scottypres/Arduino-Paragliding-Varios/Sparkfun ESP32 WROOM Vario/KiCAD Files/Buzzer PCB V2/DXFs/Buzzer PCB-FSilkscreen_raster_600dpi_board_aligned.png

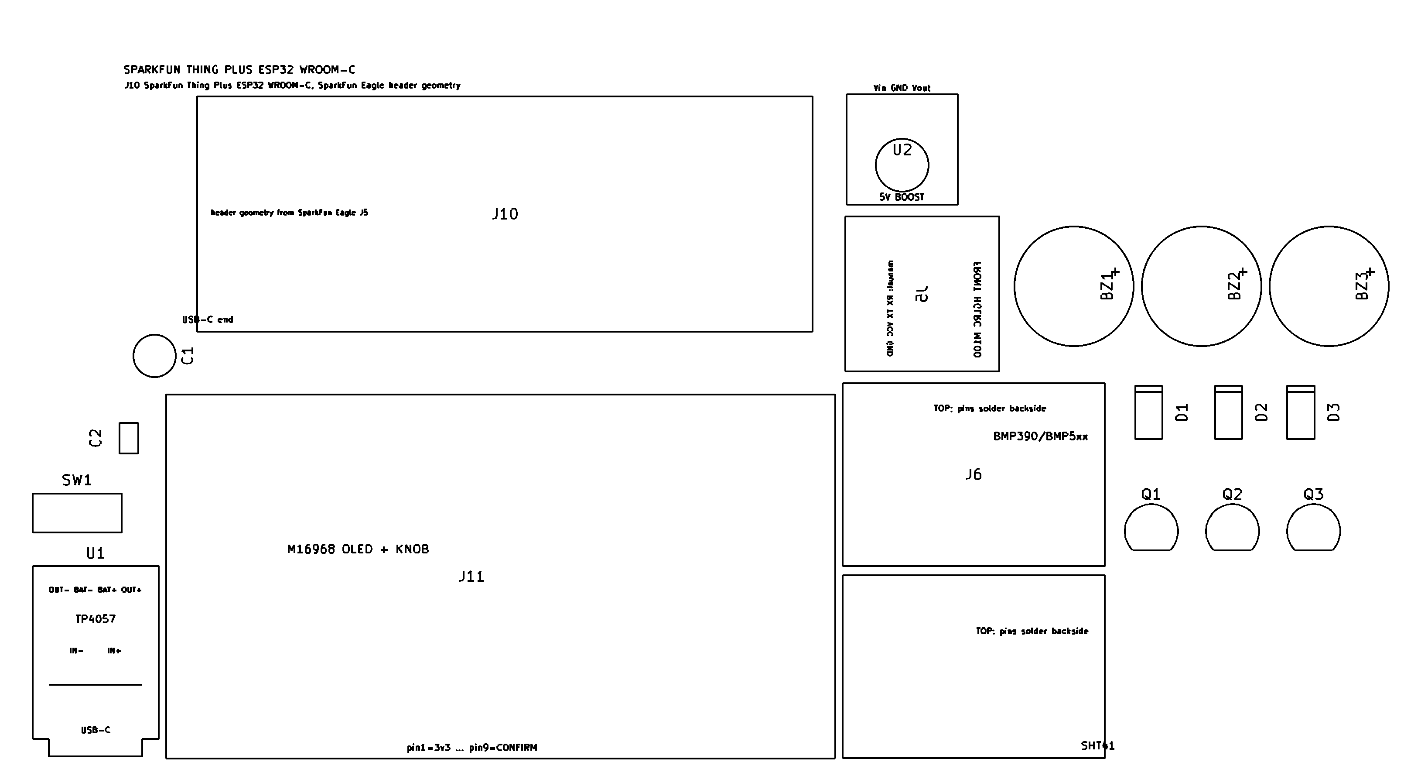
Sparkfun ESP32 WROOM Vario/KiCAD Files/Buzzer PCB V2/DXFs/Buzzer PCB-FSilkscreen_raster_600dpi_board_aligned.png
