scottypres/Arduino-Paragliding-Varios/Sparkfun ESP32 WROOM Vario/KiCAD Files/Buzzer PCB V2/outputs/render/buzzer_v2_top.png

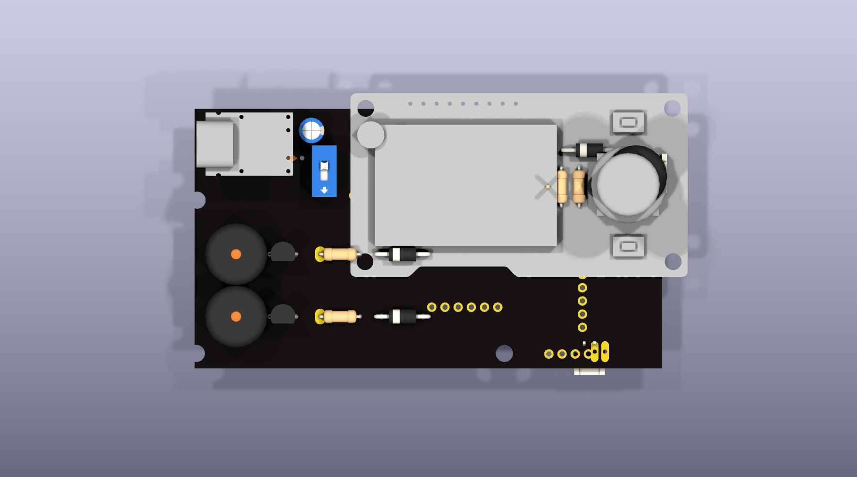
Sparkfun ESP32 WROOM Vario/KiCAD Files/Buzzer PCB V2/outputs/render/buzzer_v2_top.png
