scottypres/Arduino-Paragliding-Varios/Adafruit Feather Mini Vario/KiCAD Files/Component References/HiLetGo TP4057 LiPo_LiIon Charger Drawing HiLetGo TP4057 LiPo LiIon Charger.dxf

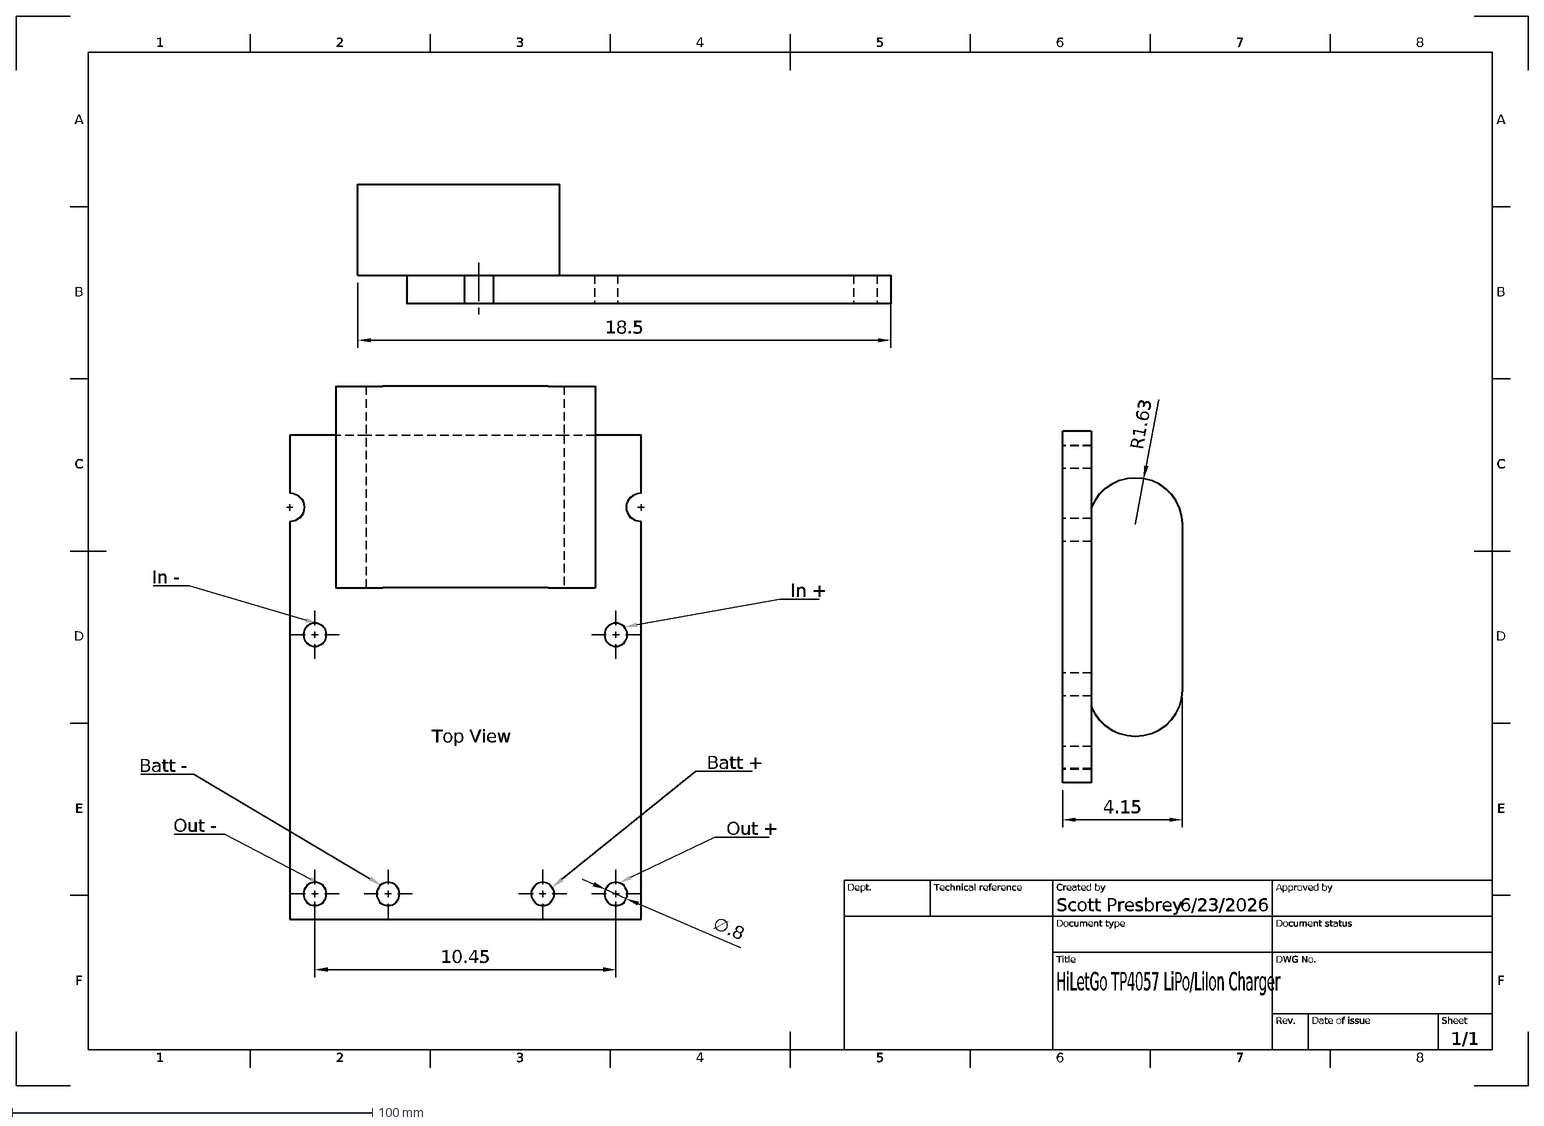
[picture p18: CAD file, 2026-06-23]
Adafruit Feather Mini Vario/KiCAD Files/Component References/HiLetGo TP4057 LiPo_LiIon Charger Drawing HiLetGo TP4057 LiPo LiIon Charger.dxf
1
A
2
3
4
5
6
7
8
B
C
D
E
F
6/23/2026
1/1
HiLetGo TP4057 LiPo/LiIon Charger
Scott Presbrey
Dept.
Technical reference
Created by
Approved by
Document type
Document status
Title
DWG No.
Rev.
Date of issue
Sheet
18.5
4.15
∅.8
R1.63
10.45
Top View
Out -
Batt -
Out +
Batt +
In +
In -
