scottypres/Arduino-Paragliding-Varios/Adafruit Feather Mini Vario/KiCAD Files/Component References/SparkFun 6DoF LSM6DSV16X Qwiic/SparkFun_6DoF_LSM6DSV16X_Qwiic_1x1in_board.step

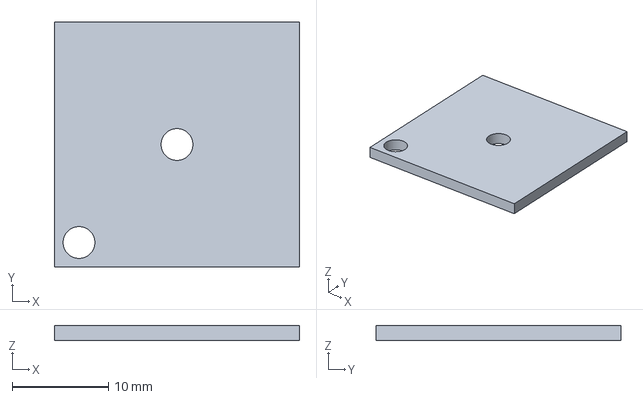
[picture p19: CAD file, 2026-06-27]
Adafruit Feather Mini Vario/KiCAD Files/Component References/SparkFun 6DoF LSM6DSV16X Qwiic/SparkFun_6DoF_LSM6DSV16X_Qwiic_1x1in_board.step
25.4 x 25.4 x 1.60 mm
