scottypres/Arduino-Paragliding-Varios/Sparkfun ESP32 WROOM Vario/3D Printed Case/Top (X2D).3mf

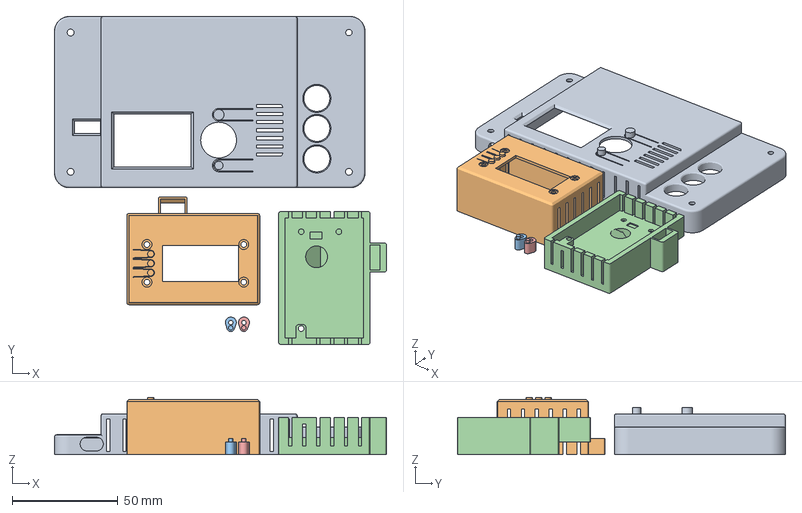
[picture p20: CAD file, 2026-07-03]
Sparkfun ESP32 WROOM Vario/3D Printed Case/Top (X2D).3mf
156.9 x 155.0 x 27.1 mm
3D Printed Case TOP.stl
Feather Case Top.stl
Feather Standoff.stl x 2
Feather Case Bottom.stl
