scottypres/Arduino-Paragliding-Varios/Sparkfun ESP32 WROOM Vario/KiCAD Files/Buzzer PCB V2/DXFs/Buzzer PCB-Edge_Cuts.dxf

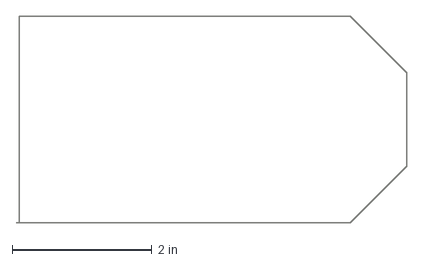
[picture p21: CAD file, 2026-06-26]
Sparkfun ESP32 WROOM Vario/KiCAD Files/Buzzer PCB V2/DXFs/Buzzer PCB-Edge_Cuts.dxf
5.58 x 2.95 in
