scottypres/Arduino-Paragliding-Varios/Sparkfun ESP32 WROOM Vario/KiCAD Files/Buzzer PCB V2/FlatCAM/DXF/Buzzer PCB-NPTH-drl_map.dxf

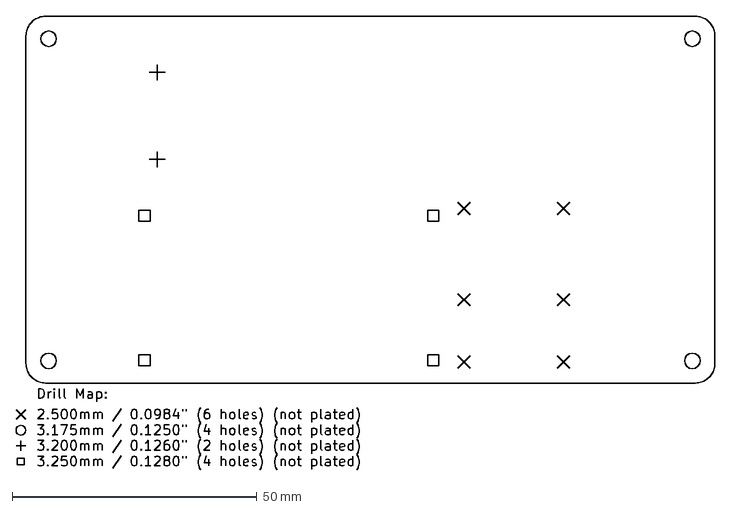
[picture p22: CAD file, 2026-06-26]
Sparkfun ESP32 WROOM Vario/KiCAD Files/Buzzer PCB V2/FlatCAM/DXF/Buzzer PCB-NPTH-drl_map.dxf
142.7 x 92.6 mm
