scottypres/Arduino-Paragliding-Varios/Sparkfun ESP32 WROOM Vario/KiCAD Files/Buzzer PCB V2/outputs/Buzzer_PCB_2p5mm_NPTH_vector_User4.dxf/Buzzer PCB-NPTH_2_5mm_Vector.dxf

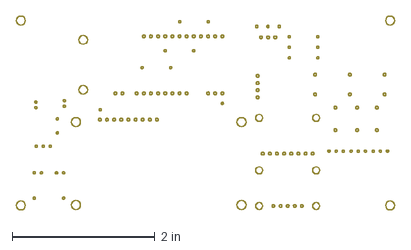
[picture p23: CAD file, 2026-06-26]
Sparkfun ESP32 WROOM Vario/KiCAD Files/Buzzer PCB V2/outputs/Buzzer_PCB_2p5mm_NPTH_vector_User4.dxf/Buzzer PCB-NPTH_2_5mm_Vector.dxf
5.30 x 2.72 in
