scottypres/Arduino-Paragliding-Varios/Sparkfun ESP32 WROOM Vario/KiCAD Files/Buzzer PCB V2/outputs/combined_dxf_parts/Buzzer PCB-Edge_Cuts.dxf

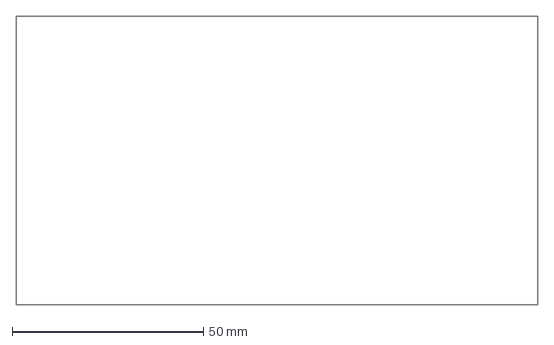
[picture p24: CAD file, 2026-06-25]
Sparkfun ESP32 WROOM Vario/KiCAD Files/Buzzer PCB V2/outputs/combined_dxf_parts/Buzzer PCB-Edge_Cuts.dxf
136.3 x 75.3 mm
