scottypres/Arduino-Paragliding-Varios/Sparkfun ESP32 WROOM Vario/KiCAD Files/Buzzer PCB V2/outputs/dxf_hole_test/Buzzer PCB-F_Cu.dxf

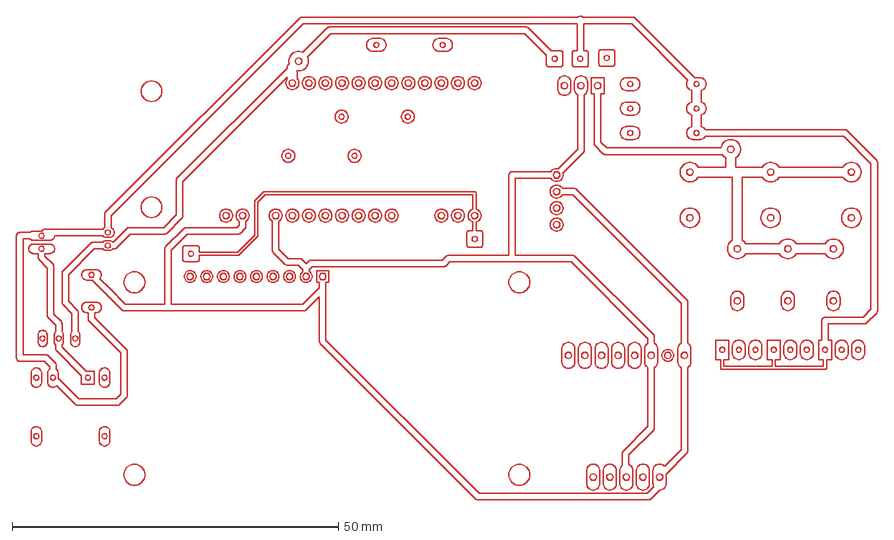
[picture p26: CAD file, 2026-06-25]
Sparkfun ESP32 WROOM Vario/KiCAD Files/Buzzer PCB V2/outputs/dxf_hole_test/Buzzer PCB-F_Cu.dxf
132.0 x 74.2 mm
