scottypres/Arduino-Paragliding-Varios/Sparkfun ESP32 WROOM Vario/KiCAD Files/Buzzer PCB V3 (rerouting traces)/DXFs/Sketch4.dxf

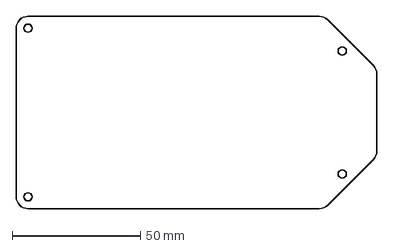
[picture p27: CAD file, 2026-06-26]
Sparkfun ESP32 WROOM Vario/KiCAD Files/Buzzer PCB V3 (rerouting traces)/DXFs/Sketch4.dxf
140.7 x 75.0 mm
