scottypres/Arduino-Paragliding-Varios/Sparkfun ESP32 WROOM Vario/KiCAD Files/Buzzer PCB V3 (rerouting traces)/FlatCAM/Buzzer PCB V3 (rerouted traces)-PTH-drl_map.dxf

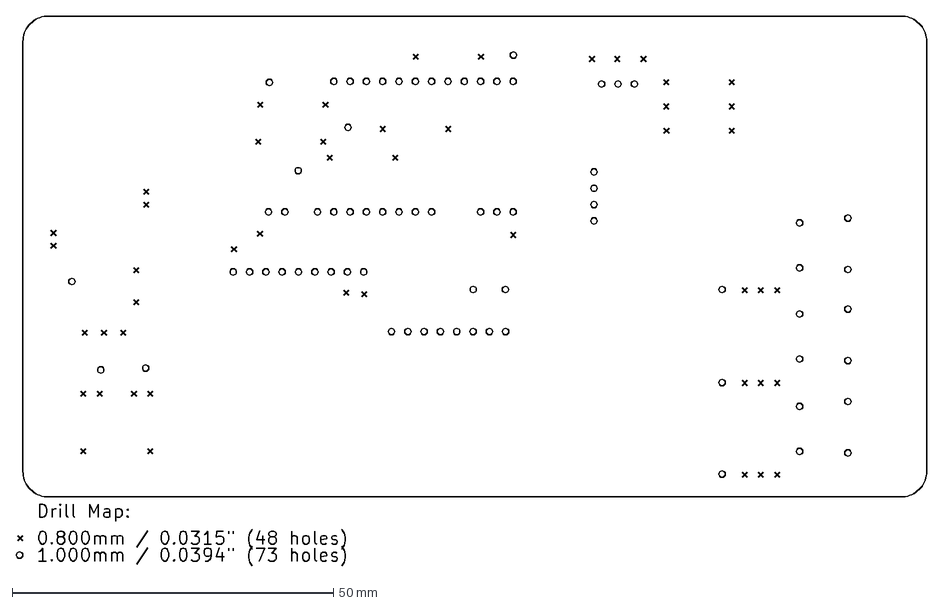
[picture p28: CAD file, 2026-06-28]
Sparkfun ESP32 WROOM Vario/KiCAD Files/Buzzer PCB V3 (rerouting traces)/FlatCAM/Buzzer PCB V3 (rerouted traces)-PTH-drl_map.dxf
141.7 x 85.6 mm
