scottypres/Arduino-Paragliding-Varios/Sparkfun ESP32 WROOM Vario/KiCAD Files/Buzzer PCB V3 (rerouting traces)/outputs/step_after_a1_battery_divider.step

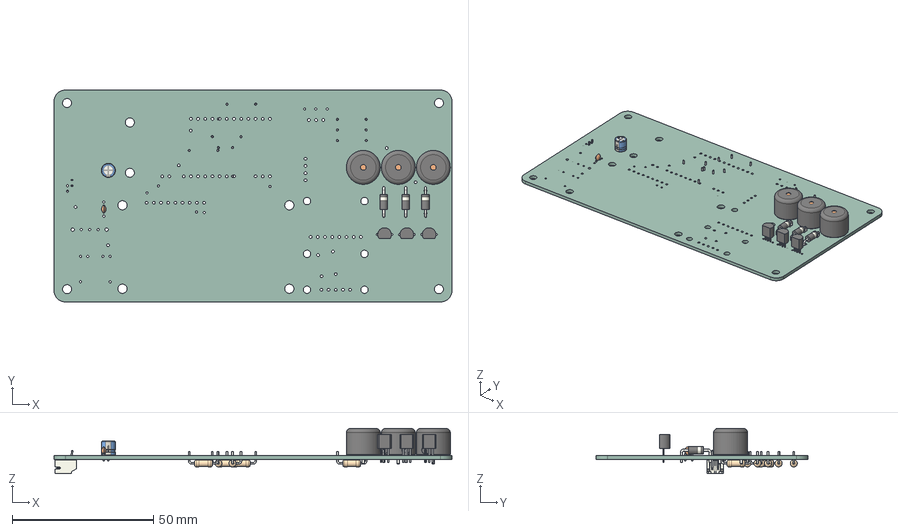
[picture p29: CAD file, 2026-06-27]
Sparkfun ESP32 WROOM Vario/KiCAD Files/Buzzer PCB V3 (rerouting traces)/outputs/step_after_a1_battery_divider.step
140.7 x 74.9 x 16.0 mm
TO-92_Inline_Narrow x 3
C_Disc_D30mm_W16mm_P250mm
D_DO-41_SOD81_P10.16mm_Horizontal x 3
Buzzer_12x95RM76 x 3
CP_Radial_D50mm_P200mm
R_Axial_DIN0207_L63mm_D25mm_P1016mm_Horizontal x 8
JST_S2B_PH_K
Buzzer PCB V3 (rerouted traces)_PCB
