scottypres/Arduino-Paragliding-Varios/Sparkfun ESP32 WROOM Vario/KiCAD Files/Component References/Comidox 5V Booster Board.step

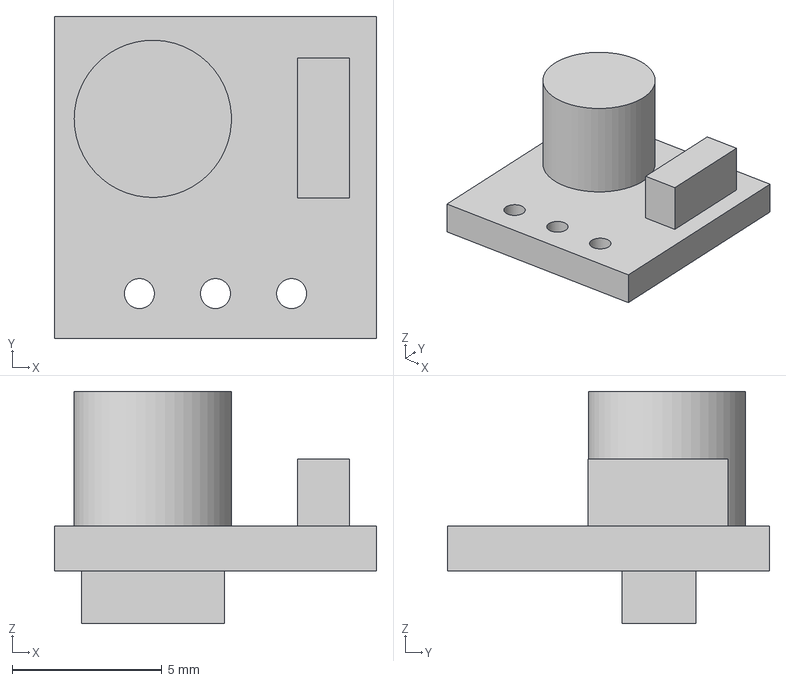
[picture p30: CAD file, 2026-06-23]
Sparkfun ESP32 WROOM Vario/KiCAD Files/Component References/Comidox 5V Booster Board.step
10.8 x 10.8 x 7.75 mm
