scottypres/Arduino-Paragliding-Varios/Adafruit Feather Mini Vario/CAD Files/261 JST PH 2-pin Connector Reference/JST_PH_B2B-PH-K_1x02_P2.00mm_Vertical.step

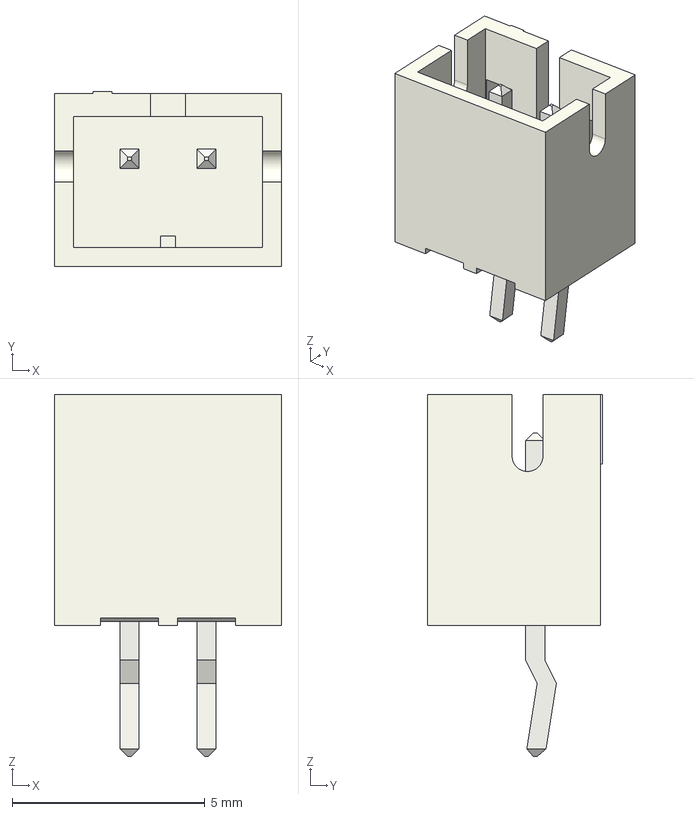
[picture p31: CAD file, 2026-06-20]
Adafruit Feather Mini Vario/CAD Files/261 JST PH 2-pin Connector Reference/JST_PH_B2B-PH-K_1x02_P2.00mm_Vertical.step
5.90 x 4.55 x 9.40 mm
