scottypres/Arduino-Paragliding-Varios/Adafruit Feather Mini Vario/CAD Files/2940 Short Feather Headers - Generic PinSocket Reference/PinSocket_1x12_P2.54mm_Vertical.step

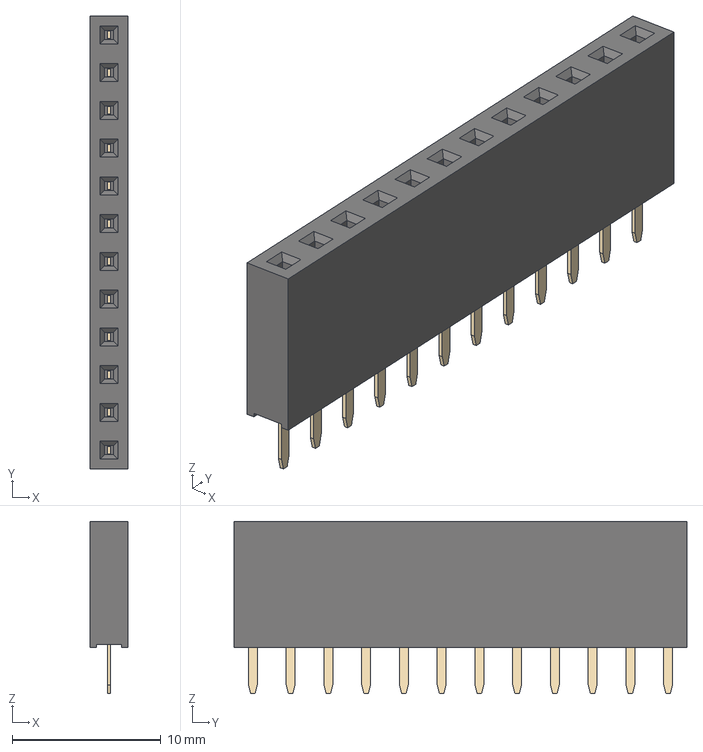
[picture p32: CAD file, 2026-06-20]
Adafruit Feather Mini Vario/CAD Files/2940 Short Feather Headers - Generic PinSocket Reference/PinSocket_1x12_P2.54mm_Vertical.step
2.54 x 30.5 x 11.6 mm
