scottypres/Arduino-Paragliding-Varios/Adafruit Feather Mini Vario/CAD Files/3299 M2.5 Standoff Reference/files/hex-standoff_head.stl

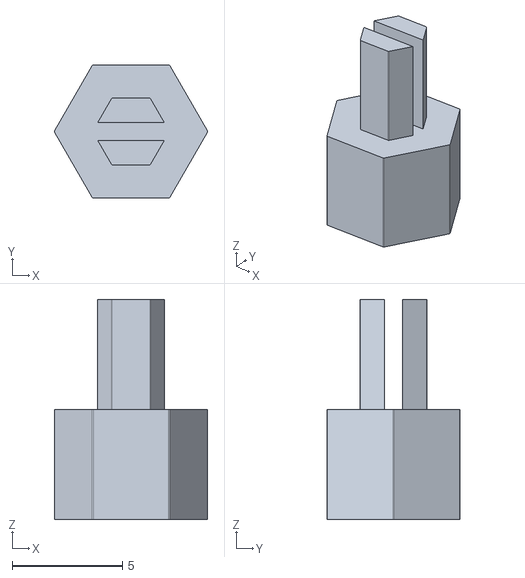
[picture p33: CAD file, 2026-06-20]
Adafruit Feather Mini Vario/CAD Files/3299 M2.5 Standoff Reference/files/hex-standoff_head.stl
6.96 x 6.06 x 10.0
