scottypres/Arduino-Paragliding-Varios/Adafruit Feather Mini Vario/CAD Files/4210_4399 STEMMA QT Cable Connector Reference/JST_SH_SM04B-SRSS-TB_1x04-1MP_P1.00mm_Horizontal.step

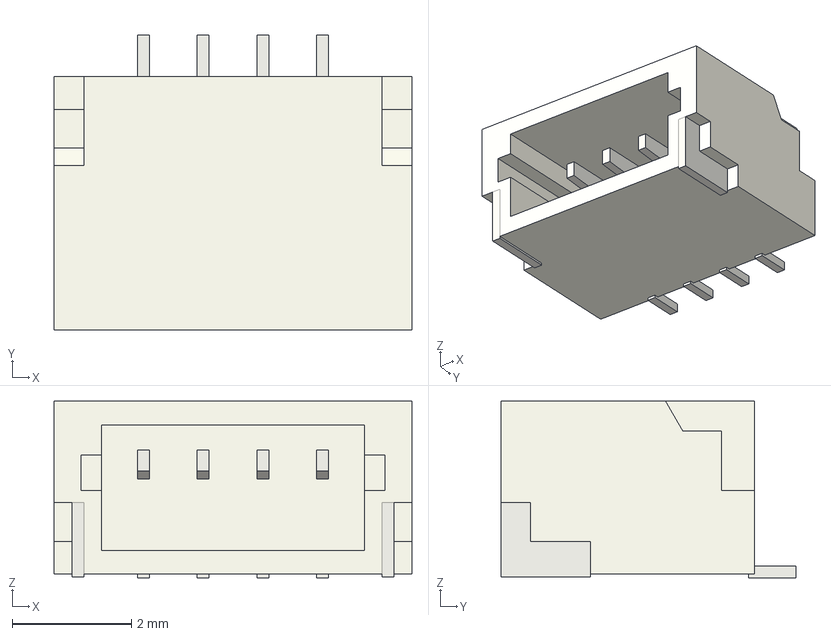
[picture p35: CAD file, 2026-06-20]
Adafruit Feather Mini Vario/CAD Files/4210_4399 STEMMA QT Cable Connector Reference/JST_SH_SM04B-SRSS-TB_1x04-1MP_P1.00mm_Horizontal.step
6.00 x 4.95 x 2.96 mm
