scottypres/Arduino-Paragliding-Varios/Adafruit Feather Mini Vario/CAD Files/4210_4399 STEMMA QT Qwiic JST SH Cables/4210 STEMMA QT Qwiic JST SH 4-pin cable 100mm simplified.step

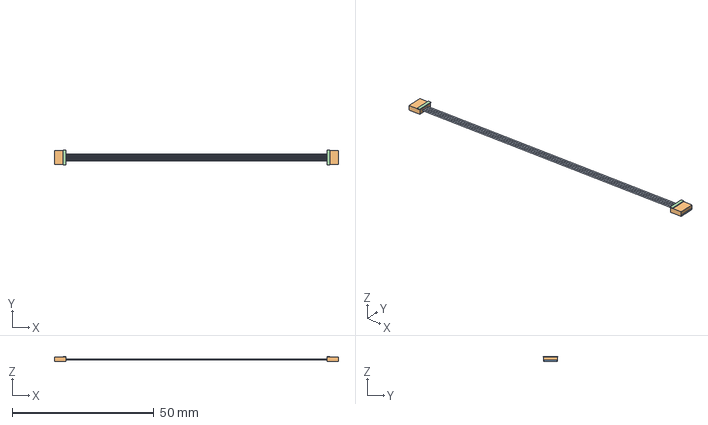
[picture p36: CAD file, 2026-06-20]
Adafruit Feather Mini Vario/CAD Files/4210_4399 STEMMA QT Qwiic JST SH Cables/4210 STEMMA QT Qwiic JST SH 4-pin cable 100mm simplified.step
100.0 x 5.30 x 1.77 mm
