scottypres/Arduino-Paragliding-Varios/Adafruit Feather Mini Vario/CAD Files/Standard 2.54mm Male Headers/PinHeader_1x12_P2.54mm_Vertical.step

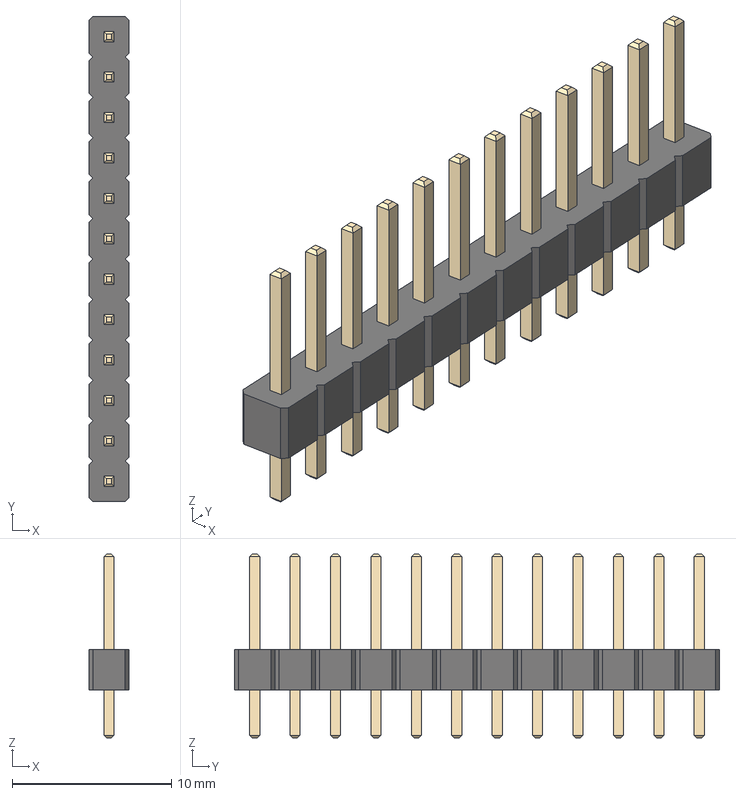
[picture p37: CAD file, 2026-06-20]
Adafruit Feather Mini Vario/CAD Files/Standard 2.54mm Male Headers/PinHeader_1x12_P2.54mm_Vertical.step
2.54 x 30.5 x 11.5 mm
