scottypres/Arduino-Paragliding-Varios/Adafruit Feather Mini Vario/KiCAD Files/Buzzer PCB/STEP/PCB_with_models.step

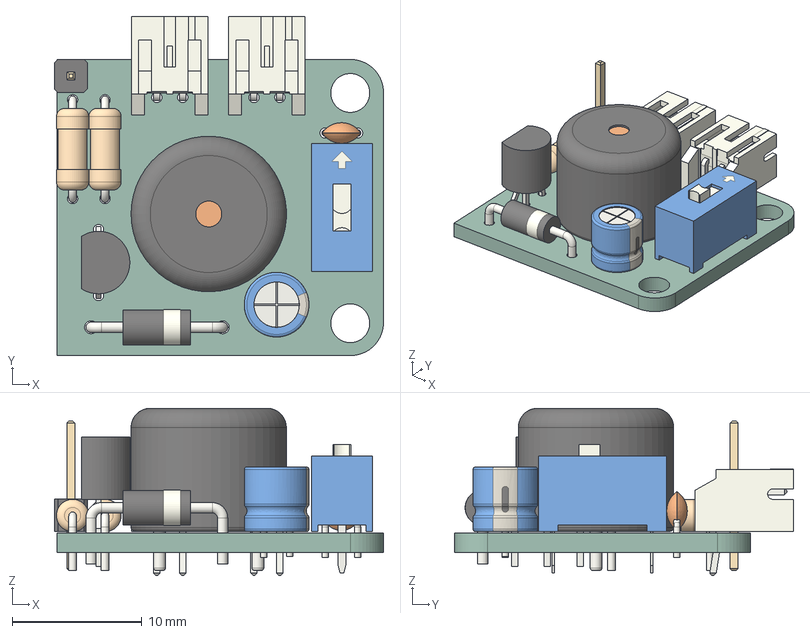
[picture p39: CAD file, 2026-06-21]
Adafruit Feather Mini Vario/KiCAD Files/Buzzer PCB/STEP/PCB_with_models.step
25.4 x 26.2 x 12.9 mm
PinHeader_1x01_P254mm_Vertical
CP_Radial_D50mm_P200mm
C_Disc_D30mm_W16mm_P250mm
R_Axial_DIN0207_L63mm_D25mm_P762mm_Horizontal x 2
SW_DIP_SPSTx01_Slide_978x472mm_W762mm_P254mm
JST_S2B_PH_K x 2
TO-92_Inline_Wide
D_DO-41_SOD81_P10.16mm_Horizontal
Buzzer_12x95RM76
Buzzer PCB_PCB
