scottypres/Arduino-Paragliding-Varios/Adafruit Feather Mini Vario/KiCAD Files/Component References/HiLetGo TP4057 LiPo_LiIon Charger.step

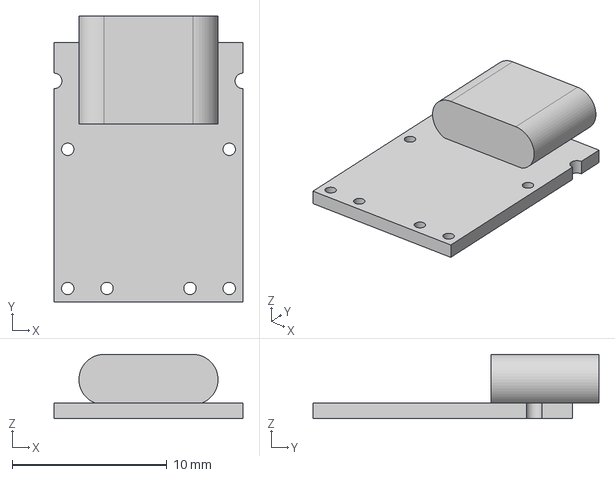
[picture p40: CAD file, 2026-06-23]
Adafruit Feather Mini Vario/KiCAD Files/Component References/HiLetGo TP4057 LiPo_LiIon Charger.step
12.2 x 18.5 x 4.15 mm
