scottypres/Arduino-Paragliding-Varios/Sparkfun ESP32 WROOM Vario/3D Printed Case/Bottom (P1P).3mf

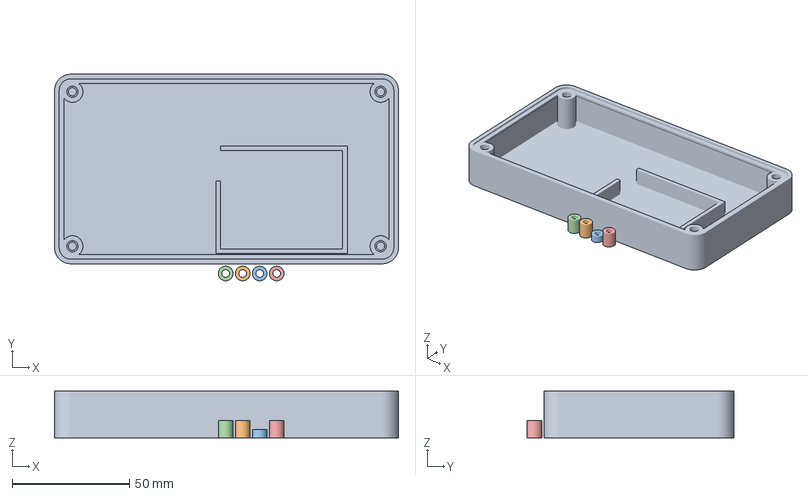
[picture p41: CAD file, 2026-06-28]
Sparkfun ESP32 WROOM Vario/3D Printed Case/Bottom (P1P).3mf
146.7 x 88.1 x 20.0 mm
3D Printed Case.stl_10
3D Printed Case.stl_14
3D Printed Case.stl_15
3D Printed Case.stl_12
3D Printed Case.stl_13
