scottypres/Arduino-Paragliding-Varios/Sparkfun ESP32 WROOM Vario/KiCAD Files/Buzzer PCB V2/FlatCAM/DXF/Buzzer PCB-PTH-drl_map.dxf

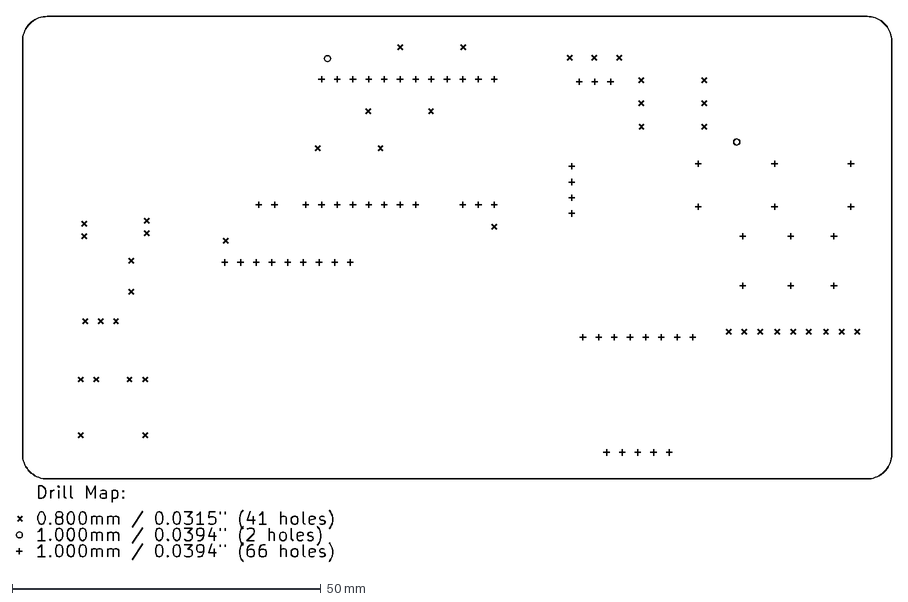
[picture p42: CAD file, 2026-06-26]
Sparkfun ESP32 WROOM Vario/KiCAD Files/Buzzer PCB V2/FlatCAM/DXF/Buzzer PCB-PTH-drl_map.dxf
141.7 x 88.3 mm
