scottypres/Arduino-Paragliding-Varios/Sparkfun ESP32 WROOM Vario/KiCAD Files/Buzzer PCB V3 (rerouting traces)/FlatCAM/Buzzer PCB V3 (rerouted traces)-NPTH-drl_map.dxf

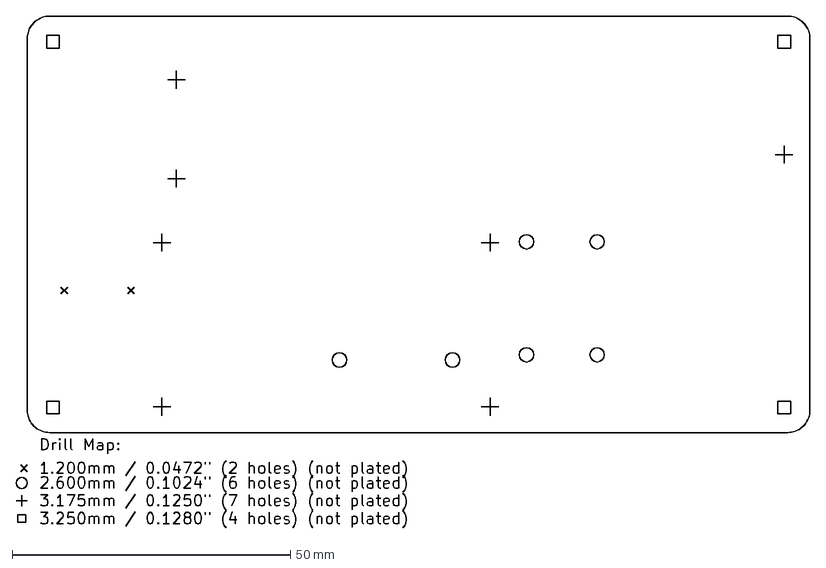
[picture p43: CAD file, 2026-06-28]
Sparkfun ESP32 WROOM Vario/KiCAD Files/Buzzer PCB V3 (rerouting traces)/FlatCAM/Buzzer PCB V3 (rerouted traces)-NPTH-drl_map.dxf
142.7 x 92.0 mm
