scottypres/Arduino-Paragliding-Varios/Adafruit Feather Mini Vario/CAD Files/3299 M2.5 Standoff Reference/files/hex-standoff_foot.stl

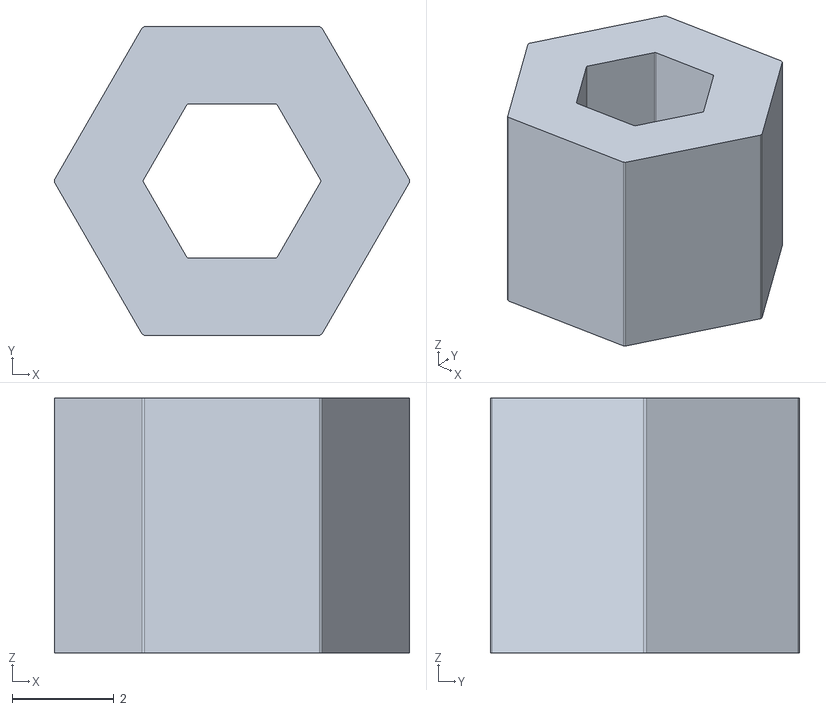
[picture p44: CAD file, 2026-06-20]
Adafruit Feather Mini Vario/CAD Files/3299 M2.5 Standoff Reference/files/hex-standoff_foot.stl
6.96 x 6.06 x 5.00
