scottypres/Arduino-Paragliding-Varios/Adafruit Feather Mini Vario/KiCAD Files/Component References/Comidox 5V Booster Board Drawing Sheet1.dxf

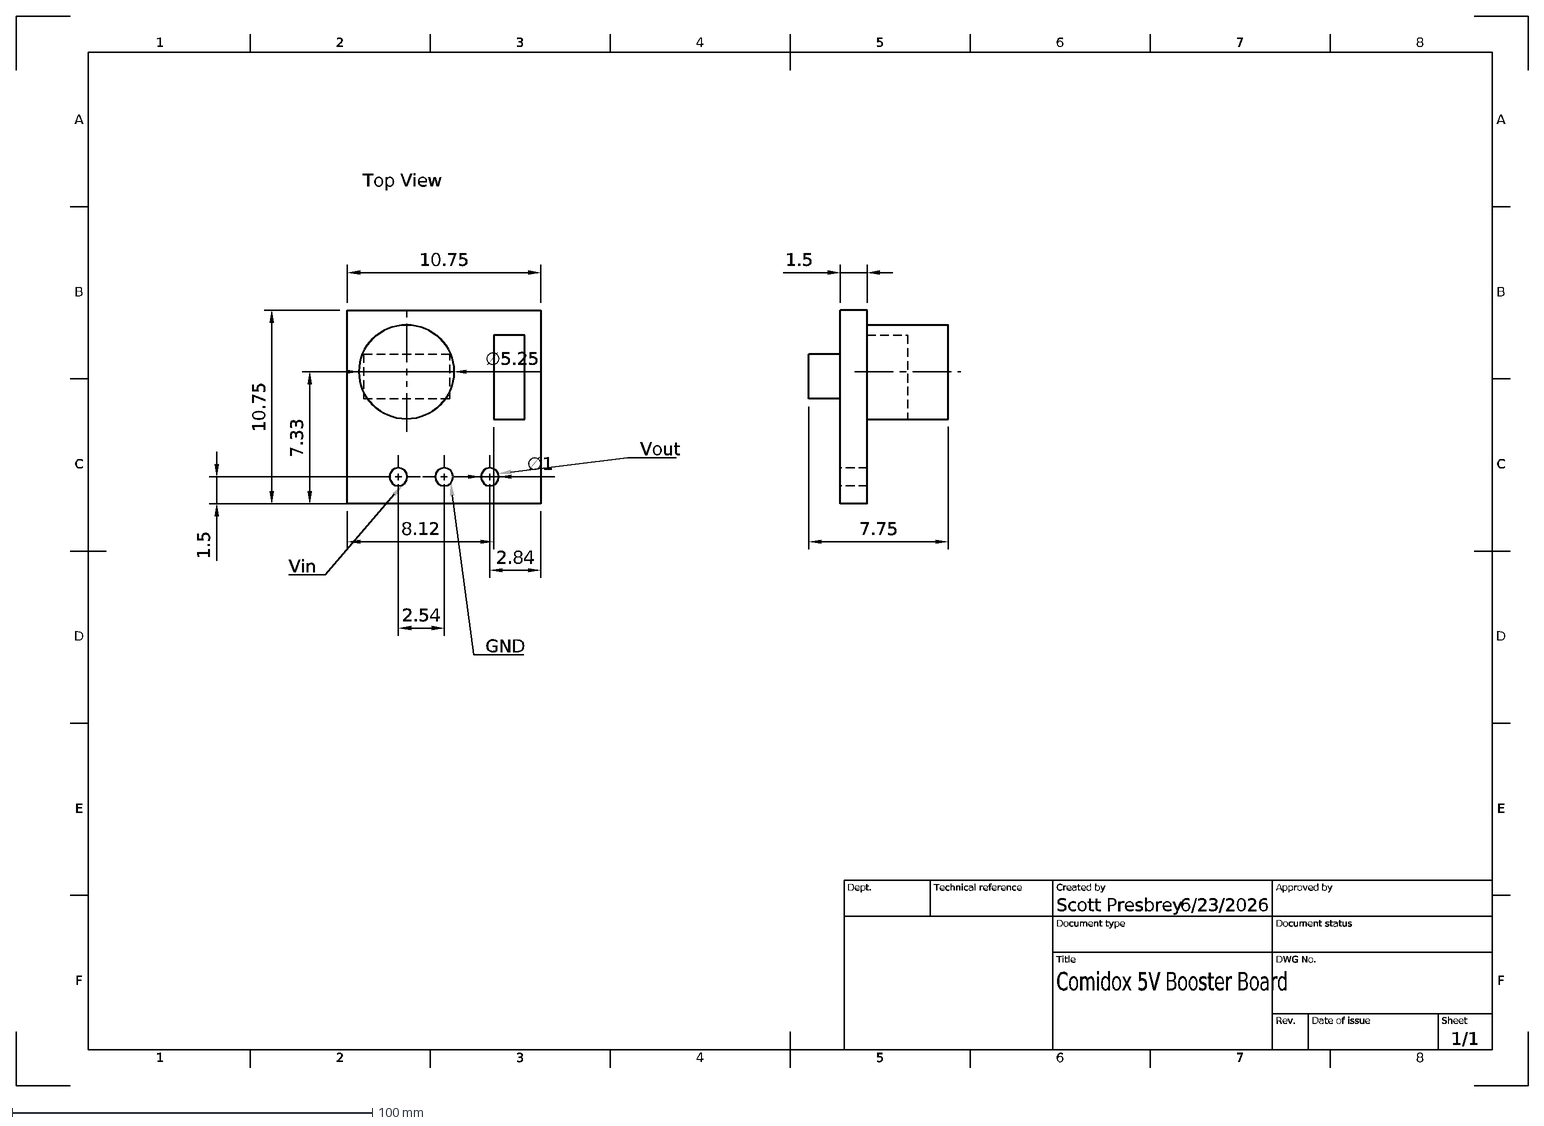
[picture p47: CAD file, 2026-06-23]
Adafruit Feather Mini Vario/KiCAD Files/Component References/Comidox 5V Booster Board Drawing Sheet1.dxf
1
A
2
3
4
5
6
7
8
B
C
D
E
F
6/23/2026
1/1
Comidox 5V Booster Board
Scott Presbrey
Dept.
Technical reference
Created by
Approved by
Document type
Document status
Title
DWG No.
Rev.
Date of issue
Sheet
Top View
10.75
2.54
1.5
2.84
Vin
GND
Vout
7.75
∅1
∅5.25
8.12
7.33
