scottypres/Arduino-Paragliding-Varios/Sparkfun ESP32 WROOM Vario/KiCAD Files/Buzzer PCB V2/DXFs/Buzzer PCB-NPTH-holes-only.dxf

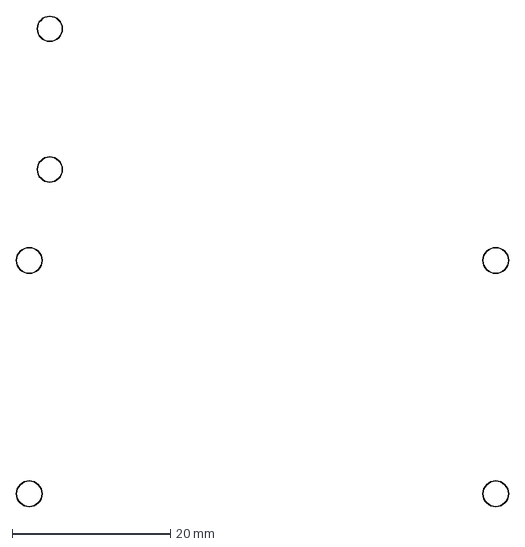
[picture p48: CAD file, 2026-06-25]
Sparkfun ESP32 WROOM Vario/KiCAD Files/Buzzer PCB V2/DXFs/Buzzer PCB-NPTH-holes-only.dxf
62.2 x 62.0 mm
