scottypres/Arduino-Paragliding-Varios/Sparkfun ESP32 WROOM Vario/KiCAD Files/Component References/WWZMDiB SD TF Card Adaptor - SPI - Arduino.step

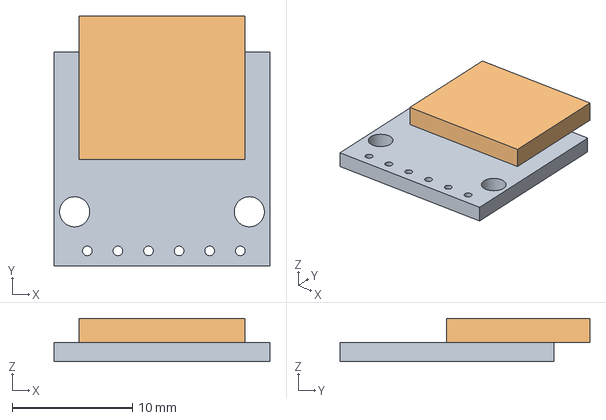
[picture p50: CAD file, 2026-06-23]
Sparkfun ESP32 WROOM Vario/KiCAD Files/Component References/WWZMDiB SD TF Card Adaptor - SPI - Arduino.step
17.9 x 20.8 x 3.60 mm
