scottypres/Arduino-Paragliding-Varios/Adafruit Feather Mini Vario/CAD Files/3299 M2.5 Standoff Reference/M2.5 female-female hex standoff 8mm.step

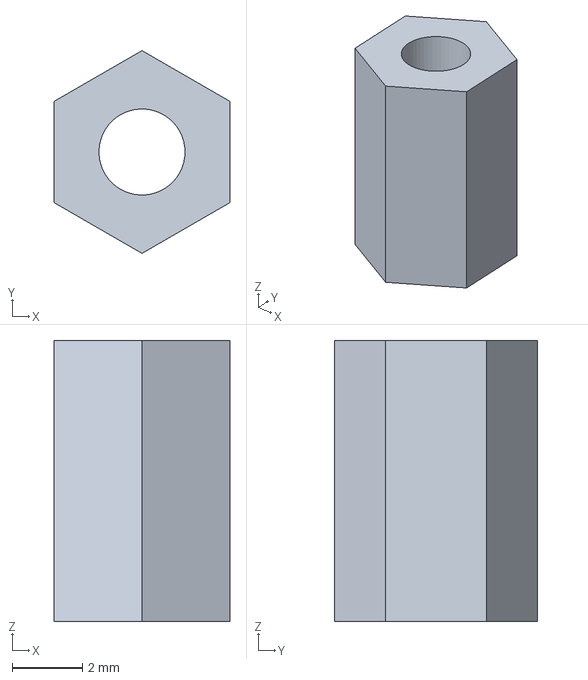
[picture p51: CAD file, 2026-06-20]
Adafruit Feather Mini Vario/CAD Files/3299 M2.5 Standoff Reference/M2.5 female-female hex standoff 8mm.step
5.00 x 5.77 x 8.00 mm
