scottypres/Arduino-Paragliding-Varios/Sparkfun ESP32 WROOM Vario/KiCAD Files/Buzzer PCB V3 (rerouting traces)/DXFs/Buzzer PCB-ALL-holes-only.dxf

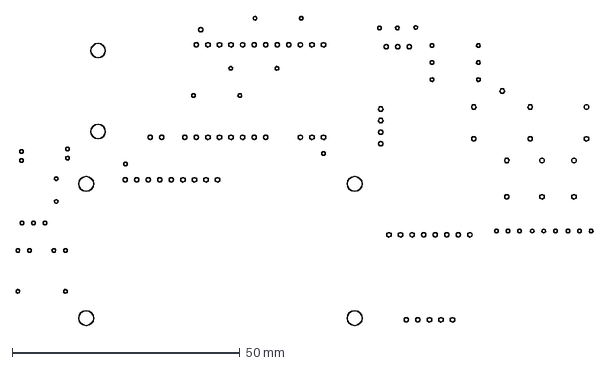
[picture p52: CAD file, 2026-06-25]
Sparkfun ESP32 WROOM Vario/KiCAD Files/Buzzer PCB V3 (rerouting traces)/DXFs/Buzzer PCB-ALL-holes-only.dxf
126.8 x 67.9 mm
