scottypres/Arduino-Paragliding-Varios/Sparkfun ESP32 WROOM Vario/KiCAD Files/Component References/WWZMDiB SD TF Card Adaptor - SPI - Arduino Drawing Sheet1.dxf

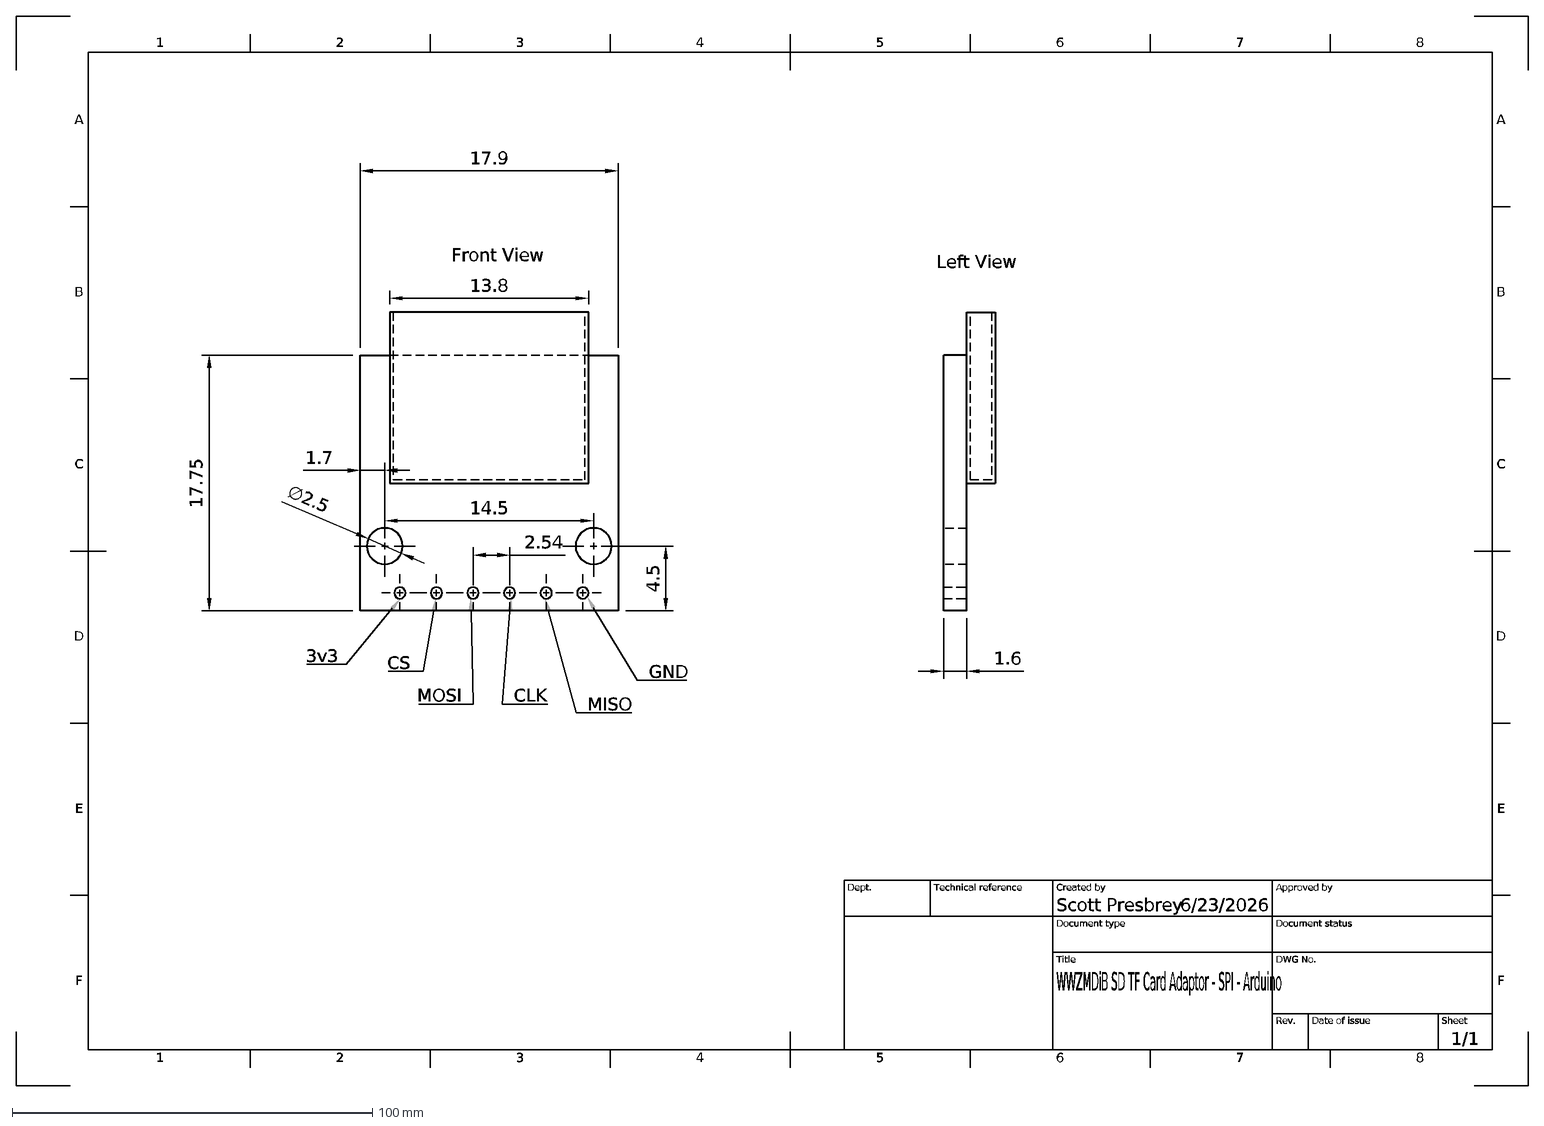
[picture p53: CAD file, 2026-06-23]
Sparkfun ESP32 WROOM Vario/KiCAD Files/Component References/WWZMDiB SD TF Card Adaptor - SPI - Arduino Drawing Sheet1.dxf
1
A
2
3
4
5
6
7
8
B
C
D
E
F
6/23/2026
1/1
WWZMDiB SD TF Card Adaptor - SPI - Arduino
Scott Presbrey
Dept.
Technical reference
Created by
Approved by
Document type
Document status
Title
DWG No.
Rev.
Date of issue
Sheet
3v3
CS
MOSI
CLK
MISO
GND
Front View
Left View
17.75
17.9
13.8
1.6
∅2.5
1.7
14.5
4.5
2.54
