scottypres/Arduino-Paragliding-Varios/Adafruit Feather Mini Vario/CAD Files/3299 M2.5 Standoff Reference/M2.5 male-female hex standoff 6mm body.step

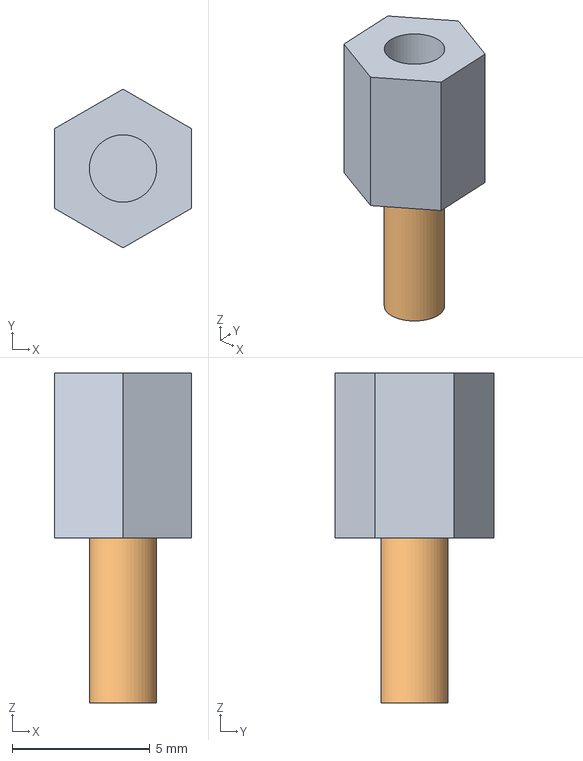
[picture p54: CAD file, 2026-06-20]
Adafruit Feather Mini Vario/CAD Files/3299 M2.5 Standoff Reference/M2.5 male-female hex standoff 6mm body.step
5.00 x 5.77 x 12.0 mm
