scottypres/Arduino-Paragliding-Varios/Sparkfun ESP32 WROOM Vario/KiCAD Files/Buzzer PCB V3 (rerouting traces)/DXFs/Buzzer PCB-NPTH-drl_map.dxf

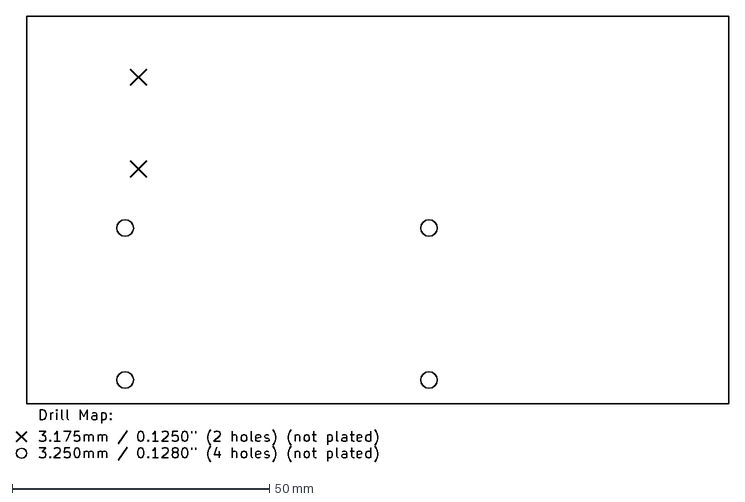
[picture p55: CAD file, 2026-06-25]
Sparkfun ESP32 WROOM Vario/KiCAD Files/Buzzer PCB V3 (rerouting traces)/DXFs/Buzzer PCB-NPTH-drl_map.dxf
138.3 x 86.6 mm
