scottypres/Arduino-Paragliding-Varios/Sparkfun ESP32 WROOM Vario/KiCAD Files/Buzzer PCB V2/DXFs/Buzzer PCB-PTH-drl_map.dxf

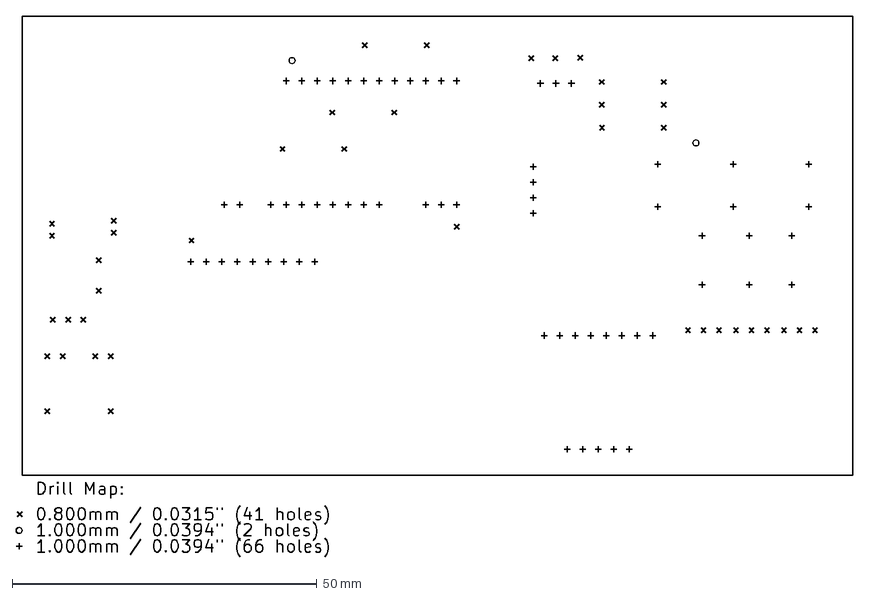
[picture p57: CAD file, 2026-06-25]
Sparkfun ESP32 WROOM Vario/KiCAD Files/Buzzer PCB V2/DXFs/Buzzer PCB-PTH-drl_map.dxf
137.3 x 88.7 mm
