scottypres/Arduino-Paragliding-Varios/Adafruit Feather Mini Vario/KiCAD Files/Component References/6313 OLED FeatherWing EagleCAD/Adafruit 128x64 OLED FeatherWing.brd

## EAGLE design Adafruit Feather Mini Vario/KiCAD Files/Component References/6313 OLED FeatherWing EagleCAD/Adafruit 128x64 OLED FeatherWing.brd (2026-06-20)

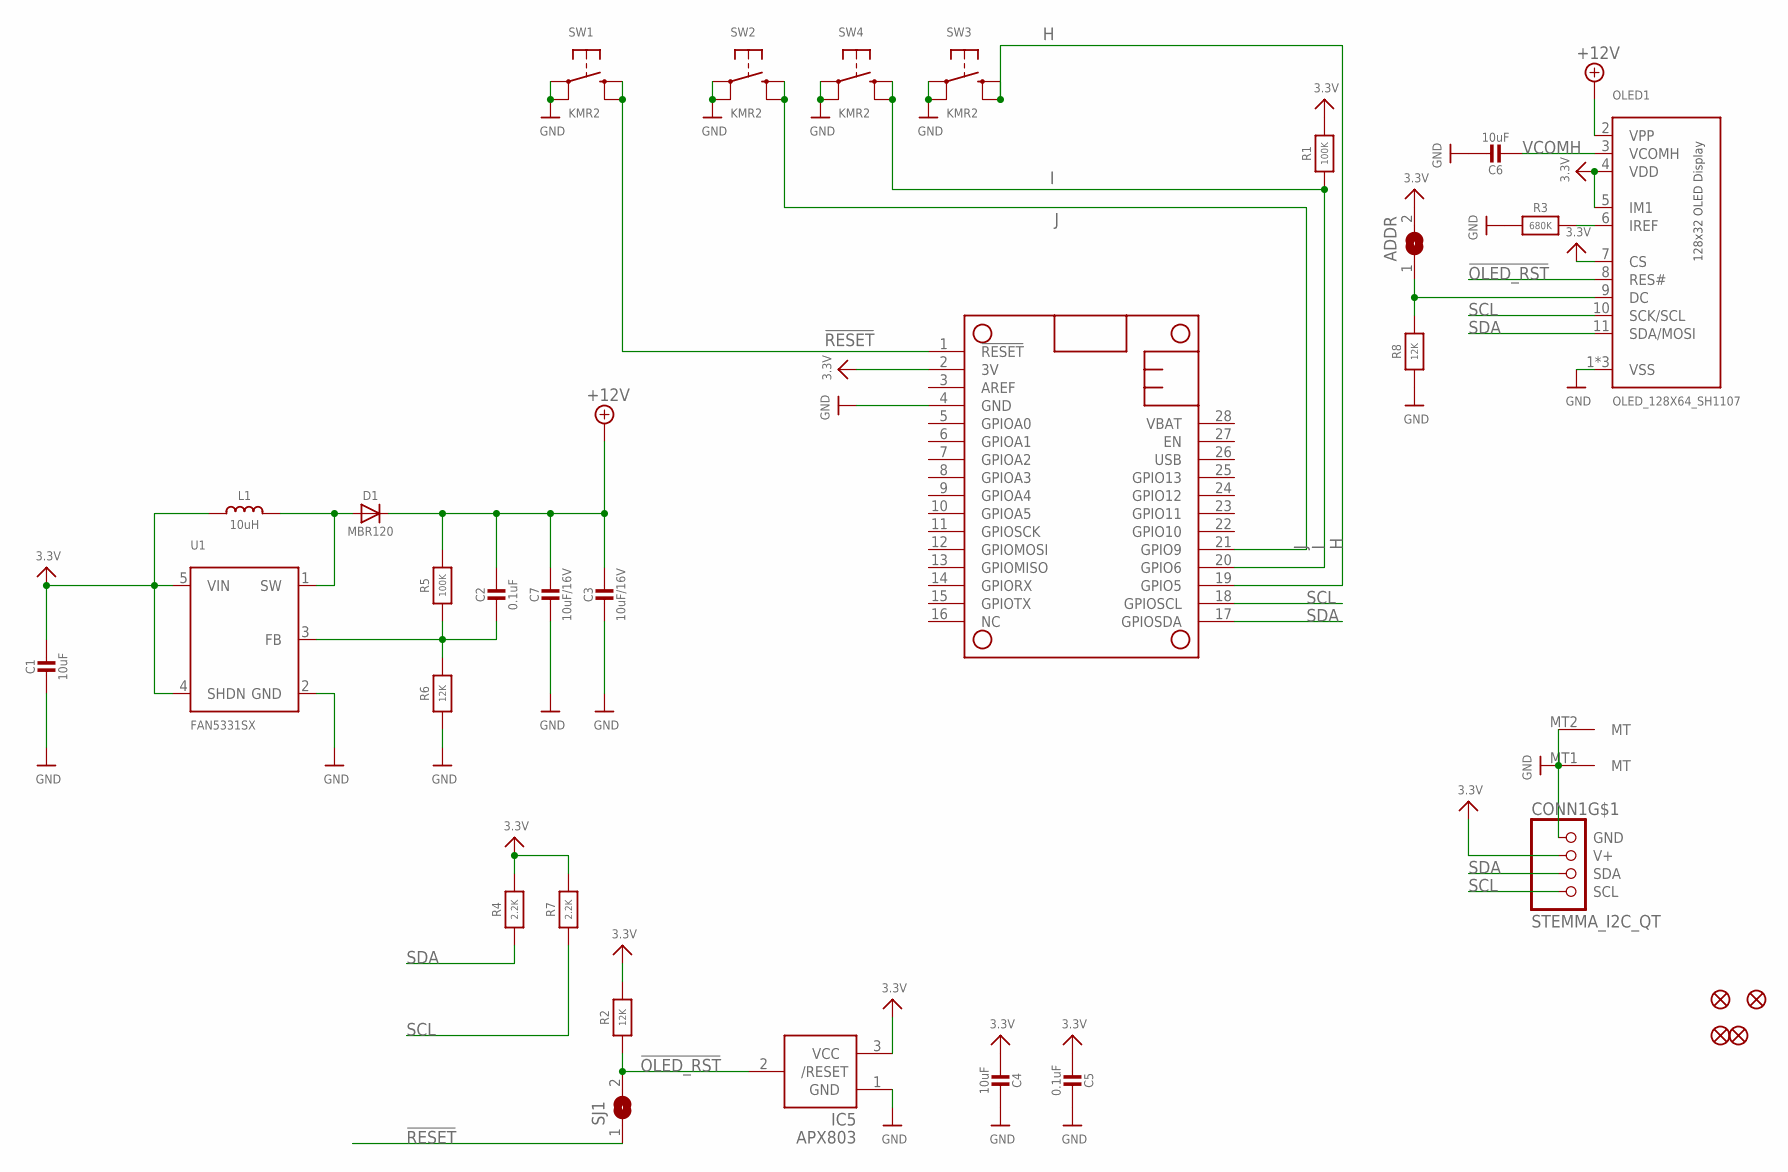
[picture p83: schematic Adafruit 128x64 OLED FeatherWing.sch]

Parts:
ADDR: SOLDERJUMPER; SOLDERJUMPER_ARROW_NOPASTE
C1, C4, C6: 10uF; 0805-NO
C2, C5: 0.1uF; 0603-NO
C3, C7: 10uF/16V; 0805-NO
CONN1: STEMMA_I2C_QT; JST_SH4
D1: MBR120; SOD-123
FID1, FID2, FID3, FID4: FIDUCIAL_1MM
IC5: APX803; SOT23
L1: 10uH; INDUCTOR_1007
MS1: FEATHERWING_NODIM
OLED1: OLED_128X64_SH1107; QT1107P11A
R1, R5: 100K; 0603-NO
R2, R6, R8: 12K; 0603-NO
R3: 680K; 0603-NO
R4, R7: 2.2K; 0603-NO
SJ1: SOLDERJUMPERCLOSED; SOLDERJUMPER_CLOSEDWIRE
SW1, SW2, SW3, SW4: KMR2; BTN_KMR2_4.6X2.8
U1: FAN5331SX; SOT23-5

Connections:
3.3V: ADDR.2, C1.1, C4.2, C5.2, CONN1.2 (V+), IC5.3 (VCC), L1.P$1 (1), MS1.2 (3V), OLED1.4 (VDD), OLED1.5 (IM1), OLED1.7 (CS), R1.2, R2.2, R4.2, R7.2, U1.4 (SHDN), U1.5 (VIN)
!OLED_RST: IC5.2 (/RESET), OLED1.8 (RES#), R2.1, SJ1.2
!RESET: MS1.1 (!RESET), SJ1.1, SW1.B (S), SW1.B' (S1)
+12V: C2.1, C3.1, C7.1, D1.C, OLED1.2 (VPP), R5.2
GND: C1.2, C3.2, C4.1, C5.1, C6.1, C7.2, CONN1.1 (GND), CONN1.MT1 (MT), CONN1.MT2 (MT), IC5.1 (GND), MS1.4 (GND), OLED1.1 (VSS), OLED1.12 (VSS), OLED1.13 (VSS), R3.1, R6.1, R8.1, SW1.A, SW1.A' (P1), SW2.A, SW2.A' (P1), SW3.A, SW3.A' (P1), SW4.A, SW4.A' (P1), U1.2 (GND)
H: MS1.19 (GPIO5), SW3.B (S), SW3.B' (S1)
I: MS1.20 (GPIO6), R1.1, SW4.B (S), SW4.B' (S1)
J: MS1.21 (GPIO9), SW2.B (S), SW2.B' (S1)
unnamed: D1.A, L1.P$2 (2), U1.1 (SW)
unnamed: ADDR.1, OLED1.9 (DC), R8.2
unnamed: C2.2, R5.1, R6.2, U1.3 (FB)
unnamed: OLED1.6 (IREF), R3.2
SCL: CONN1.4 (SCL), MS1.18 (GPIOSCL), OLED1.10 (SCK/SCL), R7.1
SDA: CONN1.3 (SDA), MS1.17 (GPIOSDA), OLED1.11 (SDA/MOSI), R4.1
VCOMH: C6.2, OLED1.3 (VCOMH)

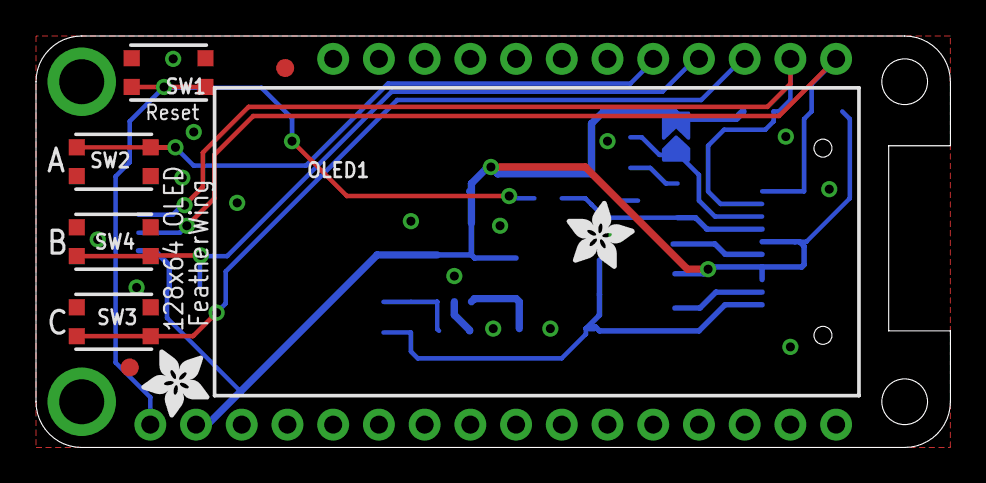
[picture p84: board Adafruit 128x64 OLED FeatherWing.brd from above]

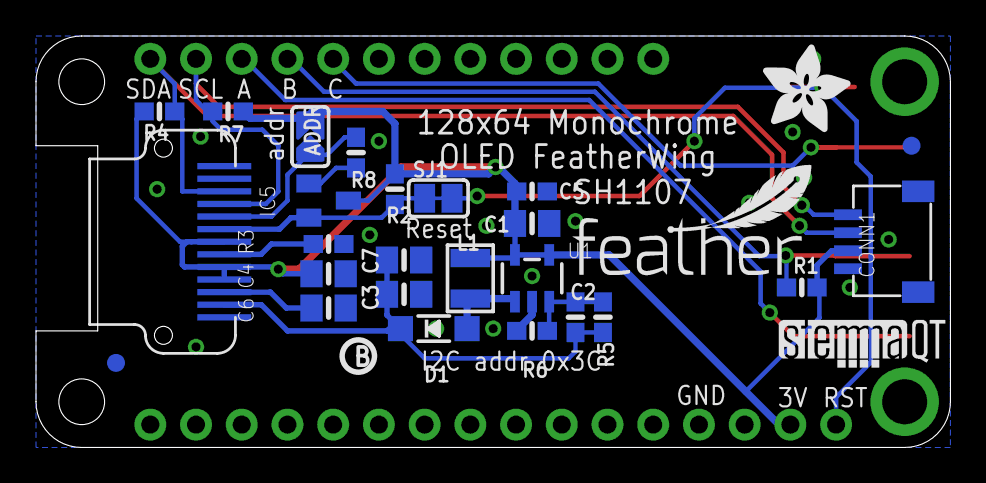
[picture p85: board Adafruit 128x64 OLED FeatherWing.brd from below]

Board: 2 copper layers, 50.8 x 22.9 mm, 38 parts (28 on the bottom side), 15 nets.

Other parts of the board:
U$8: ADAFRUIT_5MM
U$14: PCBFEAT-REV-040
U$16, U$37: ADAFRUIT_3.5MM
U$35: STEMMAQT
U$36: FEATHERLOGO_SMALL
