scottypres/Arduino-Paragliding-Varios/Adafruit Feather Mini Vario/KiCAD Files/Component References/SparkFun_Qwiic_OLED_1.3in/Hardware/Production/Qwiic_OLED_1.3in-Panel.brd

## EAGLE design Adafruit Feather Mini Vario/KiCAD Files/Component References/SparkFun_Qwiic_OLED_1.3in/Hardware/Production/Qwiic_OLED_1.3in-Panel.brd (2026-06-28)

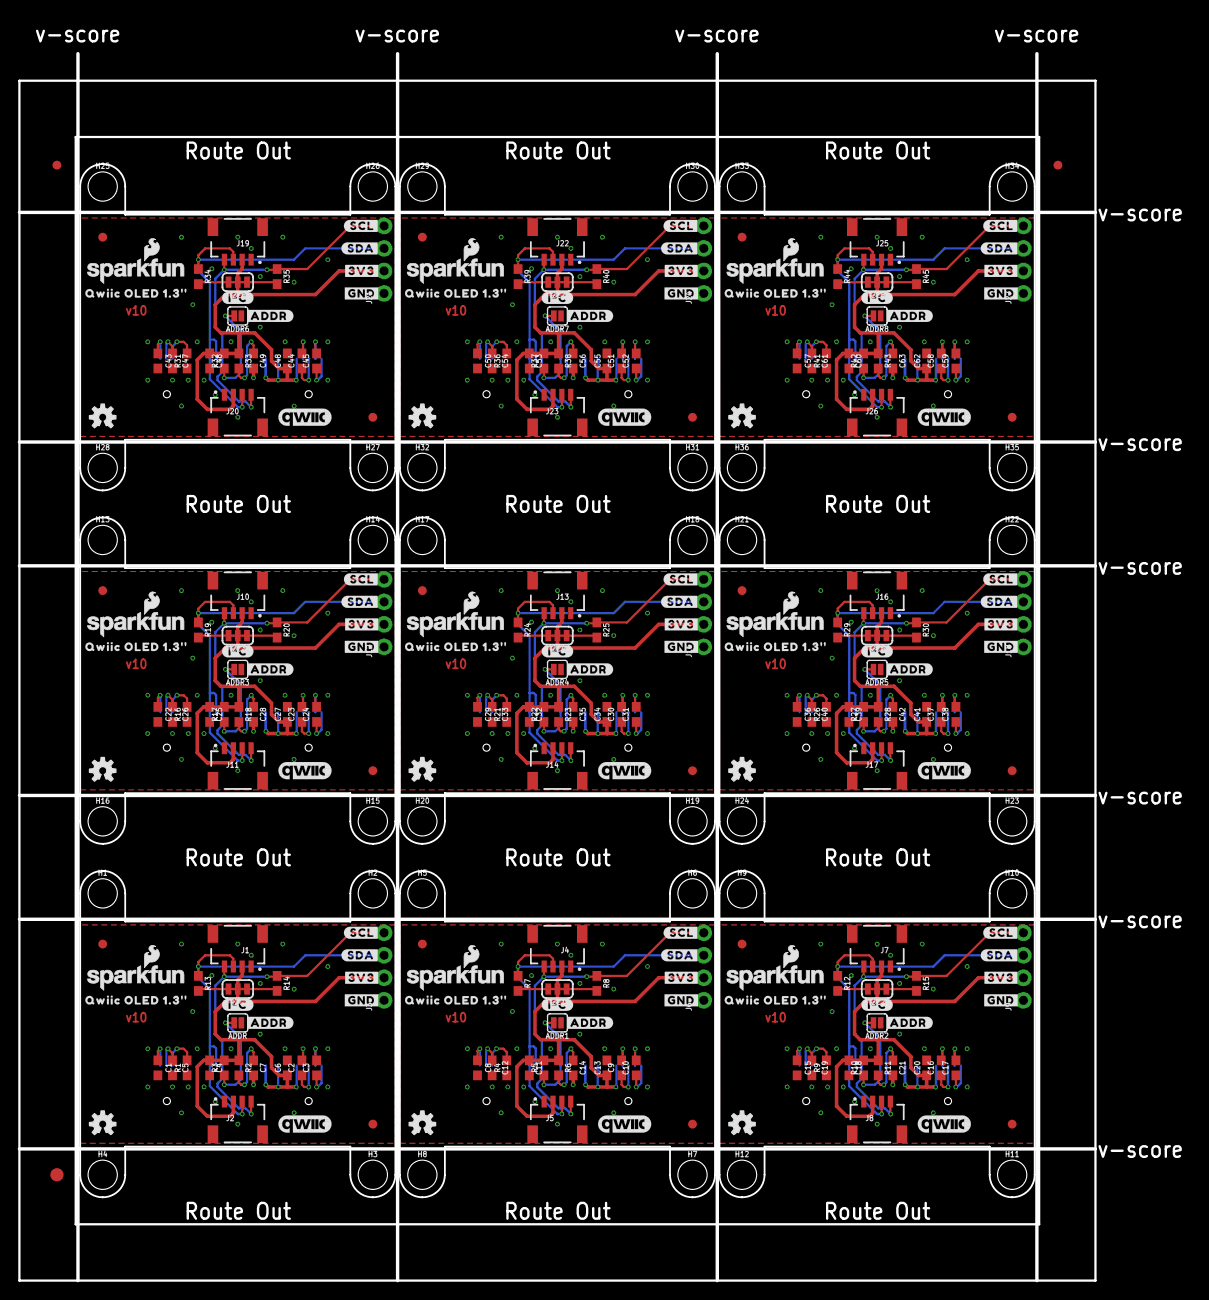
[picture p86: board Qwiic_OLED_1.3in-Panel.brd from above]

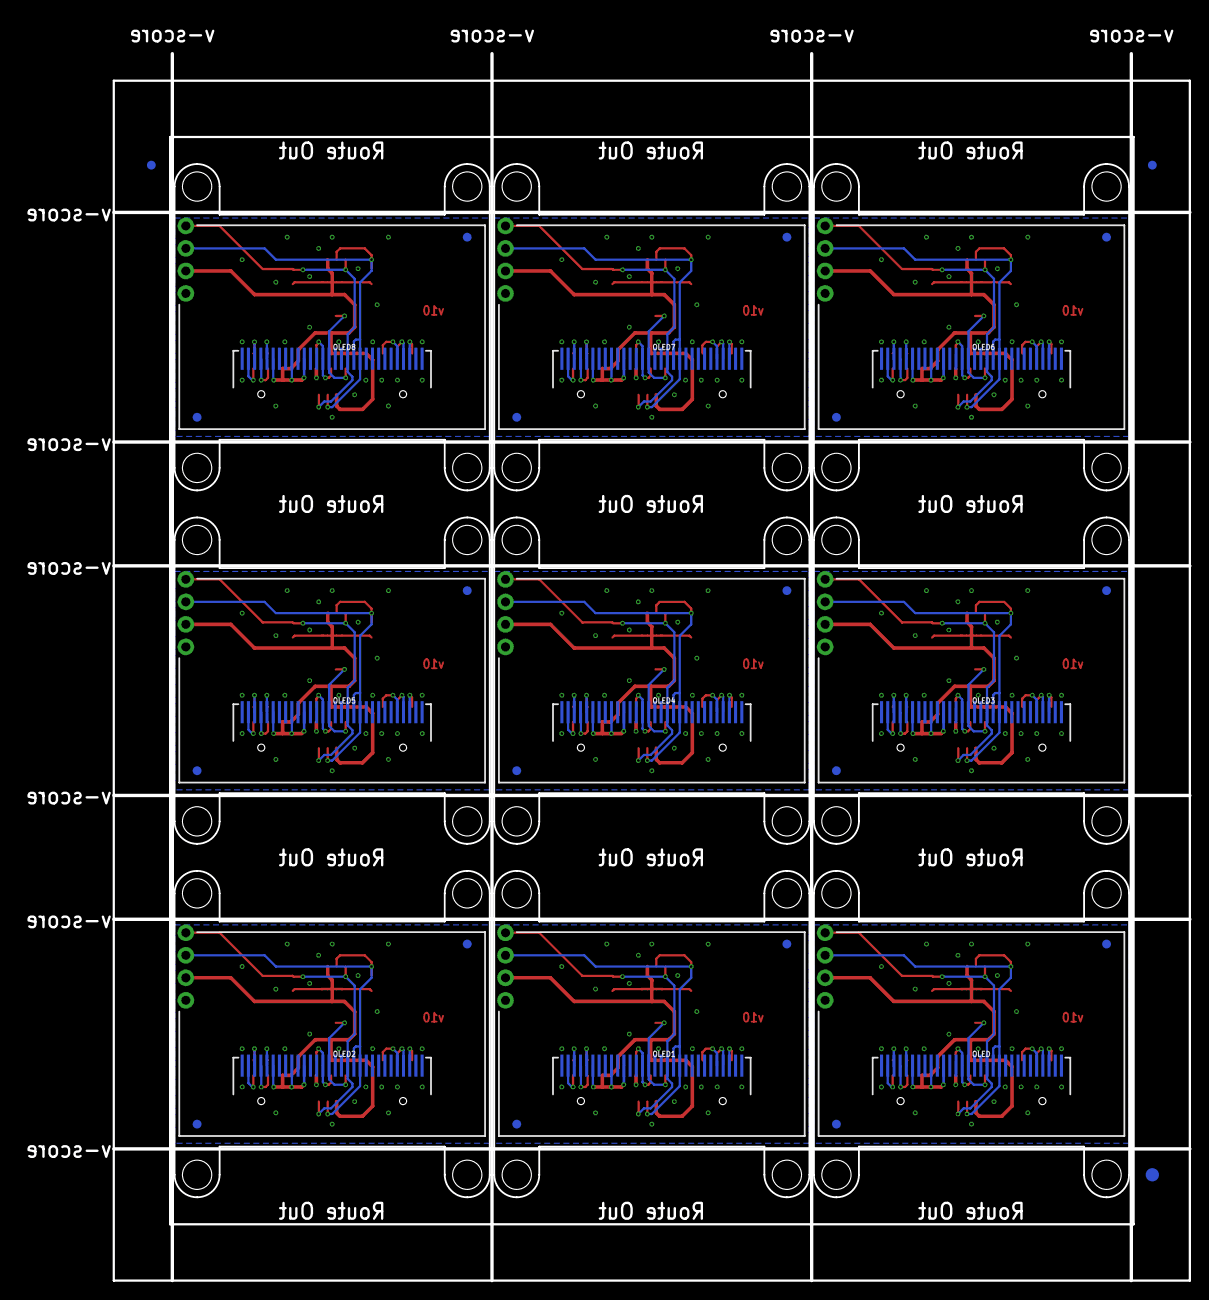
[picture p87: board Qwiic_OLED_1.3in-Panel.brd from below]

Board: 2 copper layers, 121.4 x 138.4 mm, 330 parts (30 on the bottom side), 135 nets.

Parts:
ADDR, ADDR1, ADDR2, ADDR3, ADDR4, ADDR5, ADDR6, ADDR7, ADDR8: JUMPER-SMT_2_NO_SILK; SMT-JUMPER_2_NO_SILK
C1, C8, C15, C22, C29, C36, C43, C50, C57: 2.2uF; 0603
C2, C3, C4, C6, C7, C9, C10, C11, C13, C14, C16, C17, C18, C20, C21, C23, C24, C25, C27, C28, C30, C31, C32, C34, C35, C37, C38, C39, C41, C42, C44, C45, C46, C48, C49, C51, C52, C53, C55, C56, C58, C59, C60, C62, C63: 1.0uF; 0603
C5, C12, C19, C26, C33, C40, C47, C54, C61: 4.7uF; 0603
E$1, E$2, E$3, E$4: FIDUCIAL-1X2
E$5, E$6: FIDUCIAL-1.5X3
FID1, FID2, FID3, FID4, FID5, FID6, FID7, FID8, FID9, FID10, FID11, FID12, FID13, FID14, FID15, FID16, FID17, FID18, FID19, FID20, FID21, FID22, FID23, FID24, FID25, FID26, FID27, FID28, FID29, FID30, FID31, FID32, FID33, FID34, FID35, FID36: FIDUCIAL1X2; FIDUCIAL-1X2
H1, H2, H3, H4, H5, H6, H7, H8, H9, H10, H11, H12, H13, H14, H15, H16, H17, H18, H19, H20, H21, H22, H23, H24, H25, H26, H27, H28, H29, H30, H31, H32, H33, H34, H35, H36: STAND-OFF
I2C, I2C1, I2C2, I2C3, I2C4, I2C5, I2C6, I2C7, I2C8: JUMPER-SMT_3_2-NC_TRACE_SILK; SMT-JUMPER_3_2-NC_TRACE_SILK
J1, J2, J4, J5, J7, J8, J10, J11, J13, J14, J16, J17, J19, J20, J22, J23, J25, J26: QWIIC_RIGHT_ANGLE; JST04_1MM_RA
J3, J6, J9, J12, J15, J18, J21, J24, J27: 1X04_NO_SILK
LOGO1, LOGO6, LOGO9, LOGO12, LOGO15, LOGO18, LOGO21, LOGO24, LOGO27: QWIIC_LOGO_6MM; QWIIC_6MM
LOGO2, LOGO3, LOGO7, LOGO10, LOGO13, LOGO16, LOGO19, LOGO22, LOGO25: OSHW-LOGOS; OSHW-LOGO-S
LOGO4, LOGO5, LOGO8, LOGO11, LOGO14, LOGO17, LOGO20, LOGO23, LOGO26: SFE_LOGO_NAME_FLAME.1_INCH; SFE_LOGO_NAME_FLAME_.1
OLED, OLED1, OLED2, OLED3, OLED4, OLED5, OLED6, OLED7, OLED8: OLED1.3; OLED-1.3-128X64
R1, R4, R9, R16, R21, R26, R31, R36, R41: 390k; 0603
R2, R3, R5, R6, R10, R11, R17, R18, R22, R23, R27, R28, R32, R33, R37, R38, R42, R43: 10k; 0603
R7, R8, R12, R13, R14, R15, R19, R20, R24, R25, R29, R30, R34, R35, R39, R40, R44, R45: 2.2k; 0603
U$1, U$8, U$15, U$22, U$29, U$36, U$43, U$50, U$57: QWIIC_OLED_1#3##0
U$2, U$9, U$16, U$23, U$30, U$37, U$44, U$51, U$58: #I�C#2
U$3, U$10, U$17, U$24, U$31, U$38, U$45, U$52, U$59: #3V3#2
U$4, U$11, U$18, U$25, U$32, U$39, U$46, U$53, U$60: #ADDR#5
U$5, U$12, U$19, U$26, U$33, U$40, U$47, U$54, U$61: #GND#4
U$6, U$13, U$20, U$27, U$34, U$41, U$48, U$55, U$62: #SCL#0
U$7, U$14, U$21, U$28, U$35, U$42, U$49, U$56, U$63: #SDA#1

Connections:
!RESET!: C7.1, OLED.14, R2.2
!RESET!1: C14.1, OLED1.14, R6.2
!RESET!2: C21.1, OLED2.14, R11.2
!RESET!3: C28.1, OLED3.14, R18.2
!RESET!4: C35.1, OLED4.14, R23.2
!RESET!5: C42.1, OLED5.14, R28.2
!RESET!6: C49.1, OLED6.14, R33.2
!RESET!7: C56.1, OLED7.14, R38.2
!RESET!8: C63.1, OLED8.14, R43.2
C1N: C2.2, OLED.5
C1N1: C9.2, OLED1.5
C1N2: C16.2, OLED2.5
C1N3: C23.2, OLED3.5
C1N4: C30.2, OLED4.5
C1N5: C37.2, OLED5.5
C1N6: C44.2, OLED6.5
C1N7: C51.2, OLED7.5
C1N8: C58.2, OLED8.5
C1P: C2.1, OLED.4
C1P1: C9.1, OLED1.4
C1P2: C16.1, OLED2.4
C1P3: C23.1, OLED3.4
C1P4: C30.1, OLED4.4
C1P5: C37.1, OLED5.4
C1P6: C44.1, OLED6.4
C1P7: C51.1, OLED7.4
C1P8: C58.1, OLED8.4
C2N: C3.2, OLED.3
C2N1: C10.2, OLED1.3
C2N2: C17.2, OLED2.3
C2N3: C24.2, OLED3.3
C2N4: C31.2, OLED4.3
C2N5: C38.2, OLED5.3
C2N6: C45.2, OLED6.3
C2N7: C52.2, OLED7.3
C2N8: C59.2, OLED8.3
C2P: C3.1, OLED.2
C2P1: C10.1, OLED1.2
C2P2: C17.1, OLED2.2
C2P3: C24.1, OLED3.2
C2P4: C31.1, OLED4.2
C2P5: C38.1, OLED5.2
C2P6: C45.1, OLED6.2
C2P7: C52.1, OLED7.2
C2P8: C59.1, OLED8.2
D/!C!: ADDR.2, OLED.15, R3.1
D/!C!1: ADDR1.2, OLED1.15, R5.1
D/!C!2: ADDR2.2, OLED2.15, R10.1
D/!C!3: ADDR3.2, OLED3.15, R17.1
D/!C!4: ADDR4.2, OLED4.15, R22.1
D/!C!5: ADDR5.2, OLED5.15, R27.1
D/!C!6: ADDR6.2, OLED6.15, R32.1
D/!C!7: ADDR7.2, OLED7.15, R37.1
D/!C!8: ADDR8.2, OLED8.15, R42.1
GND: ADDR.1, C1.2, C4.2, C5.2, C6.2, C7.2, J1.1, J2.1, J3.1, OLED.1, OLED.8, OLED.10, OLED.12, OLED.13, OLED.16, OLED.17, OLED.21, OLED.22, OLED.23, OLED.24, OLED.25, OLED.29, OLED.30, R1.1
GND1: ADDR1.1, C8.2, C11.2, C12.2, C13.2, C14.2, J4.1, J5.1, J6.1, OLED1.1, OLED1.8, OLED1.10, OLED1.12, OLED1.13, OLED1.16, OLED1.17, OLED1.21, OLED1.22, OLED1.23, OLED1.24, OLED1.25, OLED1.29, OLED1.30, R4.1
GND2: ADDR2.1, C15.2, C18.2, C19.2, C20.2, C21.2, J7.1, J8.1, J9.1, OLED2.1, OLED2.8, OLED2.10, OLED2.12, OLED2.13, OLED2.16, OLED2.17, OLED2.21, OLED2.22, OLED2.23, OLED2.24, OLED2.25, OLED2.29, OLED2.30, R9.1
GND3: ADDR3.1, C22.2, C25.2, C26.2, C27.2, C28.2, J10.1, J11.1, J12.1, OLED3.1, OLED3.8, OLED3.10, OLED3.12, OLED3.13, OLED3.16, OLED3.17, OLED3.21, OLED3.22, OLED3.23, OLED3.24, OLED3.25, OLED3.29, OLED3.30, R16.1
GND4: ADDR4.1, C29.2, C32.2, C33.2, C34.2, C35.2, J13.1, J14.1, J15.1, OLED4.1, OLED4.8, OLED4.10, OLED4.12, OLED4.13, OLED4.16, OLED4.17, OLED4.21, OLED4.22, OLED4.23, OLED4.24, OLED4.25, OLED4.29, OLED4.30, R21.1
GND5: ADDR5.1, C36.2, C39.2, C40.2, C41.2, C42.2, J16.1, J17.1, J18.1, OLED5.1, OLED5.8, OLED5.10, OLED5.12, OLED5.13, OLED5.16, OLED5.17, OLED5.21, OLED5.22, OLED5.23, OLED5.24, OLED5.25, OLED5.29, OLED5.30, R26.1
GND6: ADDR6.1, C43.2, C46.2, C47.2, C48.2, C49.2, J19.1, J20.1, J21.1, OLED6.1, OLED6.8, OLED6.10, OLED6.12, OLED6.13, OLED6.16, OLED6.17, OLED6.21, OLED6.22, OLED6.23, OLED6.24, OLED6.25, OLED6.29, OLED6.30, R31.1
GND7: ADDR7.1, C50.2, C53.2, C54.2, C55.2, C56.2, J22.1, J23.1, J24.1, OLED7.1, OLED7.8, OLED7.10, OLED7.12, OLED7.13, OLED7.16, OLED7.17, OLED7.21, OLED7.22, OLED7.23, OLED7.24, OLED7.25, OLED7.29, OLED7.30, R36.1
GND8: ADDR8.1, C57.2, C60.2, C61.2, C62.2, C63.2, J25.1, J26.1, J27.1, OLED8.1, OLED8.8, OLED8.10, OLED8.12, OLED8.13, OLED8.16, OLED8.17, OLED8.21, OLED8.22, OLED8.23, OLED8.24, OLED8.25, OLED8.29, OLED8.30, R41.1
IREF: OLED.26, R1.2
IREF1: OLED1.26, R4.2
IREF2: OLED2.26, R9.2
IREF3: OLED3.26, R16.2
IREF4: OLED4.26, R21.2
IREF5: OLED5.26, R26.2
IREF6: OLED6.26, R31.2
IREF7: OLED7.26, R36.2
IREF8: OLED8.26, R41.2
unnamed: I2C1.3, R7.2
unnamed: I2C1.1, R8.2
unnamed: I2C2.3, R12.2
unnamed: I2C.3, R13.2
unnamed: I2C.1, R14.2
unnamed: I2C2.1, R15.2
unnamed: I2C3.3, R19.2
unnamed: I2C3.1, R20.2
unnamed: I2C4.3, R24.2
unnamed: I2C4.1, R25.2
unnamed: I2C5.3, R29.2
unnamed: I2C5.1, R30.2
unnamed: I2C6.3, R34.2
unnamed: I2C6.1, R35.2
unnamed: I2C7.3, R39.2
unnamed: I2C7.1, R40.2
unnamed: I2C8.3, R44.2
unnamed: I2C8.1, R45.2
SCL: J1.4, J2.4, J3.4, OLED.18, R14.1
SCL1: J4.4, J5.4, J6.4, OLED1.18, R8.1
SCL2: J7.4, J8.4, J9.4, OLED2.18, R15.1
SCL3: J10.4, J11.4, J12.4, OLED3.18, R20.1
SCL4: J13.4, J14.4, J15.4, OLED4.18, R25.1
SCL5: J16.4, J17.4, J18.4, OLED5.18, R30.1
SCL6: J19.4, J20.4, J21.4, OLED6.18, R35.1
SCL7: J22.4, J23.4, J24.4, OLED7.18, R40.1
SCL8: J25.4, J26.4, J27.4, OLED8.18, R45.1
SDA: J1.3, J2.3, J3.3, OLED.19, OLED.20, R13.1
SDA1: J4.3, J5.3, J6.3, OLED1.19, OLED1.20, R7.1
SDA2: J7.3, J8.3, J9.3, OLED2.19, OLED2.20, R12.1
SDA3: J10.3, J11.3, J12.3, OLED3.19, OLED3.20, R19.1
SDA4: J13.3, J14.3, J15.3, OLED4.19, OLED4.20, R24.1
SDA5: J16.3, J17.3, J18.3, OLED5.19, OLED5.20, R29.1
SDA6: J19.3, J20.3, J21.3, OLED6.19, OLED6.20, R34.1
SDA7: J22.3, J23.3, J24.3, OLED7.19, OLED7.20, R39.1
SDA8: J25.3, J26.3, J27.3, OLED8.19, OLED8.20, R44.1
VCC: C1.1, OLED.28
VCC1: C8.1, OLED1.28
VCC2: C15.1, OLED2.28
VCC3: C22.1, OLED3.28
VCC4: C29.1, OLED4.28
VCC5: C36.1, OLED5.28
VCC6: C43.1, OLED6.28
VCC7: C50.1, OLED7.28
VCC8: C57.1, OLED8.28
VCOMH: C5.1, OLED.27
VCOMH1: C12.1, OLED1.27
VCOMH2: C19.1, OLED2.27
VCOMH3: C26.1, OLED3.27
VCOMH4: C33.1, OLED4.27
VCOMH5: C40.1, OLED5.27
VCOMH6: C47.1, OLED6.27
VCOMH7: C54.1, OLED7.27
VCOMH8: C61.1, OLED8.27
VDD: C4.1, C6.1, I2C.2, J1.2, J2.2, J3.2, OLED.6, OLED.9, OLED.11, R2.1, R3.2
VDD1: C11.1, C13.1, I2C1.2, J4.2, J5.2, J6.2, OLED1.6, OLED1.9, OLED1.11, R5.2, R6.1
VDD2: C18.1, C20.1, I2C2.2, J7.2, J8.2, J9.2, OLED2.6, OLED2.9, OLED2.11, R10.2, R11.1
VDD3: C25.1, C27.1, I2C3.2, J10.2, J11.2, J12.2, OLED3.6, OLED3.9, OLED3.11, R17.2, R18.1
VDD4: C32.1, C34.1, I2C4.2, J13.2, J14.2, J15.2, OLED4.6, OLED4.9, OLED4.11, R22.2, R23.1
VDD5: C39.1, C41.1, I2C5.2, J16.2, J17.2, J18.2, OLED5.6, OLED5.9, OLED5.11, R27.2, R28.1
VDD6: C46.1, C48.1, I2C6.2, J19.2, J20.2, J21.2, OLED6.6, OLED6.9, OLED6.11, R32.2, R33.1
VDD7: C53.1, C55.1, I2C7.2, J22.2, J23.2, J24.2, OLED7.6, OLED7.9, OLED7.11, R37.2, R38.1
VDD8: C60.1, C62.1, I2C8.2, J25.2, J26.2, J27.2, OLED8.6, OLED8.9, OLED8.11, R42.2, R43.1
