scottypres/Arduino-Paragliding-Varios/Adafruit Feather Mini Vario/KiCAD Files/Component References/SparkFun_Thing_Plus_ESP32_WROOM_C/Hardware/Production/SparkFun_Thing_Plus_ESP32_WROOM_C-Panel.brd

## EAGLE design Adafruit Feather Mini Vario/KiCAD Files/Component References/SparkFun_Thing_Plus_ESP32_WROOM_C/Hardware/Production/SparkFun_Thing_Plus_ESP32_WROOM_C-Panel.brd (2026-06-28)

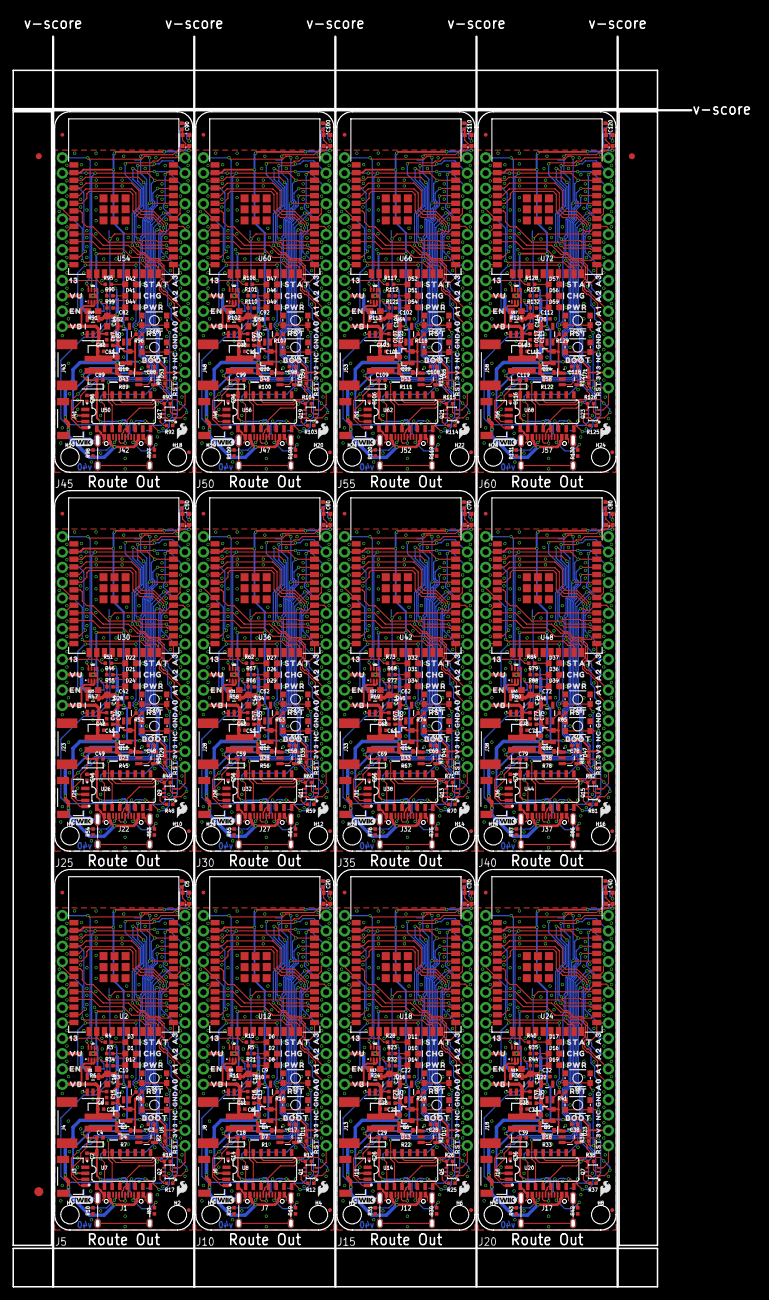
[picture p88: board SparkFun_Thing_Plus_ESP32_WROOM_C-Panel.brd from above]

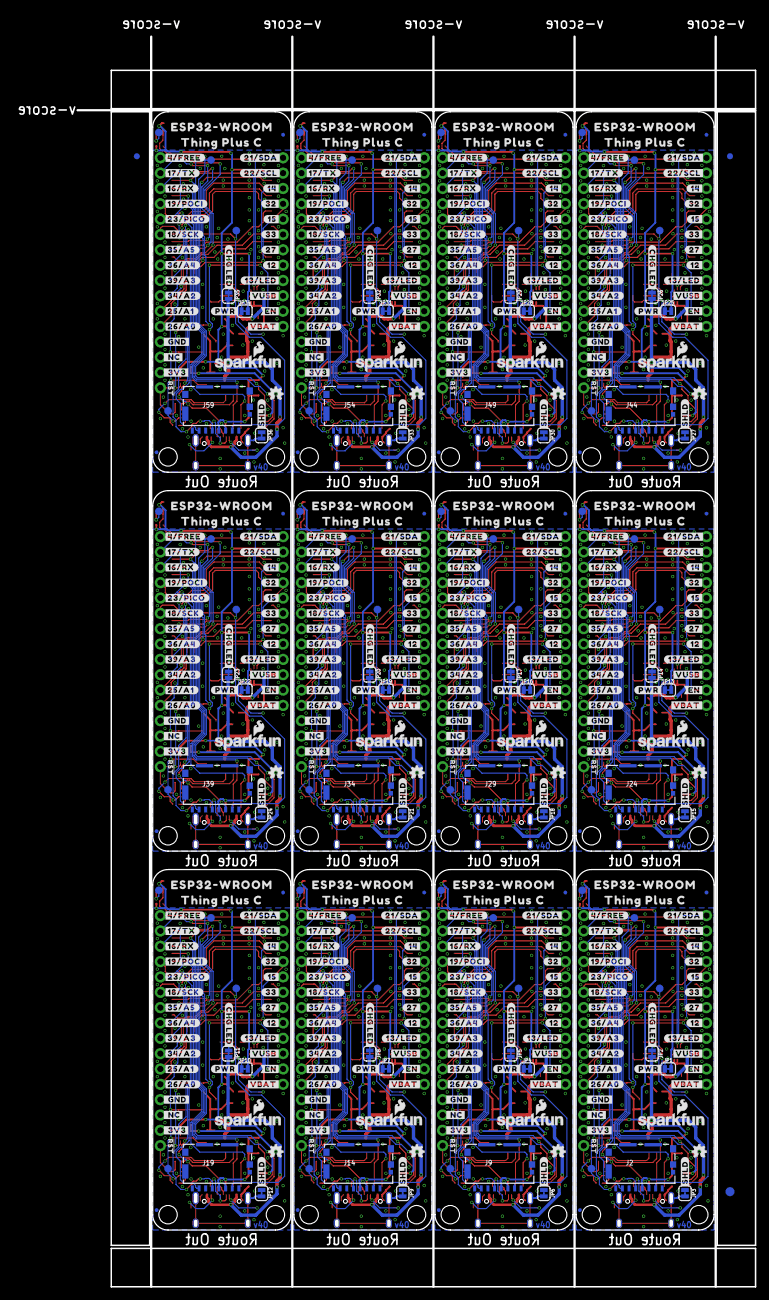
[picture p89: board SparkFun_Thing_Plus_ESP32_WROOM_C-Panel.brd from below]

Board: 2 copper layers, 112.3 x 207.0 mm, 1314 parts (555 on the bottom side), 612 nets.

Parts:
C1, C5, C13, C20, C25, C30, C35, C40, C45, C50, C55, C60, C65, C70, C75, C80, C85, C90, C95, C100, C105, C110, C115, C120: 10uF; 0402-TIGHT
C2, C4, C14, C15, C16, C18, C26, C27, C29, C36, C37, C39, C46, C47, C49, C56, C57, C59, C66, C67, C69, C76, C77, C79, C86, C87, C89, C96, C97, C99, C106, C107, C109, C116, C117, C119: 0.1uF; 0402-TIGHT
C3, C7, C8, C9, C10, C17, C21, C22, C28, C31, C32, C38, C41, C42, C48, C51, C52, C58, C61, C62, C68, C71, C72, C78, C81, C82, C88, C91, C92, C98, C101, C102, C108, C111, C112, C118: 1.0uF; 0402-TIGHT
C6, C11, C23, C33, C43, C53, C63, C73, C83, C93, C103, C113: 4.7uF; 0402-TIGHT
C12, C19, C24, C34, C44, C54, C64, C74, C84, C94, C104, C114: 4.7uF; 0603
D1, D2, D10, D16, D21, D26, D31, D36, D41, D46, D51, D56: Yellow; LED-0603
D3, D6, D11, D17, D22, D27, D32, D37, D42, D47, D52, D57: BLUE; LED-0603
D4, D7, D13, D18, D23, D28, D33, D38, D43, D48, D53, D58: 3A/10V/280mV; SOD-323
D5, D9, D15, D20, D25, D30, D35, D40, D45, D50, D55, D60: WS2812; WS2812-2020
D8, D12, D14, D19, D24, D29, D34, D39, D44, D49, D54, D59: RED; LED-0603
E$1, E$2, E$3, E$4: FIDUCIAL-1X2
E$5, E$6: FIDUCIAL-1.5X3
FD1, FD2, FD3, FD4, FD5, FD6, FD7, FD8, FD9, FD10, FD11, FD12, FD13, FD14, FD15, FD16, FD17, FD18, FD19, FD20, FD21, FD22, FD23, FD24, FD25, FD26, FD27, FD28, FD29, FD30, FD31, FD32, FD33, FD34, FD35, FD36, FD37, FD38, FD39, FD40, FD41, FD42, FD43, FD44, FD45, FD46, FD47, FD48: FIDUCIALUFIDUCIAL; FIDUCIAL-MICRO
H1, H2, H3, H4, H5, H6, H7, H8, H9, H10, H11, H12, H13, H14, H15, H16, H17, H18, H19, H20, H21, H22, H23, H24: STAND-OFFTIGHT; STAND-OFF-TIGHT
J1, J7, J12, J17, J22, J27, J32, J37, J42, J47, J52, J57: USB-C-16P-2LAYER-PADS
J2, J9, J14, J19, J24, J29, J34, J39, J44, J49, J54, J59: MICRO-SDFRICTION; MICROSD_TINY
J3, J6, J11, J16, J21, J26, J31, J36, J41, J46, J51, J56: QWIIC_RA; JST04_1MM_RA
J4, J8, J13, J18, J23, J28, J33, J38, J43, J48, J53, J58: JST-2-SMD
J5, J10, J15, J20, J25, J30, J35, J40, J45, J50, J55, J60: THING_PLUS_LOGICAL; THING_PLUS
JP1, JP2, JP3, JP4, JP5, JP6, JP7, JP8, JP9, JP10, JP11, JP12, JP13, JP14, JP15, JP16, JP17, JP18, JP19, JP20, JP21, JP22, JP23, JP24, JP25, JP26, JP27, JP28, JP29, JP30, JP31, JP32, JP33, JP34, JP35, JP36: JUMPER-SMT_2_NC_TRACE_SILK; SMT-JUMPER_2_NC_TRACE_SILK
LOGO1, LOGO6, LOGO9, LOGO12, LOGO15, LOGO18, LOGO21, LOGO24, LOGO27, LOGO30, LOGO33, LOGO36: SFE_LOGO_NAME_FLAME.1_INCH; SFE_LOGO_NAME_FLAME_.1
LOGO2, LOGO3, LOGO7, LOGO10, LOGO13, LOGO16, LOGO19, LOGO22, LOGO25, LOGO28, LOGO31, LOGO34: OSHW-LOGOMINI; OSHW-LOGO-MINI
LOGO4, LOGO5, LOGO8, LOGO11, LOGO14, LOGO17, LOGO20, LOGO23, LOGO26, LOGO29, LOGO32, LOGO35: QWIIC_LOGO_4MM; QWIIC_4MM
Q1, Q2, Q5, Q7, Q9, Q11, Q13, Q15, Q17, Q19, Q21, Q23: MBT3904DW1T1; SC70-6
Q3, Q4, Q6, Q8, Q10, Q12, Q14, Q16, Q18, Q20, Q22, Q24: 20V/4.2A/52mΩ/1.4W; SOT23-3
R1, R2, R7, R8, R12, R13, R14, R16, R17, R18, R22, R25, R26, R27, R29, R33, R37, R38, R39, R41, R45, R48, R49, R50, R52, R56, R59, R60, R61, R63, R67, R70, R71, R72, R74, R78, R81, R82, R83, R85, R89, R92, R93, R94, R96, R100, R103, R104, R105, R107, R111, R114, R115, R116, R118, R122, R125, R126, R127, R129: 10k; 0402-TIGHT
R3, R4, R5, R15, R21, R23, R28, R32, R34, R35, R40, R44, R46, R51, R55, R57, R62, R66, R68, R73, R77, R79, R84, R88, R90, R95, R99, R101, R106, R110, R112, R117, R121, R123, R128, R132: 1k; 0402-TIGHT
R6, R11, R24, R36, R47, R58, R69, R80, R91, R102, R113, R124: 2.0k; 0603
R9, R10, R19, R20, R30, R31, R42, R43, R53, R54, R64, R65, R75, R76, R86, R87, R97, R98, R108, R109, R119, R120, R130, R131: 5.1k; 0402-TIGHT
S1, S3, S5, S7, S9, S11, S13, S15, S17, S19, S21, S23: Boot; TACTILE_SWITCH_SMD_4.6X2.8MM
S2, S4, S6, S8, S10, S12, S14, S16, S18, S20, S22, S24: Reset; TACTILE_SWITCH_SMD_4.6X2.8MM
TP1, TP2, TP3, TP4, TP5, TP6, TP7, TP8, TP9, TP10, TP11, TP12, TP13, TP14, TP15, TP16, TP17, TP18, TP19, TP20, TP21, TP22, TP23, TP24, TP25, TP26, TP27, TP28, TP29, TP30, TP31, TP32, TP33, TP34, TP35, TP36, TP37, TP38, TP39, TP40, TP41, TP42, TP43, TP44, TP45, TP46, TP47, TP48: TEST-POINT3X5; PAD.03X.05
U1, U6, U13, U19, U25, U31, U37, U43, U49, U55, U61, U67: MCP73831; SOT23-5
U2, U12, U18, U24, U30, U36, U42, U48, U54, U60, U66, U72: ESP-WROOM-3232D-NARROW; ESP-WROOM-32D-NARROW
U3, U5, U10, U11, U16, U17, U22, U23, U28, U29, U34, U35, U40, U41, U46, U47, U52, U53, U58, U59, U64, U65, U70, U71: XC6222B331MR-G; SOT23-5
U4, U9, U15, U21, U27, U33, U39, U45, U51, U57, U63, U69: MAX17048; DFN-8
U7, U8, U14, U20, U26, U32, U38, U44, U50, U56, U62, U68: CH340C; SO016
U$1, U$57, U$145, U$197, U$249, U$301, U$353, U$405, U$457, U$509, U$561, U$613: SFE_LOGO_FLAME_STOP_.1
U$2, U$58, U$146, U$198, U$250, U$302, U$354, U$406, U$458, U$510, U$562, U$614: #23#PICO#0
U$3, U$59, U$147, U$199, U$251, U$303, U$355, U$407, U$459, U$511, U$563, U$615: #19#POCI#0
U$4, U$60, U$148, U$200, U$252, U$304, U$356, U$408, U$460, U$512, U$564, U$616: #4#FREE#0
U$5, U$61, U$149, U$201, U$253, U$305, U$357, U$409, U$461, U$513, U$565, U$617: #CHG_LED#0
U$6, U$62, U$150, U$202, U$254, U$306, U$358, U$410, U$462, U$514, U$566, U$618: ESP32#WROOM0
U$7, U$63, U$151, U$203, U$255, U$307, U$359, U$411, U$463, U$515, U$567, U$619: THING_PLUS_C0
U$8, U$82, U$156, U$208, U$260, U$312, U$364, U$416, U$468, U$520, U$572, U$624: #SHLD#0
U$9, U$64, U$152, U$204, U$256, U$308, U$360, U$412, U$464, U$516, U$568, U$620: #_GND#0
U$10, U$65, U$153, U$205, U$257, U$309, U$361, U$413, U$465, U$517, U$569, U$621: #_NC#0
U$11, U$66, U$154, U$206, U$258, U$310, U$362, U$414, U$466, U$518, U$570, U$622: #_3V3#0
U$12, U$67, U$155, U$207, U$259, U$311, U$363, U$415, U$467, U$519, U$571, U$623: SFE_LOGO_FLAME_.1
U$13, U$24, U$103, U$157, U$209, U$261, U$313, U$365, U$417, U$469, U$521, U$573: CHG1
U$14, U$25, U$104, U$158, U$210, U$262, U$314, U$366, U$418, U$470, U$522, U$574: PWR2
U$15, U$26, U$105, U$159, U$211, U$263, U$315, U$367, U$419, U$471, U$523, U$575: STAT0
U$16, U$68, U$106, U$160, U$212, U$264, U$316, U$368, U$420, U$472, U$524, U$576: A03
U$17, U$69, U$108, U$161, U$213, U$265, U$317, U$369, U$421, U$473, U$525, U$577: A12
U$18, U$70, U$110, U$162, U$214, U$266, U$318, U$370, U$422, U$474, U$526, U$578: A21
U$19, U$71, U$111, U$163, U$215, U$267, U$319, U$371, U$423, U$475, U$527, U$579: A30
U$20, U$74, U$112, U$164, U$216, U$268, U$320, U$372, U$424, U$476, U$528, U$580: EN3
U$21, U$77, U$113, U$165, U$217, U$269, U$321, U$373, U$425, U$477, U$529, U$581: 130
U$22, U$78, U$114, U$166, U$218, U$270, U$322, U$374, U$426, U$478, U$530, U$582: BOOT0
U$23, U$31, U$119, U$171, U$223, U$275, U$327, U$379, U$431, U$483, U$535, U$587: 3V30
U$27, U$54, U$79, U$109, U$115, U$142, U$167, U$194, U$219, U$246, U$271, U$298, U$323, U$350, U$375, U$402, U$427, U$454, U$479, U$506, U$531, U$558, U$583, U$610: #RST#0
U$28, U$80, U$116, U$168, U$220, U$272, U$324, U$376, U$428, U$480, U$532, U$584: RST0
U$29, U$73, U$117, U$169, U$221, U$273, U$325, U$377, U$429, U$481, U$533, U$585: VB1
U$30, U$76, U$118, U$170, U$222, U$274, U$326, U$378, U$430, U$482, U$534, U$586: VU0
U$32, U$72, U$120, U$172, U$224, U$276, U$328, U$380, U$432, U$484, U$536, U$588: #17#TX#0
U$33, U$81, U$121, U$173, U$225, U$277, U$329, U$381, U$433, U$485, U$537, U$589: #16#RX#0
U$34, U$83, U$122, U$174, U$226, U$278, U$330, U$382, U$434, U$486, U$538, U$590: #18#SCK#0
U$35, U$84, U$123, U$175, U$227, U$279, U$331, U$383, U$435, U$487, U$539, U$591: #35#A5#0
U$36, U$85, U$124, U$176, U$228, U$280, U$332, U$384, U$436, U$488, U$540, U$592: #36#A4#0
U$37, U$86, U$125, U$177, U$229, U$281, U$333, U$385, U$437, U$489, U$541, U$593: #25#A1#2
U$38, U$87, U$126, U$178, U$230, U$282, U$334, U$386, U$438, U$490, U$542, U$594: #26#A0#3
U$39, U$88, U$127, U$179, U$231, U$283, U$335, U$387, U$439, U$491, U$543, U$595: #34#A2#1
U$40, U$89, U$128, U$180, U$232, U$284, U$336, U$388, U$440, U$492, U$544, U$596: #39#A3#0
U$41, U$90, U$129, U$181, U$233, U$285, U$337, U$389, U$441, U$493, U$545, U$597: #12#4
U$42, U$91, U$130, U$182, U$234, U$286, U$338, U$390, U$442, U$494, U$546, U$598: #14#9
U$43, U$92, U$131, U$183, U$235, U$287, U$339, U$391, U$443, U$495, U$547, U$599: #15#7
U$44, U$93, U$132, U$184, U$236, U$288, U$340, U$392, U$444, U$496, U$548, U$600: #27#5
U$45, U$94, U$133, U$185, U$237, U$289, U$341, U$393, U$445, U$497, U$549, U$601: #32#8
U$46, U$95, U$134, U$186, U$238, U$290, U$342, U$394, U$446, U$498, U$550, U$602: #33#6
U$47, U$96, U$135, U$187, U$239, U$291, U$343, U$395, U$447, U$499, U$551, U$603: #EN#1
U$48, U$97, U$136, U$188, U$240, U$292, U$344, U$396, U$448, U$500, U$552, U$604: #VBAT#0
U$49, U$98, U$137, U$189, U$241, U$293, U$345, U$397, U$449, U$501, U$553, U$605: #VUSB#2
U$50, U$99, U$138, U$190, U$242, U$294, U$346, U$398, U$450, U$502, U$554, U$606: #13#LED#0
U$51, U$100, U$139, U$191, U$243, U$295, U$347, U$399, U$451, U$503, U$555, U$607: #21#SDA#1
U$52, U$101, U$140, U$192, U$244, U$296, U$348, U$400, U$452, U$504, U$556, U$608: #22#SCL#0
U$53, U$102, U$141, U$193, U$245, U$297, U$349, U$401, U$453, U$505, U$557, U$609: #PWR#0
U$55, U$75, U$143, U$195, U$247, U$299, U$351, U$403, U$455, U$507, U$559, U$611: GND1
U$56, U$107, U$144, U$196, U$248, U$300, U$352, U$404, U$456, U$508, U$560, U$612: NC0

Connections:
3.3V: C1.1, C2.1, C4.1, C5.1, C10.1, D5.VCC, J2.4, J5.27, JP1.2, R2.2, U2.2, U3.5, U7.4, U7.16
3.3V1: C9.1, C13.1, C14.1, C18.1, C20.1, D9.VCC, J9.4, J10.27, JP4.2, R14.2, U8.4, U8.16, U10.5, U12.2
3.3V2: C22.1, C25.1, C26.1, C29.1, C30.1, D15.VCC, J14.4, J15.27, JP7.2, R27.2, U14.4, U14.16, U16.5, U18.2
3.3V3: C32.1, C35.1, C36.1, C39.1, C40.1, D20.VCC, J19.4, J20.27, JP10.2, R39.2, U20.4, U20.16, U22.5, U24.2
3.3V4: C42.1, C45.1, C46.1, C49.1, C50.1, D25.VCC, J24.4, J25.27, JP13.2, R50.2, U26.4, U26.16, U28.5, U30.2
3.3V5: C52.1, C55.1, C56.1, C59.1, C60.1, D30.VCC, J29.4, J30.27, JP16.2, R61.2, U32.4, U32.16, U34.5, U36.2
3.3V6: C62.1, C65.1, C66.1, C69.1, C70.1, D35.VCC, J34.4, J35.27, JP19.2, R72.2, U38.4, U38.16, U40.5, U42.2
3.3V7: C72.1, C75.1, C76.1, C79.1, C80.1, D40.VCC, J39.4, J40.27, JP22.2, R83.2, U44.4, U44.16, U46.5, U48.2
3.3V8: C82.1, C85.1, C86.1, C89.1, C90.1, D45.VCC, J44.4, J45.27, JP25.2, R94.2, U50.4, U50.16, U52.5, U54.2
3.3V9: C92.1, C95.1, C96.1, C99.1, C100.1, D50.VCC, J49.4, J50.27, JP28.2, R105.2, U56.4, U56.16, U58.5, U60.2
3.3V10: C102.1, C105.1, C106.1, C109.1, C110.1, D55.VCC, J54.4, J55.27, JP31.2, R116.2, U62.4, U62.16, U64.5, U66.2
3.3V11: C112.1, C115.1, C116.1, C119.1, C120.1, D60.VCC, J59.4, J60.27, JP34.2, R127.2, U68.4, U68.16, U70.5, U72.2
!RESET!: J5.28, Q2.3, R2.1, S4.3, S4.4, U2.3
!RESET!1: J10.28, Q1.3, R14.1, S2.3, S2.4, U12.3
!RESET!2: J15.28, Q5.3, R27.1, S6.3, S6.4, U18.3
!RESET!3: J20.28, Q7.3, R39.1, S8.3, S8.4, U24.3
!RESET!4: J25.28, Q9.3, R50.1, S10.3, S10.4, U30.3
!RESET!5: J30.28, Q11.3, R61.1, S12.3, S12.4, U36.3
!RESET!6: J35.28, Q13.3, R72.1, S14.3, S14.4, U42.3
!RESET!7: J40.28, Q15.3, R83.1, S16.3, S16.4, U48.3
!RESET!8: J45.28, Q17.3, R94.1, S18.3, S18.4, U54.3
!RESET!9: J50.28, Q19.3, R105.1, S20.3, S20.4, U60.3
!RESET!10: J55.28, Q21.3, R116.1, S22.3, S22.4, U66.3
!RESET!11: J60.28, Q23.3, R127.1, S24.3, S24.4, U72.3
CH340-DTR: Q2.1, R17.1, U7.13
CH340-DTR1: Q1.1, R12.1, U8.13
CH340-DTR2: Q5.1, R25.1, U14.13
CH340-DTR3: Q7.1, R37.1, U20.13
CH340-DTR4: Q9.1, R48.1, U26.13
CH340-DTR5: Q11.1, R59.1, U32.13
CH340-DTR6: Q13.1, R70.1, U38.13
CH340-DTR7: Q15.1, R81.1, U44.13
CH340-DTR8: Q17.1, R92.1, U50.13
CH340-DTR9: Q19.1, R103.1, U56.13
CH340-DTR10: Q21.1, R114.1, U62.13
CH340-DTR11: Q23.1, R125.1, U68.13
CH340-RTS: Q2.4, R18.1, U7.14
CH340-RTS1: Q1.4, R13.1, U8.14
CH340-RTS2: Q5.4, R26.1, U14.14
CH340-RTS3: Q7.4, R38.1, U20.14
CH340-RTS4: Q9.4, R49.1, U26.14
CH340-RTS5: Q11.4, R60.1, U32.14
CH340-RTS6: Q13.4, R71.1, U38.14
CH340-RTS7: Q15.4, R82.1, U44.14
CH340-RTS8: Q17.4, R93.1, U50.14
CH340-RTS9: Q19.4, R104.1, U56.14
CH340-RTS10: Q21.4, R115.1, U62.14
CH340-RTS11: Q23.4, R126.1, U68.14
CH340-RX: U2.35, U7.3
CH340-RX1: U8.3, U12.35
CH340-RX2: U14.3, U18.35
CH340-RX3: U20.3, U24.35
CH340-RX4: U26.3, U30.35
CH340-RX5: U32.3, U36.35
CH340-RX6: U38.3, U42.35
CH340-RX7: U44.3, U48.35
CH340-RX8: U50.3, U54.35
CH340-RX9: U56.3, U60.35
CH340-RX10: U62.3, U66.35
CH340-RX11: U68.3, U72.35
CH340-TX: U2.34, U7.2
CH340-TX1: U8.2, U12.34
CH340-TX2: U14.2, U18.34
CH340-TX3: U20.2, U24.34
CH340-TX4: U26.2, U30.34
CH340-TX5: U32.2, U36.34
CH340-TX6: U38.2, U42.34
CH340-TX7: U44.2, U48.34
CH340-TX8: U50.2, U54.34
CH340-TX9: U56.2, U60.34
CH340-TX10: U62.2, U66.34
CH340-TX11: U68.2, U72.34
CHG_LED: D1.A, R3.2
CHG_LED1: D2.A, R5.2
CHG_LED2: D10.A, R23.2
CHG_LED3: D16.A, R35.2
CHG_LED4: D21.A, R46.2
CHG_LED5: D26.A, R57.2
CHG_LED6: D31.A, R68.2
CHG_LED7: D36.A, R79.2
CHG_LED8: D41.A, R90.2
CHG_LED9: D46.A, R101.2
CHG_LED10: D51.A, R112.2
CHG_LED11: D56.A, R123.2
D+: J1.A6, J1.B6, U7.5
D+1: J7.A6, J7.B6, U8.5
D+2: J12.A6, J12.B6, U14.5
D+3: J17.A6, J17.B6, U20.5
D+4: J22.A6, J22.B6, U26.5
D+5: J27.A6, J27.B6, U32.5
D+6: J32.A6, J32.B6, U38.5
D+7: J37.A6, J37.B6, U44.5
D+8: J42.A6, J42.B6, U50.5
D+9: J47.A6, J47.B6, U56.5
D+10: J52.A6, J52.B6, U62.5
D+11: J57.A6, J57.B6, U68.5
D-: J1.A7, J1.B7, U7.6
D-1: J7.A7, J7.B7, U8.6
D-2: J12.A7, J12.B7, U14.6
D-3: J17.A7, J17.B7, U20.6
D-4: J22.A7, J22.B7, U26.6
D-5: J27.A7, J27.B7, U32.6
D-6: J32.A7, J32.B7, U38.6
D-7: J37.A7, J37.B7, U44.6
D-8: J42.A7, J42.B7, U50.6
D-9: J47.A7, J47.B7, U56.6
D-10: J52.A7, J52.B7, U62.6
D-11: J57.A7, J57.B7, U68.6
DTR-10K: Q2.5, R17.2
DTR-10K1: Q1.5, R12.2
DTR-10K2: Q5.5, R25.2
DTR-10K3: Q7.5, R37.2
DTR-10K4: Q9.5, R48.2
DTR-10K5: Q11.5, R59.2
DTR-10K6: Q13.5, R70.2
DTR-10K7: Q15.5, R81.2
DTR-10K8: Q17.5, R92.2
DTR-10K9: Q19.5, R103.2
DTR-10K10: Q21.5, R114.2
DTR-10K11: Q23.5, R125.2
ESP_0/QPWR: Q2.6, S3.3, S3.4, TP1.1, U2.25, U5.3
ESP_0/QPWR1: Q1.6, S1.3, S1.4, TP5.1, U11.3, U12.25
ESP_0/QPWR2: Q5.6, S5.3, S5.4, TP9.1, U17.3, U18.25
ESP_0/QPWR3: Q7.6, S7.3, S7.4, TP13.1, U23.3, U24.25
ESP_0/QPWR4: Q9.6, S9.3, S9.4, TP17.1, U29.3, U30.25
ESP_0/QPWR5: Q11.6, S11.3, S11.4, TP21.1, U35.3, U36.25
ESP_0/QPWR6: Q13.6, S13.3, S13.4, TP25.1, U41.3, U42.25
ESP_0/QPWR7: Q15.6, S15.3, S15.4, TP29.1, U47.3, U48.25
ESP_0/QPWR8: Q17.6, S17.3, S17.4, TP33.1, U53.3, U54.25
ESP_0/QPWR9: Q19.6, S19.3, S19.4, TP37.1, U59.3, U60.25
ESP_0/QPWR10: Q21.6, S21.3, S21.4, TP41.1, U65.3, U66.25
ESP_0/QPWR11: Q23.6, S23.3, S23.4, TP45.1, U71.3, U72.25
ESP_2/RGB_DI: D5.DI, TP3.1, U2.24
ESP_2/RGB_DI1: D9.DI, TP7.1, U12.24
ESP_2/RGB_DI2: D15.DI, TP11.1, U18.24
ESP_2/RGB_DI3: D20.DI, TP15.1, U24.24
ESP_2/RGB_DI4: D25.DI, TP19.1, U30.24
ESP_2/RGB_DI5: D30.DI, TP23.1, U36.24
ESP_2/RGB_DI6: D35.DI, TP27.1, U42.24
ESP_2/RGB_DI7: D40.DI, TP31.1, U48.24
ESP_2/RGB_DI8: D45.DI, TP35.1, U54.24
ESP_2/RGB_DI9: D50.DI, TP39.1, U60.24
ESP_2/RGB_DI10: D55.DI, TP43.1, U66.24
ESP_2/RGB_DI11: D60.DI, TP47.1, U72.24
ESP_4/TP_FB: J5.13, U2.26
ESP_4/TP_FB1: J10.13, U12.26
ESP_4/TP_FB2: J15.13, U18.26
ESP_4/TP_FB3: J20.13, U24.26
ESP_4/TP_FB4: J25.13, U30.26
ESP_4/TP_FB5: J30.13, U36.26
ESP_4/TP_FB6: J35.13, U42.26
ESP_4/TP_FB7: J40.13, U48.26
ESP_4/TP_FB8: J45.13, U54.26
ESP_4/TP_FB9: J50.13, U60.26
ESP_4/TP_FB10: J55.13, U66.26
ESP_4/TP_FB11: J60.13, U72.26
ESP_5/SD_CS: J2.2, TP4.1, U2.29
ESP_5/SD_CS1: J9.2, TP8.1, U12.29
ESP_5/SD_CS2: J14.2, TP12.1, U18.29
ESP_5/SD_CS3: J19.2, TP16.1, U24.29
ESP_5/SD_CS4: J24.2, TP20.1, U30.29
ESP_5/SD_CS5: J29.2, TP24.1, U36.29
ESP_5/SD_CS6: J34.2, TP28.1, U42.29
ESP_5/SD_CS7: J39.2, TP32.1, U48.29
ESP_5/SD_CS8: J44.2, TP36.1, U54.29
ESP_5/SD_CS9: J49.2, TP40.1, U60.29
ESP_5/SD_CS10: J54.2, TP44.1, U66.29
ESP_5/SD_CS11: J59.2, TP48.1, U72.29
ESP_12/GPIO1: J5.8, U2.14
ESP_12/GPIO2: J10.8, U12.14
ESP_12/GPIO3: J15.8, U18.14
ESP_12/GPIO4: J20.8, U24.14
ESP_12/GPIO5: J25.8, U30.14
ESP_12/GPIO6: J30.8, U36.14
ESP_12/GPIO7: J35.8, U42.14
ESP_12/GPIO8: J40.8, U48.14
ESP_12/GPIO9: J45.8, U54.14
ESP_12/GPIO10: J50.8, U60.14
ESP_12/GPIO11: J55.8, U66.14
ESP_12/GPIO12: J60.8, U72.14
ESP_13/GPIO0/LED: J5.9, R4.1, U2.16
ESP_13/GPIO0/LED1: J10.9, R15.1, U12.16
ESP_13/GPIO0/LED2: J15.9, R28.1, U18.16
ESP_13/GPIO0/LED3: J20.9, R40.1, U24.16
ESP_13/GPIO0/LED4: J25.9, R51.1, U30.16
ESP_13/GPIO0/LED5: J30.9, R62.1, U36.16
ESP_13/GPIO0/LED6: J35.9, R73.1, U42.16
ESP_13/GPIO0/LED7: J40.9, R84.1, U48.16
ESP_13/GPIO0/LED8: J45.9, R95.1, U54.16
ESP_13/GPIO0/LED9: J50.9, R106.1, U60.16
ESP_13/GPIO0/LED10: J55.9, R117.1, U66.16
ESP_13/GPIO0/LED11: J60.9, R128.1, U72.16
ESP_14/GPIO1: J10.3, U12.13
ESP_14/GPIO2: J15.3, U18.13
ESP_14/GPIO3: J20.3, U24.13
ESP_14/GPIO4: J25.3, U30.13
ESP_14/GPIO5: J30.3, U36.13
ESP_14/GPIO6: J5.3, U2.13
ESP_14/GPIO7: J35.3, U42.13
ESP_14/GPIO8: J40.3, U48.13
ESP_14/GPIO9: J45.3, U54.13
ESP_14/GPIO10: J50.3, U60.13
ESP_14/GPIO11: J55.3, U66.13
ESP_14/GPIO12: J60.3, U72.13
ESP_15/GPIO1: J10.5, U12.23
ESP_15/GPIO2: J15.5, U18.23
ESP_15/GPIO3: J20.5, U24.23
ESP_15/GPIO4: J5.5, U2.23
ESP_15/GPIO5: J25.5, U30.23
ESP_15/GPIO6: J30.5, U36.23
ESP_15/GPIO7: J35.5, U42.23
ESP_15/GPIO8: J40.5, U48.23
ESP_15/GPIO9: J45.5, U54.23
ESP_15/GPIO10: J50.5, U60.23
ESP_15/GPIO11: J55.5, U66.23
ESP_15/GPIO12: J60.5, U72.23
ESP_16/TP_RX: J5.15, U2.27
ESP_16/TP_RX1: J10.15, U12.27
ESP_16/TP_RX2: J15.15, U18.27
ESP_16/TP_RX3: J20.15, U24.27
ESP_16/TP_RX4: J25.15, U30.27
ESP_16/TP_RX5: J30.15, U36.27
ESP_16/TP_RX6: J35.15, U42.27
ESP_16/TP_RX7: J40.15, U48.27
ESP_16/TP_RX8: J45.15, U54.27
ESP_16/TP_RX9: J50.15, U60.27
ESP_16/TP_RX10: J55.15, U66.27
ESP_16/TP_RX11: J60.15, U72.27
ESP_17/TP_TX: J5.14, U2.28
ESP_17/TP_TX1: J10.14, U12.28
ESP_17/TP_TX2: J15.14, U18.28
ESP_17/TP_TX3: J20.14, U24.28
ESP_17/TP_TX4: J25.14, U30.28
ESP_17/TP_TX5: J30.14, U36.28
ESP_17/TP_TX6: J35.14, U42.28
ESP_17/TP_TX7: J40.14, U48.28
ESP_17/TP_TX8: J45.14, U54.28
ESP_17/TP_TX9: J50.14, U60.28
ESP_17/TP_TX10: J55.14, U66.28
ESP_17/TP_TX11: J60.14, U72.28
ESP_18/TP_SCK: J2.5, J5.18, U2.30
ESP_18/TP_SCK1: J9.5, J10.18, U12.30
ESP_18/TP_SCK2: J14.5, J15.18, U18.30
ESP_18/TP_SCK3: J19.5, J20.18, U24.30
ESP_18/TP_SCK4: J24.5, J25.18, U30.30
ESP_18/TP_SCK5: J29.5, J30.18, U36.30
ESP_18/TP_SCK6: J34.5, J35.18, U42.30
ESP_18/TP_SCK7: J39.5, J40.18, U48.30
ESP_18/TP_SCK8: J44.5, J45.18, U54.30
ESP_18/TP_SCK9: J49.5, J50.18, U60.30
ESP_18/TP_SCK10: J54.5, J55.18, U66.30
ESP_18/TP_SCK11: J59.5, J60.18, U72.30
ESP_19/TP_POCI: J2.7, J5.16, U2.31
ESP_19/TP_POCI1: J9.7, J10.16, U12.31
ESP_19/TP_POCI2: J14.7, J15.16, U18.31
ESP_19/TP_POCI3: J19.7, J20.16, U24.31
ESP_19/TP_POCI4: J24.7, J25.16, U30.31
ESP_19/TP_POCI5: J29.7, J30.16, U36.31
ESP_19/TP_POCI6: J34.7, J35.16, U42.31
ESP_19/TP_POCI7: J39.7, J40.16, U48.31
ESP_19/TP_POCI8: J44.7, J45.16, U54.31
ESP_19/TP_POCI9: J49.7, J50.16, U60.31
ESP_19/TP_POCI10: J54.7, J55.16, U66.31
ESP_19/TP_POCI11: J59.7, J60.16, U72.31
ESP_21/TP_SDA: J3.3, J5.1, U2.33, U4.8
ESP_21/TP_SDA1: J6.3, J10.1, U9.8, U12.33
ESP_21/TP_SDA2: J11.3, J15.1, U15.8, U18.33
ESP_21/TP_SDA3: J16.3, J20.1, U21.8, U24.33
ESP_21/TP_SDA4: J21.3, J25.1, U27.8, U30.33
ESP_21/TP_SDA5: J26.3, J30.1, U33.8, U36.33
ESP_21/TP_SDA6: J31.3, J35.1, U39.8, U42.33
ESP_21/TP_SDA7: J36.3, J40.1, U45.8, U48.33
ESP_21/TP_SDA8: J41.3, J45.1, U51.8, U54.33
ESP_21/TP_SDA9: J46.3, J50.1, U57.8, U60.33
ESP_21/TP_SDA10: J51.3, J55.1, U63.8, U66.33
ESP_21/TP_SDA11: J56.3, J60.1, U69.8, U72.33
ESP_22/TP_SCL: J3.4, J5.2, U2.36, U4.7
ESP_22/TP_SCL1: J6.4, J10.2, U9.7, U12.36
ESP_22/TP_SCL2: J11.4, J15.2, U15.7, U18.36
ESP_22/TP_SCL3: J16.4, J20.2, U21.7, U24.36
ESP_22/TP_SCL4: J21.4, J25.2, U27.7, U30.36
ESP_22/TP_SCL5: J26.4, J30.2, U33.7, U36.36
ESP_22/TP_SCL6: J31.4, J35.2, U39.7, U42.36
ESP_22/TP_SCL7: J36.4, J40.2, U45.7, U48.36
ESP_22/TP_SCL8: J41.4, J45.2, U51.7, U54.36
ESP_22/TP_SCL9: J46.4, J50.2, U57.7, U60.36
ESP_22/TP_SCL10: J51.4, J55.2, U63.7, U66.36
ESP_22/TP_SCL11: J56.4, J60.2, U69.7, U72.36
ESP_23/TP_PICO: J2.3, J5.17, U2.37
ESP_23/TP_PICO1: J9.3, J10.17, U12.37
ESP_23/TP_PICO2: J14.3, J15.17, U18.37
ESP_23/TP_PICO3: J19.3, J20.17, U24.37
ESP_23/TP_PICO4: J24.3, J25.17, U30.37
ESP_23/TP_PICO5: J29.3, J30.17, U36.37
ESP_23/TP_PICO6: J34.3, J35.17, U42.37
ESP_23/TP_PICO7: J39.3, J40.17, U48.37
ESP_23/TP_PICO8: J44.3, J45.17, U54.37
ESP_23/TP_PICO9: J49.3, J50.17, U60.37
ESP_23/TP_PICO10: J54.3, J55.17, U66.37
ESP_23/TP_PICO11: J59.3, J60.17, U72.37
ESP_25/TP_A1: J5.23, U2.10
ESP_25/TP_A2: J10.23, U12.10
ESP_25/TP_A3: J15.23, U18.10
ESP_25/TP_A4: J20.23, U24.10
ESP_25/TP_A5: J25.23, U30.10
ESP_25/TP_A6: J30.23, U36.10
ESP_25/TP_A7: J35.23, U42.10
ESP_25/TP_A8: J40.23, U48.10
ESP_25/TP_A9: J45.23, U54.10
ESP_25/TP_A10: J50.23, U60.10
ESP_25/TP_A11: J55.23, U66.10
ESP_25/TP_A12: J60.23, U72.10
ESP_26/TP_A0: J5.24, U2.11
ESP_26/TP_A1: J10.24, U12.11
ESP_26/TP_A2: J15.24, U18.11
ESP_26/TP_A3: J20.24, U24.11
ESP_26/TP_A4: J25.24, U30.11
ESP_26/TP_A5: J30.24, U36.11
ESP_26/TP_A6: J35.24, U42.11
ESP_26/TP_A7: J40.24, U48.11
ESP_26/TP_A8: J45.24, U54.11
ESP_26/TP_A9: J50.24, U60.11
ESP_26/TP_A10: J55.24, U66.11
ESP_26/TP_A11: J60.24, U72.11
ESP_27/GPIO1: J10.7, U12.12
ESP_27/GPIO2: J5.7, U2.12
ESP_27/GPIO3: J15.7, U18.12
ESP_27/GPIO4: J20.7, U24.12
ESP_27/GPIO5: J25.7, U30.12
ESP_27/GPIO6: J30.7, U36.12
ESP_27/GPIO7: J35.7, U42.12
ESP_27/GPIO8: J40.7, U48.12
ESP_27/GPIO9: J45.7, U54.12
ESP_27/GPIO10: J50.7, U60.12
ESP_27/GPIO11: J55.7, U66.12
ESP_27/GPIO12: J60.7, U72.12
ESP_32/GPIO1: J10.4, U12.8
ESP_32/GPIO2: J15.4, U18.8
ESP_32/GPIO3: J20.4, U24.8
ESP_32/GPIO4: J25.4, U30.8
ESP_32/GPIO5: J5.4, U2.8
ESP_32/GPIO6: J30.4, U36.8
ESP_32/GPIO7: J35.4, U42.8
ESP_32/GPIO8: J40.4, U48.8
ESP_32/GPIO9: J45.4, U54.8
ESP_32/GPIO10: J50.4, U60.8
ESP_32/GPIO11: J55.4, U66.8
ESP_32/GPIO12: J60.4, U72.8
ESP_33/GPIO1: J10.6, U12.9
ESP_33/GPIO2: J15.6, U18.9
ESP_33/GPIO3: J5.6, U2.9
ESP_33/GPIO4: J20.6, U24.9
ESP_33/GPIO5: J25.6, U30.9
ESP_33/GPIO6: J30.6, U36.9
ESP_33/GPIO7: J35.6, U42.9
ESP_33/GPIO8: J40.6, U48.9
ESP_33/GPIO9: J45.6, U54.9
ESP_33/GPIO10: J50.6, U60.9
ESP_33/GPIO11: J55.6, U66.9
ESP_33/GPIO12: J60.6, U72.9
ESP_34/TP_A1: J10.22, U12.6
ESP_34/TP_A2: J5.22, U2.6
ESP_34/TP_A3: J15.22, U18.6
ESP_34/TP_A4: J20.22, U24.6
ESP_34/TP_A5: J25.22, U30.6
ESP_34/TP_A6: J30.22, U36.6
ESP_34/TP_A7: J35.22, U42.6
ESP_34/TP_A8: J40.22, U48.6
ESP_34/TP_A9: J45.22, U54.6
ESP_34/TP_A10: J50.22, U60.6
ESP_34/TP_A11: J55.22, U66.6
ESP_34/TP_A12: J60.22, U72.6
ESP_35/TP_A1: J10.19, U12.7
ESP_35/TP_A2: J15.19, U18.7
ESP_35/TP_A3: J20.19, U24.7
ESP_35/TP_A4: J25.19, U30.7
ESP_35/TP_A5: J5.19, U2.7
ESP_35/TP_A6: J30.19, U36.7
ESP_35/TP_A7: J35.19, U42.7
ESP_35/TP_A8: J40.19, U48.7
ESP_35/TP_A9: J45.19, U54.7
ESP_35/TP_A10: J50.19, U60.7
ESP_35/TP_A11: J55.19, U66.7
ESP_35/TP_A12: J60.19, U72.7
ESP_36/TP_A1: J10.20, U12.4
ESP_36/TP_A2: J15.20, U18.4
ESP_36/TP_A3: J20.20, U24.4
ESP_36/TP_A4: J5.20, U2.4
ESP_36/TP_A5: J25.20, U30.4
ESP_36/TP_A6: J30.20, U36.4
ESP_36/TP_A7: J35.20, U42.4
ESP_36/TP_A8: J40.20, U48.4
ESP_36/TP_A9: J45.20, U54.4
ESP_36/TP_A10: J50.20, U60.4
ESP_36/TP_A11: J55.20, U66.4
ESP_36/TP_A12: J60.20, U72.4
ESP_39/TP_A1: J10.21, U12.5
ESP_39/TP_A2: J15.21, U18.5
ESP_39/TP_A3: J5.21, U2.5
ESP_39/TP_A4: J20.21, U24.5
ESP_39/TP_A5: J25.21, U30.5
ESP_39/TP_A6: J30.21, U36.5
ESP_39/TP_A7: J35.21, U42.5
ESP_39/TP_A8: J40.21, U48.5
ESP_39/TP_A9: J45.21, U54.5
ESP_39/TP_A10: J50.21, U60.5
ESP_39/TP_A11: J55.21, U66.5
ESP_39/TP_A12: J60.21, U72.5
GND: C1.2, C2.2, C3.2, C4.2, C5.2, C6.2, C7.2, C10.2, C15.2, C19.2, D3.C, D5.GND, D12.C, J1.GND, J1.GND2, J2.6, J2.GND1, J2.GND2, J2.GND3, J2.GND4, J2.GND5, J2.GND6, J3.1, J4.1, J5.25, JP3.1, R6.1, R7.1, R9.1, R10.1, S3.1, S3.2, S4.1, S4.2, U1.2, U2.1, U2.15, U2.38, U2.GND1, U2.GNDT1, U2.GNDT2, U2.GNDT3, U2.GNDT4, U2.GNDT5, U2.GNDT6, U2.GNDT7, U2.GNDT8, U3.2, U4.1, U4.4, U4.6, U4.9, U5.2, U7.1
GND1: C8.2, C9.2, C11.2, C12.2, C13.2, C14.2, C16.2, C17.2, C18.2, C20.2, D6.C, D8.C, D9.GND, J6.1, J7.GND, J7.GND2, J8.1, J9.6, J9.GND1, J9.GND2, J9.GND3, J9.GND4, J9.GND5, J9.GND6, J10.25, JP6.1, R1.1, R11.1, R19.1, R20.1, S1.1, S1.2, S2.1, S2.2, U6.2, U8.1, U9.1, U9.4, U9.6, U9.9, U10.2, U11.2, U12.1, U12.15, U12.38, U12.GND1, U12.GNDT1, U12.GNDT2, U12.GNDT3, U12.GNDT4, U12.GNDT5, U12.GNDT6, U12.GNDT7, U12.GNDT8
GND2: C21.2, C22.2, C23.2, C24.2, C25.2, C26.2, C27.2, C28.2, C29.2, C30.2, D11.C, D14.C, D15.GND, J11.1, J12.GND, J12.GND2, J13.1, J14.6, J14.GND1, J14.GND2, J14.GND3, J14.GND4, J14.GND5, J14.GND6, J15.25, JP9.1, R22.1, R24.1, R30.1, R31.1, S5.1, S5.2, S6.1, S6.2, U13.2, U14.1, U15.1, U15.4, U15.6, U15.9, U16.2, U17.2, U18.1, U18.15, U18.38, U18.GND1, U18.GNDT1, U18.GNDT2, U18.GNDT3, U18.GNDT4, U18.GNDT5, U18.GNDT6, U18.GNDT7, U18.GNDT8
GND3: C31.2, C32.2, C33.2, C34.2, C35.2, C36.2, C37.2, C38.2, C39.2, C40.2, D17.C, D19.C, D20.GND, J16.1, J17.GND, J17.GND2, J18.1, J19.6, J19.GND1, J19.GND2, J19.GND3, J19.GND4, J19.GND5, J19.GND6, J20.25, JP12.1, R33.1, R36.1, R42.1, R43.1, S7.1, S7.2, S8.1, S8.2, U19.2, U20.1, U21.1, U21.4, U21.6, U21.9, U22.2, U23.2, U24.1, U24.15, U24.38, U24.GND1, U24.GNDT1, U24.GNDT2, U24.GNDT3, U24.GNDT4, U24.GNDT5, U24.GNDT6, U24.GNDT7, U24.GNDT8
GND4: C41.2, C42.2, C43.2, C44.2, C45.2, C46.2, C47.2, C48.2, C49.2, C50.2, D22.C, D24.C, D25.GND, J21.1, J22.GND, J22.GND2, J23.1, J24.6, J24.GND1, J24.GND2, J24.GND3, J24.GND4, J24.GND5, J24.GND6, J25.25, JP15.1, R45.1, R47.1, R53.1, R54.1, S9.1, S9.2, S10.1, S10.2, U25.2, U26.1, U27.1, U27.4, U27.6, U27.9, U28.2, U29.2, U30.1, U30.15, U30.38, U30.GND1, U30.GNDT1, U30.GNDT2, U30.GNDT3, U30.GNDT4, U30.GNDT5, U30.GNDT6, U30.GNDT7, U30.GNDT8
GND5: C51.2, C52.2, C53.2, C54.2, C55.2, C56.2, C57.2, C58.2, C59.2, C60.2, D27.C, D29.C, D30.GND, J26.1, J27.GND, J27.GND2, J28.1, J29.6, J29.GND1, J29.GND2, J29.GND3, J29.GND4, J29.GND5, J29.GND6, J30.25, JP18.1, R56.1, R58.1, R64.1, R65.1, S11.1, S11.2, S12.1, S12.2, U31.2, U32.1, U33.1, U33.4, U33.6, U33.9, U34.2, U35.2, U36.1, U36.15, U36.38, U36.GND1, U36.GNDT1, U36.GNDT2, U36.GNDT3, U36.GNDT4, U36.GNDT5, U36.GNDT6, U36.GNDT7, U36.GNDT8
GND6: C61.2, C62.2, C63.2, C64.2, C65.2, C66.2, C67.2, C68.2, C69.2, C70.2, D32.C, D34.C, D35.GND, J31.1, J32.GND, J32.GND2, J33.1, J34.6, J34.GND1, J34.GND2, J34.GND3, J34.GND4, J34.GND5, J34.GND6, J35.25, JP21.1, R67.1, R69.1, R75.1, R76.1, S13.1, S13.2, S14.1, S14.2, U37.2, U38.1, U39.1, U39.4, U39.6, U39.9, U40.2, U41.2, U42.1, U42.15, U42.38, U42.GND1, U42.GNDT1, U42.GNDT2, U42.GNDT3, U42.GNDT4, U42.GNDT5, U42.GNDT6, U42.GNDT7, U42.GNDT8
GND7: C71.2, C72.2, C73.2, C74.2, C75.2, C76.2, C77.2, C78.2, C79.2, C80.2, D37.C, D39.C, D40.GND, J36.1, J37.GND, J37.GND2, J38.1, J39.6, J39.GND1, J39.GND2, J39.GND3, J39.GND4, J39.GND5, J39.GND6, J40.25, JP24.1, R78.1, R80.1, R86.1, R87.1, S15.1, S15.2, S16.1, S16.2, U43.2, U44.1, U45.1, U45.4, U45.6, U45.9, U46.2, U47.2, U48.1, U48.15, U48.38, U48.GND1, U48.GNDT1, U48.GNDT2, U48.GNDT3, U48.GNDT4, U48.GNDT5, U48.GNDT6, U48.GNDT7, U48.GNDT8
GND8: C81.2, C82.2, C83.2, C84.2, C85.2, C86.2, C87.2, C88.2, C89.2, C90.2, D42.C, D44.C, D45.GND, J41.1, J42.GND, J42.GND2, J43.1, J44.6, J44.GND1, J44.GND2, J44.GND3, J44.GND4, J44.GND5, J44.GND6, J45.25, JP27.1, R89.1, R91.1, R97.1, R98.1, S17.1, S17.2, S18.1, S18.2, U49.2, U50.1, U51.1, U51.4, U51.6, U51.9, U52.2, U53.2, U54.1, U54.15, U54.38, U54.GND1, U54.GNDT1, U54.GNDT2, U54.GNDT3, U54.GNDT4, U54.GNDT5, U54.GNDT6, U54.GNDT7, U54.GNDT8
GND9: C91.2, C92.2, C93.2, C94.2, C95.2, C96.2, C97.2, C98.2, C99.2, C100.2, D47.C, D49.C, D50.GND, J46.1, J47.GND, J47.GND2, J48.1, J49.6, J49.GND1, J49.GND2, J49.GND3, J49.GND4, J49.GND5, J49.GND6, J50.25, JP30.1, R100.1, R102.1, R108.1, R109.1, S19.1, S19.2, S20.1, S20.2, U55.2, U56.1, U57.1, U57.4, U57.6, U57.9, U58.2, U59.2, U60.1, U60.15, U60.38, U60.GND1, U60.GNDT1, U60.GNDT2, U60.GNDT3, U60.GNDT4, U60.GNDT5, U60.GNDT6, U60.GNDT7, U60.GNDT8
GND10: C101.2, C102.2, C103.2, C104.2, C105.2, C106.2, C107.2, C108.2, C109.2, C110.2, D52.C, D54.C, D55.GND, J51.1, J52.GND, J52.GND2, J53.1, J54.6, J54.GND1, J54.GND2, J54.GND3, J54.GND4, J54.GND5, J54.GND6, J55.25, JP33.1, R111.1, R113.1, R119.1, R120.1, S21.1, S21.2, S22.1, S22.2, U61.2, U62.1, U63.1, U63.4, U63.6, U63.9, U64.2, U65.2, U66.1, U66.15, U66.38, U66.GND1, U66.GNDT1, U66.GNDT2, U66.GNDT3, U66.GNDT4, U66.GNDT5, U66.GNDT6, U66.GNDT7, U66.GNDT8
GND11: C111.2, C112.2, C113.2, C114.2, C115.2, C116.2, C117.2, C118.2, C119.2, C120.2, D57.C, D59.C, D60.GND, J56.1, J57.GND, J57.GND2, J58.1, J59.6, J59.GND1, J59.GND2, J59.GND3, J59.GND4, J59.GND5, J59.GND6, J60.25, JP36.1, R122.1, R124.1, R130.1, R131.1, S23.1, S23.2, S24.1, S24.2, U67.2, U68.1, U69.1, U69.4, U69.6, U69.9, U70.2, U71.2, U72.1, U72.15, U72.38, U72.GND1, U72.GNDT1, U72.GNDT2, U72.GNDT3, U72.GNDT4, U72.GNDT5, U72.GNDT6, U72.GNDT7, U72.GNDT8
unnamed: JP1.1, R34.1
unnamed: D3.A, R4.2
unnamed: D5.DO, TP2.1
unnamed: JP2.1, R3.1
unnamed: J1.B5, R9.2
unnamed: J1.A5, R10.2
unnamed: D1.C, U1.1
unnamed: J1.SHLD1, J1.SHLD2, J1.SHLD3, J1.SHLD4, JP3.2
unnamed: R11.2, U6.5
unnamed: D6.A, R15.2
unnamed: J7.B5, R19.2
unnamed: J7.A5, R20.2
unnamed: R6.2, U1.5
unnamed: D8.A, R21.2
unnamed: JP4.1, R21.1
unnamed: D9.DO, TP6.1
unnamed: JP5.1, R5.1
unnamed: D2.C, U6.1
unnamed: J7.SHLD1, J7.SHLD2, J7.SHLD3, J7.SHLD4, JP6.2
unnamed: R24.2, U13.5
unnamed: D11.A, R28.2
unnamed: J12.B5, R30.2
unnamed: J12.A5, R31.2
unnamed: D14.A, R32.2
unnamed: JP7.1, R32.1
unnamed: D15.DO, TP10.1
unnamed: D12.A, R34.2
unnamed: JP8.1, R23.1
unnamed: D10.C, U13.1
unnamed: J12.SHLD1, J12.SHLD2, J12.SHLD3, J12.SHLD4, JP9.2
unnamed: R36.2, U19.5
unnamed: D17.A, R40.2
unnamed: J17.B5, R42.2
unnamed: J17.A5, R43.2
unnamed: D19.A, R44.2
unnamed: JP10.1, R44.1
unnamed: D20.DO, TP14.1
unnamed: JP11.1, R35.1
unnamed: D16.C, U19.1
unnamed: J17.SHLD1, J17.SHLD2, J17.SHLD3, J17.SHLD4, JP12.2
unnamed: R47.2, U25.5
unnamed: D22.A, R51.2
unnamed: J22.B5, R53.2
unnamed: J22.A5, R54.2
unnamed: D24.A, R55.2
unnamed: JP13.1, R55.1
unnamed: D25.DO, TP18.1
unnamed: JP14.1, R46.1
unnamed: D21.C, U25.1
unnamed: J22.SHLD1, J22.SHLD2, J22.SHLD3, J22.SHLD4, JP15.2
unnamed: R58.2, U31.5
unnamed: D27.A, R62.2
unnamed: J27.B5, R64.2
unnamed: J27.A5, R65.2
unnamed: D29.A, R66.2
unnamed: JP16.1, R66.1
unnamed: D30.DO, TP22.1
unnamed: JP17.1, R57.1
unnamed: D26.C, U31.1
unnamed: J27.SHLD1, J27.SHLD2, J27.SHLD3, J27.SHLD4, JP18.2
unnamed: R69.2, U37.5
unnamed: D32.A, R73.2
unnamed: J32.B5, R75.2
unnamed: J32.A5, R76.2
unnamed: D34.A, R77.2
unnamed: JP19.1, R77.1
unnamed: D35.DO, TP26.1
unnamed: JP20.1, R68.1
unnamed: D31.C, U37.1
unnamed: J32.SHLD1, J32.SHLD2, J32.SHLD3, J32.SHLD4, JP21.2
unnamed: R80.2, U43.5
unnamed: D37.A, R84.2
unnamed: J37.B5, R86.2
unnamed: J37.A5, R87.2
unnamed: D39.A, R88.2
unnamed: JP22.1, R88.1
unnamed: D40.DO, TP30.1
unnamed: JP23.1, R79.1
unnamed: D36.C, U43.1
unnamed: J37.SHLD1, J37.SHLD2, J37.SHLD3, J37.SHLD4, JP24.2
unnamed: R91.2, U49.5
unnamed: D42.A, R95.2
unnamed: J42.B5, R97.2
unnamed: J42.A5, R98.2
unnamed: D44.A, R99.2
unnamed: JP25.1, R99.1
unnamed: D45.DO, TP34.1
unnamed: JP26.1, R90.1
unnamed: D41.C, U49.1
unnamed: J42.SHLD1, J42.SHLD2, J42.SHLD3, J42.SHLD4, JP27.2
unnamed: R102.2, U55.5
unnamed: D47.A, R106.2
unnamed: J47.B5, R108.2
unnamed: J47.A5, R109.2
unnamed: D49.A, R110.2
unnamed: JP28.1, R110.1
unnamed: D50.DO, TP38.1
unnamed: JP29.1, R101.1
unnamed: D46.C, U55.1
unnamed: J47.SHLD1, J47.SHLD2, J47.SHLD3, J47.SHLD4, JP30.2
unnamed: R113.2, U61.5
unnamed: D52.A, R117.2
unnamed: J52.B5, R119.2
unnamed: J52.A5, R120.2
unnamed: D54.A, R121.2
unnamed: JP31.1, R121.1
unnamed: D55.DO, TP42.1
unnamed: JP32.1, R112.1
unnamed: D51.C, U61.1
unnamed: J52.SHLD1, J52.SHLD2, J52.SHLD3, J52.SHLD4, JP33.2
unnamed: R124.2, U67.5
unnamed: D57.A, R128.2
unnamed: J57.B5, R130.2
unnamed: J57.A5, R131.2
unnamed: D59.A, R132.2
unnamed: JP34.1, R132.1
unnamed: D60.DO, TP46.1
unnamed: JP35.1, R123.1
unnamed: D56.C, U67.1
unnamed: J57.SHLD1, J57.SHLD2, J57.SHLD3, J57.SHLD4, JP36.2
QWIIC_PWR: C3.1, J3.2, U5.5
QWIIC_PWR1: C17.1, J6.2, U11.5
QWIIC_PWR2: C28.1, J11.2, U17.5
QWIIC_PWR3: C38.1, J16.2, U23.5
QWIIC_PWR4: C48.1, J21.2, U29.5
QWIIC_PWR5: C58.1, J26.2, U35.5
QWIIC_PWR6: C68.1, J31.2, U41.5
QWIIC_PWR7: C78.1, J36.2, U47.5
QWIIC_PWR8: C88.1, J41.2, U53.5
QWIIC_PWR9: C98.1, J46.2, U59.5
QWIIC_PWR10: C108.1, J51.2, U65.5
QWIIC_PWR11: C118.1, J56.2, U71.5
RTS-10K: Q2.2, R18.2
RTS-10K1: Q1.2, R13.2
RTS-10K2: Q5.2, R26.2
RTS-10K3: Q7.2, R38.2
RTS-10K4: Q9.2, R49.2
RTS-10K5: Q11.2, R60.2
RTS-10K6: Q13.2, R71.2
RTS-10K7: Q15.2, R82.2
RTS-10K8: Q17.2, R93.2
RTS-10K9: Q19.2, R104.2
RTS-10K10: Q21.2, R115.2
RTS-10K11: Q23.2, R126.2
TP_EN: J5.11, R8.2, U3.3
TP_EN1: J10.11, R16.2, U10.3
TP_EN2: J15.11, R29.2, U16.3
TP_EN3: J20.11, R41.2, U22.3
TP_EN4: J25.11, R52.2, U28.3
TP_EN5: J30.11, R63.2, U34.3
TP_EN6: J35.11, R74.2, U40.3
TP_EN7: J40.11, R85.2, U46.3
TP_EN8: J45.11, R96.2, U52.3
TP_EN9: J50.11, R107.2, U58.3
TP_EN10: J55.11, R118.2, U64.3
TP_EN11: J60.11, R129.2, U70.3
VIN: C7.1, D4.C, Q3.2, R8.1, U3.1, U5.1
VIN1: C8.1, D7.C, Q4.2, R16.1, U10.1, U11.1
VIN2: C21.1, D13.C, Q6.2, R29.1, U16.1, U17.1
VIN3: C31.1, D18.C, Q8.2, R41.1, U22.1, U23.1
VIN4: C41.1, D23.C, Q10.2, R52.1, U28.1, U29.1
VIN5: C51.1, D28.C, Q12.2, R63.1, U34.1, U35.1
VIN6: C61.1, D33.C, Q14.2, R74.1, U40.1, U41.1
VIN7: C71.1, D38.C, Q16.2, R85.1, U46.1, U47.1
VIN8: C81.1, D43.C, Q18.2, R96.1, U52.1, U53.1
VIN9: C91.1, D48.C, Q20.2, R107.1, U58.1, U59.1
VIN10: C101.1, D53.C, Q22.2, R118.1, U64.1, U65.1
VIN11: C111.1, D58.C, Q24.2, R129.1, U70.1, U71.1
V_BATT: C6.1, C15.1, J4.2, J5.12, Q3.3, U1.3, U4.2, U4.3
V_BATT1: C11.1, C16.1, J8.2, J10.12, Q4.3, U6.3, U9.2, U9.3
V_BATT2: C23.1, C27.1, J13.2, J15.12, Q6.3, U13.3, U15.2, U15.3
V_BATT3: C33.1, C37.1, J18.2, J20.12, Q8.3, U19.3, U21.2, U21.3
V_BATT4: C43.1, C47.1, J23.2, J25.12, Q10.3, U25.3, U27.2, U27.3
V_BATT5: C53.1, C57.1, J28.2, J30.12, Q12.3, U31.3, U33.2, U33.3
V_BATT6: C63.1, C67.1, J33.2, J35.12, Q14.3, U37.3, U39.2, U39.3
V_BATT7: C73.1, C77.1, J38.2, J40.12, Q16.3, U43.3, U45.2, U45.3
V_BATT8: C83.1, C87.1, J43.2, J45.12, Q18.3, U49.3, U51.2, U51.3
V_BATT9: C93.1, C97.1, J48.2, J50.12, Q20.3, U55.3, U57.2, U57.3
V_BATT10: C103.1, C107.1, J53.2, J55.12, Q22.3, U61.3, U63.2, U63.3
V_BATT11: C113.1, C117.1, J58.2, J60.12, Q24.3, U67.3, U69.2, U69.3
V_USB: C19.1, D4.A, J1.VBUS1, J1.VBUS2, J5.10, JP2.2, Q3.1, R7.2, U1.4
V_USB1: C12.1, D7.A, J7.VBUS1, J7.VBUS2, J10.10, JP5.2, Q4.1, R1.2, U6.4
V_USB2: C24.1, D13.A, J12.VBUS1, J12.VBUS2, J15.10, JP8.2, Q6.1, R22.2, U13.4
V_USB3: C34.1, D18.A, J17.VBUS1, J17.VBUS2, J20.10, JP11.2, Q8.1, R33.2, U19.4
V_USB4: C44.1, D23.A, J22.VBUS1, J22.VBUS2, J25.10, JP14.2, Q10.1, R45.2, U25.4
V_USB5: C54.1, D28.A, J27.VBUS1, J27.VBUS2, J30.10, JP17.2, Q12.1, R56.2, U31.4
V_USB6: C64.1, D33.A, J32.VBUS1, J32.VBUS2, J35.10, JP20.2, Q14.1, R67.2, U37.4
V_USB7: C74.1, D38.A, J37.VBUS1, J37.VBUS2, J40.10, JP23.2, Q16.1, R78.2, U43.4
V_USB8: C84.1, D43.A, J42.VBUS1, J42.VBUS2, J45.10, JP26.2, Q18.1, R89.2, U49.4
V_USB9: C94.1, D48.A, J47.VBUS1, J47.VBUS2, J50.10, JP29.2, Q20.1, R100.2, U55.4
V_USB10: C104.1, D53.A, J52.VBUS1, J52.VBUS2, J55.10, JP32.2, Q22.1, R111.2, U61.4
V_USB11: C114.1, D58.A, J57.VBUS1, J57.VBUS2, J60.10, JP35.2, Q24.1, R122.2, U67.4
