scottypres/Arduino-Paragliding-Varios/Sparkfun ESP32 WROOM Vario/Arduino Scripts/experiments/wifi_manager_ota/wifi_manager_ota.ino

#include <Arduino.h>
#include <WiFi.h>
#include <ESPmDNS.h>
#include <NetworkUdp.h>
#include <ArduinoOTA.h>
#include <WiFiManager.h>

namespace {
const char *const kWifiSsid = "Warehouse_2G";
const char *const kWifiPassword = "Scottypres";
const char *const kOtaHostname = "vario-feather-v2";
const char *const kConfigPortalSsid = "VarioFeatherSetup";
const char *const kConfigPortalPassword = "configureme";

constexpr uint8_t kBuzzerPin = 13;
constexpr uint8_t kDifferentialBuzzerPinA = A6;
constexpr uint8_t kDifferentialBuzzerPinB = A7;
constexpr bool kD13BuzzerEnabled = false;
constexpr uint8_t kBuzzerChannel = 0;
constexpr uint32_t kBuzzerToneHz = 4000;
constexpr uint32_t kBuzzerPeriodMs = 5000;
constexpr uint32_t kBuzzerOnMs = 500;
constexpr uint8_t kBuzzerResolutionBits = 8;
constexpr uint32_t kDifferentialHalfPeriodUs = 125;

uint32_t lastOtaProgressMs = 0;
uint32_t buzzerCycleStartMs = 0;
bool buzzerOn = false;

void silenceDifferentialBuzzer() {
  digitalWrite(kDifferentialBuzzerPinA, LOW);
  digitalWrite(kDifferentialBuzzerPinB, LOW);
}

void playDifferentialBuzzer(uint32_t durationMs) {
  const uint32_t startMs = millis();
  while (millis() - startMs < durationMs) {
    digitalWrite(kDifferentialBuzzerPinA, HIGH);
    digitalWrite(kDifferentialBuzzerPinB, LOW);
    delayMicroseconds(kDifferentialHalfPeriodUs);

    digitalWrite(kDifferentialBuzzerPinA, LOW);
    digitalWrite(kDifferentialBuzzerPinB, HIGH);
    delayMicroseconds(kDifferentialHalfPeriodUs);
  }
  silenceDifferentialBuzzer();
}

void setBuzzer(bool enabled) {
  if (enabled == buzzerOn) {
    return;
  }

  if (enabled) {
    if (kD13BuzzerEnabled) {
      ledcWriteTone(kBuzzerPin, kBuzzerToneHz);
    }
    playDifferentialBuzzer(kBuzzerOnMs);
    if (kD13BuzzerEnabled) {
      ledcWriteTone(kBuzzerPin, 0);
    }
    digitalWrite(kBuzzerPin, LOW);
  } else {
    if (kD13BuzzerEnabled) {
      ledcWriteTone(kBuzzerPin, 0);
    }
    digitalWrite(kBuzzerPin, LOW);
    silenceDifferentialBuzzer();
  }

  buzzerOn = enabled;
}

void startBuzzer() {
  pinMode(kBuzzerPin, OUTPUT);
  pinMode(kDifferentialBuzzerPinA, OUTPUT);
  pinMode(kDifferentialBuzzerPinB, OUTPUT);
  digitalWrite(kBuzzerPin, LOW);
  digitalWrite(kDifferentialBuzzerPinA, LOW);
  digitalWrite(kDifferentialBuzzerPinB, LOW);
  if (kD13BuzzerEnabled && !ledcAttachChannel(kBuzzerPin, kBuzzerToneHz, kBuzzerResolutionBits, kBuzzerChannel)) {
    Serial.println("D13 buzzer PWM setup failed");
  }
  buzzerCycleStartMs = millis();
}

void serviceBuzzer() {
  const uint32_t now = millis();
  while (now - buzzerCycleStartMs >= kBuzzerPeriodMs) {
    buzzerCycleStartMs += kBuzzerPeriodMs;
  }

  setBuzzer(now - buzzerCycleStartMs < kBuzzerOnMs);
}

void onConfigPortal(WiFiManager *manager) {
  Serial.println("WiFiManager configuration portal started");
  Serial.print("Portal SSID: ");
  Serial.println(manager->getConfigPortalSSID());
  Serial.print("Portal IP: ");
  Serial.println(WiFi.softAPIP());
}

bool connectRequestedWifi() {
  WiFi.mode(WIFI_STA);
  WiFi.setHostname(kOtaHostname);
  WiFi.begin(kWifiSsid, kWifiPassword);

  Serial.printf("Connecting to WiFi SSID: %s\n", kWifiSsid);
  const uint32_t startMs = millis();
  while (WiFi.status() != WL_CONNECTED && millis() - startMs < 30000) {
    serviceBuzzer();
    delay(100);
  }

  if (WiFi.status() != WL_CONNECTED) {
    Serial.println("Requested WiFi connection failed; starting setup portal");
    WiFi.disconnect(false);
    return false;
  }

  Serial.print("Connected to SSID: ");
  Serial.println(WiFi.SSID());
  Serial.print("IP address: ");
  Serial.println(WiFi.localIP());
  return true;
}

void startWifi() {
  WiFi.mode(WIFI_STA);
  if (connectRequestedWifi()) {
    return;
  }

  WiFiManager wm;
  wm.setDebugOutput(true);
  wm.setHostname(kOtaHostname);
  wm.setAPCallback(onConfigPortal);
  wm.setConnectTimeout(30);
  wm.setConfigPortalTimeout(180);
  wm.preloadWiFi(kWifiSsid, kWifiPassword);

  Serial.printf("Connecting to WiFi SSID: %s\n", kWifiSsid);
  if (!wm.autoConnect(kConfigPortalSsid, kConfigPortalPassword)) {
    Serial.println("WiFi connection/configuration failed; restarting");
    delay(1000);
    ESP.restart();
  }

  Serial.print("Connected to SSID: ");
  Serial.println(WiFi.SSID());
  Serial.print("IP address: ");
  Serial.println(WiFi.localIP());
}

void startOta() {
  ArduinoOTA.setHostname(kOtaHostname);

  ArduinoOTA
    .onStart([]() {
      const char *type = ArduinoOTA.getCommand() == U_FLASH ? "sketch" : "filesystem";
      Serial.printf("OTA update started: %s\n", type);
    })
    .onEnd([]() {
      Serial.println("\nOTA update finished");
    })
    .onProgress([](unsigned int progress, unsigned int total) {
      if (millis() - lastOtaProgressMs > 500) {
        Serial.printf("OTA progress: %u%%\n", progress / (total / 100));
        lastOtaProgressMs = millis();
      }
    })
    .onError([](ota_error_t error) {
      Serial.printf("OTA error[%u]: ", error);
      if (error == OTA_AUTH_ERROR) {
        Serial.println("auth failed");
      } else if (error == OTA_BEGIN_ERROR) {
        Serial.println("begin failed");
      } else if (error == OTA_CONNECT_ERROR) {
        Serial.println("connect failed");
      } else if (error == OTA_RECEIVE_ERROR) {
        Serial.println("receive failed");
      } else if (error == OTA_END_ERROR) {
        Serial.println("end failed");
      } else {
        Serial.println("unknown error");
      }
    });

  ArduinoOTA.begin();
  Serial.printf("ArduinoOTA ready as %s.local\n", kOtaHostname);
}
}  // namespace

void setup() {
  Serial.begin(115200);
  delay(1000);

  Serial.println();
  Serial.println("Booting Vario Feather WiFiManager OTA sketch");
  startBuzzer();
  startWifi();
  startOta();
}

void loop() {
  ArduinoOTA.handle();
  serviceBuzzer();
  delay(10);
}
