scottypres/Arduino-Paragliding-Varios/Sparkfun ESP32 WROOM Vario/Arduino Scripts/Sparkfun_Vario/sensors.h

#pragma once

#include "globals.h"

bool i2cAddressPresent(uint8_t address);
void printI2cScan();
bool tryBmpAddress(uint8_t address);
void startBmp();
void startSht();
void initSensors();
void completeBmpWarmup();
void readSensors();
