scottypres/Arduino-Paragliding-Varios/Sparkfun ESP32 WROOM Vario/Arduino Scripts/Sparkfun_Vario/globals.h

#pragma once

#include "radio_config.h"

#include <Arduino.h>
#include <Adafruit_GFX.h>
#include <Adafruit_BMP5xx.h>
#include <Adafruit_SH110X.h>
#include <Adafruit_SHT4x.h>
#include <ESP.h>
#include <FS.h>
#include <Preferences.h>
#include <SD.h>
#include <SPI.h>
#include <SparkFun_MAX1704x_Fuel_Gauge_Arduino_Library.h>
#include <TinyGPSPlus.h>
#include <ESPAsyncWebServer.h>
#include <DNSServer.h>
#include <WiFi.h>
#include <Wire.h>

// SparkFun Thing Plus ESP32 WROOM-C pin mapping for this carrier board.
constexpr uint8_t kQwiicPowerPin = 0;
constexpr uint8_t kSdCsPin = 5;
constexpr uint8_t kSdSckPin = 18;
constexpr uint8_t kSdMisoPin = 19;
constexpr uint8_t kSdMosiPin = 23;

constexpr uint8_t kI2cSdaPin = 33;
constexpr uint8_t kI2cSclPin = 32;

constexpr uint8_t kBatteryI2cSdaPin = 21;  // Onboard MAX17048 default I2C SDA.
constexpr uint8_t kBatteryI2cSclPin = 22;  // Onboard MAX17048 default I2C SCL.
constexpr uint8_t kGpsRxPin = 21;  // GPS TX on Qwiic SDA into ESP32 RX.
constexpr uint8_t kGpsTxPin = 22;  // GPS RX on Qwiic SCL from ESP32 TX.
constexpr uint32_t kGpsBaud = 115200;
constexpr uint32_t kGpsClockResyncMs = 60000;  // re-seed the RTC from a fresh GPS fix this often
constexpr uint32_t kGpsFixMaxAgeMs = 1500;     // only re-seed from a GPS time this recent

constexpr uint8_t kBuzzerPins[] = {13, 26, 27};
constexpr uint8_t kBuzzerResolutionBits = 8;

constexpr uint8_t kEncoderAPin = 39;
constexpr uint8_t kEncoderBPin = 36;
constexpr uint8_t kBackButtonPin = 35;
constexpr uint8_t kEncoderButtonPin = 34;
constexpr uint8_t kConfirmButtonPin = 4;

constexpr uint32_t kDebounceMs = 35;
constexpr uint32_t kBatteryRefreshHoldMs = 800;   // hold select alone -> refresh battery
constexpr uint32_t kLockHoldMs = 3000;            // hold select+back -> lock/unlock buttons
constexpr uint32_t kDisplayRefreshMs = 100;
constexpr uint32_t kGpsDebugMs = 1000;
constexpr uint32_t kSensorReadMs = 100;
constexpr uint32_t kBmpWarmupMs = 5000;
constexpr uint32_t kBmpRetryMs = 2000;
constexpr uint32_t kBmpPowerUpDelayMs = 50;
constexpr const char *kDataLogPath = "/vario_log.csv";
constexpr const char *kOldDataLogPath = "/vario_log_old.csv";
constexpr const char *kBatteryLogPath = "/battery_log.csv";
constexpr uint8_t kBuzzerCount = sizeof(kBuzzerPins) / sizeof(kBuzzerPins[0]);
constexpr uint32_t kWifiConnectTimeoutMs = 7000;
constexpr uint32_t kWifiRetryDelayMs = 5000;
constexpr uint16_t kWebServerPort = 80;
constexpr uint8_t kMaxWifiNetworks = 6;
constexpr uint8_t kOledAddress = 0x3C;
constexpr int8_t kOledResetPin = -1;
constexpr int16_t kOledWidth = 128;
constexpr int16_t kOledHeight = 64;
constexpr uint8_t kMaxOledWindows = 8;         // capacity; runtime count is oledWindowCount
constexpr uint8_t kDefaultOledWindowCount = 3;  // data screens cycled by the encoder in view mode
constexpr const char *kOtaHostname = "sparkfun-vario";
constexpr const char *kOtaPassword = "password";
constexpr const char *kWifiPortalSsid = "SparkFun-Vario pw:password";  // SSID advertises the AP password
constexpr const char *kWifiPortalPassword = "password";  // WPA2 minimum is 8 chars; this is exactly 8
constexpr const char *kPrefsNamespace = "vario";
constexpr const char *kPrefAudio = "audio";
constexpr const char *kPrefVolume = "volume";
constexpr const char *kPrefResponse = "response";
constexpr const char *kPrefHasAltitudeZero = "hasZero";
constexpr const char *kPrefAltitudeZeroFt = "zeroFt";
constexpr const char *kPrefWifiInitialized = "wifiInit";
constexpr const char *kPrefWifiCount = "wifiCount";
constexpr const char *kPrefPixelEnabled = "pixEnable";
constexpr const char *kPrefPixelMode = "pixMode";
constexpr const char *kPrefPixelColor = "pixColor";
constexpr const char *kPrefDataLogging = "dataLog";
constexpr const char *kPrefLogRate = "logRate";
constexpr const char *kPrefGpsEnabled = "gpsEn";
constexpr const char *kPrefBluetooth = "btClassic";
constexpr const char *kPrefWifiEnabled = "wifiOn";
constexpr const char *kPrefBootBlinds = "bootBlinds";
// ponytail: SmartBlinds ESP32 has a DHCP reservation; hardcode IP, skip mDNS
constexpr const char *kBlindsHost = "192.168.50.112";
constexpr const char *kPrefAltitudeSource = "altSrc";  // false=baro, true=GPS
constexpr const char *kPrefBatteryReadRate = "batRate";
constexpr const char *kPrefBuzzerCount = "buzzCount";
constexpr const char *kPrefLiftOnMps = "liftOn";
constexpr const char *kPrefLiftHz = "liftHz";
constexpr const char *kPrefLiftSlopeHz = "liftSlope";
constexpr const char *kPrefBeepTempo = "beepTempo";
constexpr const char *kPrefTwoToneLift = "ttLift";
constexpr const char *kPrefSinkOnMps = "sinkOn";
constexpr const char *kPrefSinkHz = "sinkHz";
constexpr const char *kPrefTwoToneSink = "ttSink";
constexpr const char *kPrefImuEnabled = "imuEn";
constexpr const char *kPrefImuHasLevel = "imuLvl";
constexpr const char *kPrefImuPitchZero = "imuP0";
constexpr const char *kPrefImuRollZero = "imuR0";
constexpr const char *kPrefImuSwapAxes = "imuSwap";
constexpr const char *kPrefImuMirrorPitch = "imuMirP";
constexpr const char *kPrefImuMirrorRoll = "imuMirR";
constexpr const char *kPrefFlightStartMph = "flStartV";
constexpr const char *kPrefFlightStartSecs = "flStartT";
constexpr const char *kPrefFlightStopMph = "flStopV";
constexpr const char *kPrefFlightStopSecs = "flStopT";
constexpr const char *kPrefFlightAutoStart = "flAutoS";
constexpr const char *kPrefFlightAutoStop = "flAutoE";
constexpr const char *kPrefLocked = "ctlLock";
constexpr const char *kPrefLockHoldMs = "lockHold";
constexpr const char *kPrefLockBeep = "lockBeep";
constexpr const char *kPrefClock12h = "clk12";    // false=24h, true=12h AM/PM
constexpr const char *kPrefTzMinutes = "tzMin";   // local time = UTC + this
constexpr const char *kPrefEarbudName = "btEarbud";  // A2DP target name (BT firmware)
constexpr const char *kPrefMaxLogMb = "maxLogMb";    // idle log size cap, MB (0 = unlimited)
constexpr const char *kPrefBleGps = "bleGps";        // stream $GPGGA/$GPRMC to phone apps
constexpr const char *kPrefBleName = "bleName";      // BLE advertised name (applied at boot)
constexpr char kDefaultBleName[] = "SparkFun Vario";
constexpr char kDefaultEarbudName[] = "TOZO-A1";
constexpr uint8_t kMaxEarbudNameLen = 63;
constexpr float kMetersToFeet = 3.28084F;
constexpr float kFeetToMeters = 1.0F / kMetersToFeet;
constexpr float kSeaLevelPressureHpa = 1013.25F;
constexpr float kAltitudeSmoothingAlpha = 0.25F;
constexpr float kVarioResponseAlpha[] = {0.18F, 0.32F, 0.50F, 0.72F};
const char *const kVarioResponseLabels[] = {"Smooth", "Normal", "Quick", "Direct"};
constexpr uint8_t kVarioResponseCount = sizeof(kVarioResponseAlpha) / sizeof(kVarioResponseAlpha[0]);
// Vario tone model defaults (runtime-tunable via web Settings -> Vario Tone).
constexpr float kLiftThresholdMps = 0.18F;
constexpr float kSinkThresholdMps = -1.80F;
constexpr uint32_t kLiftFreqBaseHz = 720;
constexpr uint32_t kLiftFreqIncrementHzPerMps = 170;
constexpr uint32_t kSinkFreqBaseHz = 360;
constexpr uint32_t kSinkFreqDecrementHzPerMps = 45;
constexpr uint32_t kMinToneHz = 130;
constexpr uint32_t kMaxToneHz = 4500;  // piezo resonance lives ~2.7-4.5 kHz (Buzzer Lab)
constexpr uint32_t kToneQuantizeHz = 10;
constexpr uint8_t kDefaultBuzzerVolumePercent = 40;
constexpr uint8_t kMinBuzzerVolumePercent = 5;
constexpr uint8_t kMaxBuzzerVolumePercent = 100;
constexpr uint32_t kBuzzerTestDurationMs = 3000;
constexpr uint32_t kBuzzerTestToneHz = 1000;
// Button lock (hold Select+Back to toggle; hold time set in the web UI).
constexpr uint32_t kDefaultLockHoldMs = 3000;
constexpr uint32_t kMinLockHoldMs = 1000;
constexpr uint32_t kMaxLockHoldMs = 10000;
constexpr uint32_t kLockSplashMs = 1500;
constexpr uint32_t kLockPeekMs = 8000;  // locked + OLED off: how long a key press shows the screen
constexpr uint32_t kLockBeepHz = 1000;
constexpr uint32_t kLockBeepMs = 100;
constexpr uint32_t kPixelUpdateMs = 50;
constexpr uint16_t kLogTailBytes = 4096;
constexpr uint32_t kBatteryLogIntervalMs = 30000;
constexpr const char *kDataLogHeader =
    "millis,iso_utc,display_altitude_ft,raw_altitude_ft,vario_mps,temp_f,humidity_pct,"
    "gps_fix,latitude,longitude,gps_altitude_m,gps_speed_kmph,gps_sats_used,"
    "gps_sats_seen,gps_hdop,battery_voltage,battery_percent,"
    "pitch_deg,roll_deg,g_force";
constexpr const char *kBatteryLogHeader =
    "millis,elapsed_s,iso_utc,battery_voltage,battery_percent,wifi_enabled,wifi_status,"
    "wifi_ssid,bluetooth_enabled,oled_enabled";

struct StoredWifiNetwork {
  String ssid;
  String password;
};

// Radios are split across firmwares (see radio_config.h): the WiFi build has
// no Bluetooth and the BT build has no WiFi. Hide the menu items a given build
// can't act on so the OLED never offers a dead toggle.
enum MenuItem : uint8_t {
  kMenuLock = 0,
  kMenuOled,
#ifndef VARIO_DISABLE_WIFI
  kMenuLockWifi,  // staged WiFi toggle in Power & Lock; applied by "Lock now"
#endif
#ifndef VARIO_DISABLE_BT
  kMenuLockBt,    // staged Bluetooth toggle in Power & Lock; applied by "Lock now"
#endif
  kMenuClockFormat,
  kMenuTzOffset,
  kMenuDataLogging,
  kMenuSetAltitudeZero,
  kMenuClearAltitudeZero,
  kMenuAudio,
  kMenuVolume,
  kMenuBuzzers,
  kMenuResponse,
  kMenuToneTest,
  kMenuGpsLogRate,
  kMenuBatteryReadRate,
  kMenuGpsEnabled,
#ifndef VARIO_DISABLE_BT
  kMenuBleGps,  // stream GPS sentences over BLE to phone apps
#endif
  kMenuAltitudeSource,
  kMenuImuEnabled,
  kMenuImuLevel,
  kMenuImuClearLevel,
  kMenuImuSwapAxes,
  kMenuImuMirrorPitch,
  kMenuImuMirrorRoll,
  kMenuFlight,
  kMenuFlightAutoStart,
  kMenuFlightAutoStop,
#ifndef VARIO_DISABLE_BT
  kMenuBluetooth,
#endif
  kMenuBatteryLogging,
#ifndef VARIO_DISABLE_WIFI
  kMenuWifiEnabled,
  kMenuWifiSetup,
  kMenuForgetWifi,
  kMenuBlinds,      // enter SmartBlinds remote screen
  kMenuBootBlinds,  // boot straight into the blinds screen
#endif
  kMenuSwitchFirmware,
  kMenuAbout,  // read-only: firmware version + build date
  kMenuCount
};

// Two-level settings menu: the top level lists categories, each opening into a
// subset of MenuItem entries (see kMenuCategories in globals.cpp).
struct MenuCategory {
  const char *name;
  const uint8_t *items;  // MenuItem values, in display order
  uint8_t count;
};
extern const MenuCategory kMenuCategories[];
extern const uint8_t kMenuCategoryCount;

enum BatteryLogMenuItem : uint8_t {
  kBatteryLogMenuStop = 0,
#ifndef VARIO_DISABLE_WIFI
  kBatteryLogMenuWifi,
#endif
#ifndef VARIO_DISABLE_BT
  kBatteryLogMenuBluetooth,
#endif
  kBatteryLogMenuOled,
  kBatteryLogMenuCount
};

enum PixelMode : uint8_t {
  kPixelModeColor = 0,
  kPixelModeRainbow,
  kPixelModeTemperature,
  kPixelModeHumidity,
  kPixelModeAltitude,
  kPixelModeSatellites,
  kPixelModeBattery,
  kPixelModeCount
};

struct Button {
  uint8_t pin;
  bool usePullup;
  bool stablePressed;
  bool lastRawPressed;
  uint32_t lastChangeMs;
  bool pressedEvent;    // rising edge (press down)
  bool releasedEvent;   // falling edge (release)
  uint32_t pressStartMs;  // millis() when the current/last press began
};

const uint32_t kLogRatesMs[] = {200, 500, 1000, 2000, 5000, 10000, 30000, 60000};
const char *const kLogRateLabels[] = {"0.2 sec", "0.5 sec", "1 sec", "2 sec", "5 sec", "10 sec", "30 sec", "60 sec"};
const uint32_t kBatteryReadRatesMs[] = {5000, 10000, 30000, 60000, 120000, 300000};
const char *const kBatteryReadRateLabels[] = {"5 sec", "10 sec", "30 sec", "60 sec", "2 min", "5 min"};
const char *const kBuzzerTestLabels[] = {"B1 pin13", "B2 pin26", "B3 pin27", "All"};
constexpr uint8_t kLogRateCount = sizeof(kLogRatesMs) / sizeof(kLogRatesMs[0]);
constexpr uint8_t kBatteryReadRateCount = sizeof(kBatteryReadRatesMs) / sizeof(kBatteryReadRatesMs[0]);
constexpr uint8_t kBuzzerTestTargetCount = sizeof(kBuzzerTestLabels) / sizeof(kBuzzerTestLabels[0]);

// Shared library objects (defined in globals.cpp).
extern Adafruit_SH1106G oled;
extern Adafruit_BMP5xx bmp;
extern Adafruit_SHT4x sht4;
extern Preferences prefs;
extern TinyGPSPlus gps;
extern TinyGPSCustom gpsGpgsvSatellites;
extern TinyGPSCustom gpsGngsvSatellites;
extern TinyGPSCustom gpsGlgsvSatellites;
extern TinyGPSCustom gpsGagsvSatellites;
extern TinyGPSCustom gpsBdgsvSatellites;
extern HardwareSerial gpsSerial;
extern TwoWire batteryWire;
extern SFE_MAX1704X batteryGauge;
extern AsyncWebServer webServer;
extern DNSServer dnsServer;  // captive-portal DNS while broadcasting the AP

extern Button backButton;
extern Button encoderButton;
extern Button confirmButton;

// Shared mutable state (defined in globals.cpp).
extern bool oledReady;
extern bool oledDisplayEnabled;  // OLED menu toggle; any button press re-enables
extern bool sdReady;
extern bool bmpReady;
extern bool shtReady;
extern bool dataLoggingEnabled;
extern bool gpsEnabled;  // false = GPS UART never claimed, frees the shared pins for the battery gauge
extern bool useGpsAltitude;
extern bool imuEnabled;
extern bool imuReady;      // LSM6DSV16X accel/gyro responding
extern bool imuLevelSaved;
extern bool imuSwapAxes;     // swap pitch/roll axes for a 90-deg rotated mount
extern bool imuMirrorPitch;  // negate pitch after axis mapping
extern bool imuMirrorRoll;   // negate roll after axis mapping
extern bool audioEnabled;
extern bool bluetoothEnabled;
extern bool batteryGaugeReady;
extern bool batteryLoggingActive;
extern bool batteryLogWifiEnabled;
extern bool batteryLogBluetoothEnabled;
extern bool batteryLogOledEnabled;
extern bool batteryLogSavedWifiEnabled;
extern bool batteryLogSavedBluetoothEnabled;
extern bool batteryLogSavedOledEnabled;
extern bool wifiEnabled;
extern bool blindsMode;          // SmartBlinds remote screen is in front
extern bool bootBlindsMode;      // persisted: boot into blindsMode
extern bool blindsOnline;        // last TCP probe of kBlindsHost succeeded
extern const char *blindsMotion; // last command result shown on the OLED
extern bool wifiReady;
extern bool otaReady;
extern bool wifiAttemptActive;
extern bool webServerReady;
extern bool webServerRoutesConfigured;
extern bool wifiPortalActive;
extern bool altitudeFilterInitialized;
extern bool bmpWarmupComplete;
extern bool altitudeZeroSaved;
extern bool varioRateInitialized;
extern bool liftAudioActive;
extern bool sinkAudioActive;
extern bool liftBeepOn;
extern bool toneTestActive;
extern bool buzzerLabActive;   // web Buzzer Lab is driving the buzzers; vario audio paused
extern bool editingMenuItem;
extern bool inMenuMode;       // false = data windows, true = settings menu
extern bool controlsLocked;   // buttons/encoder ignored except the unlock hold
extern bool lockBeepEnabled;
extern uint32_t lockHoldMs;
extern bool clock12h;            // false=24h, true=12h AM/PM
extern int16_t tzOffsetMinutes;  // local time = UTC + this
extern uint32_t lockSplashUntilMs;  // show Locked/Unlocked splash until this time
// Power & Lock staging: the OLED/WiFi/BT toggles in that menu don't act until
// "Lock now" applies them all at once — so the panel never dies under you.
extern bool pendingOledOn;
extern bool pendingWifiOn;
extern bool pendingBtOn;
extern uint32_t oledPeekUntilMs;  // locked peek: panel re-darkens at this time (0 = idle)
extern bool pixelEnabled;
extern uint8_t activeWindow;  // 0..oledWindowCount-1, cycled by encoder in view mode
extern uint8_t selectedMenuItem;      // MenuItem currently highlighted (within a category)
extern uint8_t selectedCategory;      // highlighted category at the top level
extern bool menuInCategory;           // false = category list, true = item list
extern uint8_t categoryItemIndex;     // highlighted position within the open category
extern uint8_t selectedBatteryLogMenuItem;
extern uint8_t logRateIndex;
extern uint8_t batteryReadRateIndex;
extern uint8_t buzzerVolumePercent;
extern String btEarbudName;  // Bluetooth earbud name the BT firmware connects to
extern bool bleSendGps;      // stream $GPGGA/$GPRMC over BLE when GPS has a fix
extern String bleDeviceName; // advertised BLE name (read at boot; some apps key on it)

// Runtime-tunable vario tone model (web Settings -> Vario Tone).
extern uint8_t buzzerCount;        // 1..kBuzzerCount simultaneous buzzers
extern float liftThresholdMps;     // climb beeping starts here
extern uint16_t liftFreqBaseHz;    // pitch at threshold
extern uint16_t liftFreqSlopeHz;   // added Hz per m/s of climb
extern uint8_t beepTempoPercent;   // 50..200, scales beep cadence
extern bool twoToneLift;           // each climb beep steps up a major third
extern float sinkThresholdMps;     // sink alarm starts here (negative)
extern uint16_t sinkFreqBaseHz;    // sink tone pitch at threshold
extern bool twoToneSink;           // sink tone warbles instead of droning
extern uint8_t varioResponseIndex;
extern uint8_t toneTestPatternIndex;
extern uint8_t buzzerTestTargetIndex;
extern uint8_t wifiNetworkCount;
extern uint8_t wifiAttemptIndex;
extern uint8_t pixelMode;
extern uint8_t bmpAddress;
extern uint32_t pixelColor;

extern uint32_t lastDisplayMs;
extern uint32_t lastGpsLogMs;
extern uint32_t batteryLogStartMs;
extern uint32_t lastBatteryLogMs;
extern uint32_t lastGpsDebugMs;
extern uint32_t lastSensorReadMs;
extern uint32_t lastBmpInitAttemptMs;
extern uint32_t lastImuInitAttemptMs;
extern uint32_t lastWifiAttemptMs;
extern uint32_t wifiAttemptStartMs;
extern uint32_t lastPixelUpdateMs;
extern uint32_t lastBatteryReadMs;
extern uint32_t bmpWarmupStartMs;
extern uint32_t lastVarioRateUpdateMs;
extern uint32_t liftPhaseStartMs;
extern uint32_t currentToneHz;
extern uint32_t toneTestStartMs;
extern uint32_t lastBuzzerLabMs;  // last Buzzer Lab keepalive; auto-stops if browser goes away
extern uint8_t currentToneMask;
extern uint16_t rainbowHue;

extern float baroPressurePa;      // raw BMP pressure in Pa (NAN until first read)
extern uint16_t maxLogMb;         // idle log rotates past this size; 0 = unlimited
extern uint64_t sdTotalBytes;     // cached card capacity (refreshed by refreshSdUsage)
extern uint64_t sdUsedBytes;
extern float altitudeFt;
extern float smoothedAltitudeFt;
extern float previousVarioAltitudeFt;
extern float baselineSmoothedAltitudeFt;
extern float displayAltitudeFt;
extern float verticalSpeedMps;
extern float temperatureF;
extern float humidityPercent;
extern float imuPitchDeg;        // level-adjusted, smoothed
extern float imuRollDeg;         // level-adjusted, smoothed
extern float imuGForce;          // total acceleration in g
extern float imuPitchOffsetDeg;  // level-to-horizon calibration
extern float imuRollOffsetDeg;
extern uint8_t oledWindowCount;      // active OLED windows (1..kMaxOledWindows)
extern bool flightActive;
extern uint32_t flightStartMs;
extern uint32_t flightElapsedSec;
extern float avgSpeedKmph;           // running average ground speed during flight
extern uint8_t flightStartSpeedMph;  // flight-start ground speed threshold (mph)
extern uint8_t flightStartSecs;      // hold time above start speed (s)
extern uint8_t flightStopSpeedMph;   // flight-stop ground speed threshold (mph)
extern uint8_t flightStopSecs;       // hold time below stop speed (s)
extern bool flightAutoStart;         // auto-detect flight start from ground speed
extern bool flightAutoStop;          // auto-detect flight end from ground speed
extern float batteryVoltage;
extern float batteryPercent;
extern String connectedWifiSsid;
extern StoredWifiNetwork wifiNetworks[kMaxWifiNetworks];

// Shared utility helpers (defined in globals.cpp).
float clampFloat(float value, float low, float high);
String floatOrDash(float value, uint8_t decimals, const char *suffix = "");
