scottypres/Arduino-Paragliding-Varios/Sparkfun ESP32 WROOM Vario/Arduino Scripts/Sparkfun_Vario/globals.cpp

#include "globals.h"

Adafruit_SH1106G oled(kOledWidth, kOledHeight, &Wire, kOledResetPin);
Adafruit_BMP5xx bmp;
Adafruit_SHT4x sht4;
Preferences prefs;
TinyGPSPlus gps;
TinyGPSCustom gpsGpgsvSatellites(gps, "GPGSV", 3);
TinyGPSCustom gpsGngsvSatellites(gps, "GNGSV", 3);
TinyGPSCustom gpsGlgsvSatellites(gps, "GLGSV", 3);
TinyGPSCustom gpsGagsvSatellites(gps, "GAGSV", 3);
TinyGPSCustom gpsBdgsvSatellites(gps, "BDGSV", 3);
HardwareSerial gpsSerial(1);
TwoWire batteryWire(1);
SFE_MAX1704X batteryGauge(MAX1704X_MAX17048);
#ifndef VARIO_DISABLE_WIFI
AsyncWebServer webServer(kWebServerPort);
DNSServer dnsServer;
#endif

Button backButton = {kBackButtonPin, false, false, false, 0, false};
Button encoderButton = {kEncoderButtonPin, false, false, false, 0, false};
Button confirmButton = {kConfirmButtonPin, true, false, false, 0, false};

bool oledReady = false;
bool oledDisplayEnabled = true;
bool sdReady = false;
bool bmpReady = false;
bool shtReady = false;
bool dataLoggingEnabled = true;
bool gpsEnabled = true;
bool useGpsAltitude = false;
bool imuEnabled = true;
bool imuReady = false;
bool imuLevelSaved = false;
bool imuSwapAxes = true;  // default: unit is mounted rotated 90 deg to the right
bool imuMirrorPitch = false;
bool imuMirrorRoll = false;
bool audioEnabled = true;
bool bluetoothEnabled = false;
bool batteryGaugeReady = false;
bool batteryLoggingActive = false;
bool batteryLogWifiEnabled = true;
bool batteryLogBluetoothEnabled = false;
bool batteryLogOledEnabled = true;
bool batteryLogSavedWifiEnabled = true;
bool batteryLogSavedBluetoothEnabled = false;
bool batteryLogSavedOledEnabled = true;
bool wifiEnabled = true;
bool blindsMode = false;
bool bootBlindsMode = false;
bool blindsOnline = false;
const char *blindsMotion = "Idle";
bool wifiReady = false;
bool otaReady = false;
bool wifiAttemptActive = false;
bool webServerReady = false;
bool webServerRoutesConfigured = false;
bool wifiPortalActive = false;
bool altitudeFilterInitialized = false;
bool bmpWarmupComplete = false;
bool altitudeZeroSaved = false;
bool varioRateInitialized = false;
bool liftAudioActive = false;
bool sinkAudioActive = false;
bool liftBeepOn = false;
bool toneTestActive = false;
bool buzzerLabActive = false;
bool editingMenuItem = false;
bool inMenuMode = false;
bool controlsLocked = false;
bool lockBeepEnabled = true;
uint32_t lockHoldMs = kDefaultLockHoldMs;
uint32_t lockSplashUntilMs = 0;
bool clock12h = false;
int16_t tzOffsetMinutes = 0;
bool pendingOledOn = true;
bool pendingWifiOn = true;
bool pendingBtOn = false;
uint32_t oledPeekUntilMs = 0;
bool pixelEnabled = false;
uint8_t activeWindow = 0;
uint8_t selectedMenuItem = kMenuDataLogging;
uint8_t selectedCategory = 0;
bool menuInCategory = false;
uint8_t categoryItemIndex = 0;
uint8_t selectedBatteryLogMenuItem = kBatteryLogMenuStop;

// Settings-menu categories. Every MenuItem lives in exactly one category.
// Power & Lock: OLED/WiFi/BT here are STAGED — nothing changes until "Lock now"
// applies them together, so the screen can't turn off before you finish choosing.
static const uint8_t kCatDisplay[] = {
    kMenuOled,
#ifndef VARIO_DISABLE_WIFI
    kMenuLockWifi,
#endif
#ifndef VARIO_DISABLE_BT
    kMenuLockBt,
#endif
    kMenuLock};
static const uint8_t kCatVarioAudio[] = {kMenuAudio, kMenuVolume, kMenuBuzzers,
                                         kMenuResponse, kMenuToneTest};
static const uint8_t kCatClock[] = {kMenuClockFormat, kMenuTzOffset};
static const uint8_t kCatAltitude[] = {kMenuSetAltitudeZero, kMenuClearAltitudeZero,
                                       kMenuAltitudeSource};
static const uint8_t kCatImu[] = {kMenuImuEnabled,   kMenuImuLevel,      kMenuImuClearLevel,
                                  kMenuImuSwapAxes,  kMenuImuMirrorPitch, kMenuImuMirrorRoll};
static const uint8_t kCatFlight[] = {kMenuFlight, kMenuFlightAutoStart, kMenuFlightAutoStop};
static const uint8_t kCatGps[] = {kMenuGpsEnabled,
#ifndef VARIO_DISABLE_BT
                                  kMenuBleGps,
#endif
                                  kMenuGpsLogRate};
static const uint8_t kCatLogging[] = {kMenuDataLogging, kMenuBatteryReadRate, kMenuBatteryLogging};
static const uint8_t kCatSystem[] = {
#ifndef VARIO_DISABLE_BT
    kMenuBluetooth,
#endif
#ifndef VARIO_DISABLE_WIFI
    kMenuWifiEnabled, kMenuWifiSetup, kMenuForgetWifi, kMenuBlinds, kMenuBootBlinds,
#endif
    kMenuSwitchFirmware, kMenuAbout};

const MenuCategory kMenuCategories[] = {
    {"Power & Lock", kCatDisplay, sizeof(kCatDisplay)},
    {"Vario & Audio", kCatVarioAudio, sizeof(kCatVarioAudio)},
    {"Clock", kCatClock, sizeof(kCatClock)},
    {"Altitude", kCatAltitude, sizeof(kCatAltitude)},
    {"IMU", kCatImu, sizeof(kCatImu)},
    {"Flight", kCatFlight, sizeof(kCatFlight)},
    {"GPS", kCatGps, sizeof(kCatGps)},
    {"Logging", kCatLogging, sizeof(kCatLogging)},
    {"System", kCatSystem, sizeof(kCatSystem)},
};
const uint8_t kMenuCategoryCount = sizeof(kMenuCategories) / sizeof(kMenuCategories[0]);
uint8_t logRateIndex = 2;
uint8_t batteryReadRateIndex = 2;
uint8_t buzzerVolumePercent = kDefaultBuzzerVolumePercent;
String btEarbudName = kDefaultEarbudName;
bool bleSendGps = true;
String bleDeviceName = kDefaultBleName;
uint8_t buzzerCount = 1;
float liftThresholdMps = kLiftThresholdMps;
uint16_t liftFreqBaseHz = kLiftFreqBaseHz;
uint16_t liftFreqSlopeHz = kLiftFreqIncrementHzPerMps;
uint8_t beepTempoPercent = 100;
bool twoToneLift = false;
float sinkThresholdMps = kSinkThresholdMps;
uint16_t sinkFreqBaseHz = kSinkFreqBaseHz;
bool twoToneSink = false;
uint8_t varioResponseIndex = 1;
uint8_t toneTestPatternIndex = 0;
uint8_t buzzerTestTargetIndex = 0;
uint8_t wifiNetworkCount = 0;
uint8_t wifiAttemptIndex = 0;
uint8_t pixelMode = kPixelModeColor;
uint8_t bmpAddress = 0;
uint32_t pixelColor = 0x00FF00;

uint32_t lastDisplayMs = 0;
uint32_t lastGpsLogMs = 0;
uint32_t batteryLogStartMs = 0;
uint32_t lastBatteryLogMs = 0;
uint32_t lastGpsDebugMs = 0;
uint32_t lastSensorReadMs = 0;
uint32_t lastBmpInitAttemptMs = 0;
uint32_t lastImuInitAttemptMs = 0;
uint32_t lastWifiAttemptMs = 0;
uint32_t wifiAttemptStartMs = 0;
uint32_t lastPixelUpdateMs = 0;
uint32_t lastBatteryReadMs = 0;
uint32_t bmpWarmupStartMs = 0;
uint32_t lastVarioRateUpdateMs = 0;
uint32_t liftPhaseStartMs = 0;
uint32_t currentToneHz = 0;
uint32_t toneTestStartMs = 0;
uint32_t lastBuzzerLabMs = 0;
uint8_t currentToneMask = 0;
uint16_t rainbowHue = 0;

float baroPressurePa = NAN;
uint16_t maxLogMb = 0;
uint64_t sdTotalBytes = 0;
uint64_t sdUsedBytes = 0;
float altitudeFt = 0.0F;
float smoothedAltitudeFt = 0.0F;
float previousVarioAltitudeFt = 0.0F;
float baselineSmoothedAltitudeFt = 0.0F;
float displayAltitudeFt = 0.0F;
float verticalSpeedMps = 0.0F;
float temperatureF = NAN;
float humidityPercent = NAN;
float imuPitchDeg = NAN;
float imuRollDeg = NAN;
float imuGForce = NAN;
float imuPitchOffsetDeg = 0.0F;
float imuRollOffsetDeg = 0.0F;
uint8_t oledWindowCount = kDefaultOledWindowCount;
bool flightActive = false;
uint32_t flightStartMs = 0;
uint32_t flightElapsedSec = 0;
float avgSpeedKmph = NAN;
uint8_t flightStartSpeedMph = 10;
uint8_t flightStartSecs = 5;
uint8_t flightStopSpeedMph = 10;
uint8_t flightStopSecs = 3;
bool flightAutoStart = true;
bool flightAutoStop = true;
float batteryVoltage = NAN;
float batteryPercent = NAN;
String connectedWifiSsid;
StoredWifiNetwork wifiNetworks[kMaxWifiNetworks];

float clampFloat(float value, float low, float high) {
  return min(max(value, low), high);
}

String floatOrDash(float value, uint8_t decimals, const char *suffix) {
  if (isnan(value)) {
    return String("--") + suffix;
  }
  return String(value, static_cast<unsigned int>(decimals)) + suffix;
}
