scottypres/Arduino-Paragliding-Varios/Sparkfun ESP32 WROOM Vario/Arduino Scripts/Sparkfun_Vario/settings.cpp

#include "settings.h"

#include "audio.h"
#include "gps_mod.h"
#include "imu.h"
#include "power.h"
#include "radio.h"
#include "timekeeping.h"
#include "version.h"
#include "web.h"
#include "wifi_net.h"

void loadSettings() {
  prefs.begin(kPrefsNamespace, false);
  dataLoggingEnabled = prefs.getBool(kPrefDataLogging, true);
  audioEnabled = prefs.getBool(kPrefAudio, true);
  buzzerVolumePercent = constrain(prefs.getUChar(kPrefVolume, kDefaultBuzzerVolumePercent),
                                  kMinBuzzerVolumePercent,
                                  kMaxBuzzerVolumePercent);
  buzzerCount = constrain(prefs.getUChar(kPrefBuzzerCount, buzzerCount),
                          static_cast<uint8_t>(1), kBuzzerCount);
  btEarbudName = prefs.getString(kPrefEarbudName, kDefaultEarbudName);
  bleSendGps = prefs.getBool(kPrefBleGps, true);
  bleDeviceName = prefs.getString(kPrefBleName, kDefaultBleName);
  if (bleDeviceName.length() == 0) {
    bleDeviceName = kDefaultBleName;
  }
  liftThresholdMps = clampFloat(prefs.getFloat(kPrefLiftOnMps, liftThresholdMps), 0.05F, 1.0F);
  liftFreqBaseHz = constrain(prefs.getUShort(kPrefLiftHz, liftFreqBaseHz),
                             static_cast<uint16_t>(300), static_cast<uint16_t>(3000));
  liftFreqSlopeHz = constrain(prefs.getUShort(kPrefLiftSlopeHz, liftFreqSlopeHz),
                              static_cast<uint16_t>(0), static_cast<uint16_t>(400));
  beepTempoPercent = constrain(prefs.getUChar(kPrefBeepTempo, beepTempoPercent),
                               static_cast<uint8_t>(50), static_cast<uint8_t>(200));
  twoToneLift = prefs.getBool(kPrefTwoToneLift, twoToneLift);
  sinkThresholdMps = clampFloat(prefs.getFloat(kPrefSinkOnMps, sinkThresholdMps), -5.0F, -0.5F);
  sinkFreqBaseHz = constrain(prefs.getUShort(kPrefSinkHz, sinkFreqBaseHz),
                             static_cast<uint16_t>(150), static_cast<uint16_t>(800));
  twoToneSink = prefs.getBool(kPrefTwoToneSink, twoToneSink);
  varioResponseIndex = prefs.getUChar(kPrefResponse, varioResponseIndex);
  if (varioResponseIndex >= kVarioResponseCount) {
    varioResponseIndex = 1;
  }
  maxLogMb = prefs.getUShort(kPrefMaxLogMb, 0);
  logRateIndex = prefs.getUChar(kPrefLogRate, logRateIndex);
  if (logRateIndex >= kLogRateCount) {
    logRateIndex = 2;
  }
  batteryReadRateIndex = prefs.getUChar(kPrefBatteryReadRate, batteryReadRateIndex);
  if (batteryReadRateIndex >= kBatteryReadRateCount) {
    batteryReadRateIndex = 2;
  }
  controlsLocked = prefs.getBool(kPrefLocked, false);
  lockBeepEnabled = prefs.getBool(kPrefLockBeep, true);
  lockHoldMs = constrain(prefs.getUInt(kPrefLockHoldMs, kDefaultLockHoldMs),
                         kMinLockHoldMs, kMaxLockHoldMs);
  clock12h = prefs.getBool(kPrefClock12h, false);
  tzOffsetMinutes = constrain(prefs.getShort(kPrefTzMinutes, 0),
                              static_cast<int16_t>(-720), static_cast<int16_t>(840));
  gpsEnabled = prefs.getBool(kPrefGpsEnabled, true);
  useGpsAltitude = prefs.getBool(kPrefAltitudeSource, false);
  imuEnabled = prefs.getBool(kPrefImuEnabled, true);
  imuLevelSaved = prefs.getBool(kPrefImuHasLevel, false);
  imuPitchOffsetDeg = prefs.getFloat(kPrefImuPitchZero, 0.0F);
  imuRollOffsetDeg = prefs.getFloat(kPrefImuRollZero, 0.0F);
  imuSwapAxes = prefs.getBool(kPrefImuSwapAxes, true);
  imuMirrorPitch = prefs.getBool(kPrefImuMirrorPitch, false);
  imuMirrorRoll = prefs.getBool(kPrefImuMirrorRoll, false);
  flightStartSpeedMph = prefs.getUChar(kPrefFlightStartMph, 10);
  flightStartSecs = prefs.getUChar(kPrefFlightStartSecs, 5);
  flightStopSpeedMph = prefs.getUChar(kPrefFlightStopMph, 10);
  flightStopSecs = prefs.getUChar(kPrefFlightStopSecs, 3);
  flightAutoStart = prefs.getBool(kPrefFlightAutoStart, true);
  flightAutoStop = prefs.getBool(kPrefFlightAutoStop, true);
  const bool savedBluetoothEnabled = prefs.getBool(kPrefBluetooth, false);
  altitudeZeroSaved = prefs.getBool(kPrefHasAltitudeZero, false);
  baselineSmoothedAltitudeFt = prefs.getFloat(kPrefAltitudeZeroFt, 0.0F);
  pixelEnabled = prefs.getBool(kPrefPixelEnabled, false);
  pixelMode = prefs.getUChar(kPrefPixelMode, kPixelModeColor);
  if (pixelMode >= kPixelModeCount) {
    pixelMode = kPixelModeColor;
  }
  pixelColor = prefs.getUInt(kPrefPixelColor, pixelColor) & 0xFFFFFF;
  wifiEnabled = prefs.getBool(kPrefWifiEnabled, true);
#ifndef VARIO_DISABLE_WIFI
  bootBlindsMode = prefs.getBool(kPrefBootBlinds, false);
  blindsMode = bootBlindsMode;
  if (blindsMode) {
    wifiEnabled = true;  // blinds control needs the network even if WiFi was left off
  }
#endif
  loadWifiNetworks();
  setBluetoothEnabled(savedBluetoothEnabled, false);
}

String buildSettingsJson() {
  JsonDocument doc;
  doc["fw_version"] = VARIO_FW_VERSION;
  doc["fw_radio"] = VARIO_FW_RADIO;
  doc["fw_build"] = VARIO_FW_BUILD;
  doc["data_logging"] = dataLoggingEnabled;
  doc["audio"] = audioEnabled;
  doc["volume"] = buzzerVolumePercent;
  doc["volume_min"] = kMinBuzzerVolumePercent;
  doc["volume_max"] = kMaxBuzzerVolumePercent;
  doc["buzzer_count"] = buzzerCount;
  doc["bt_earbud_name"] = btEarbudName;
  doc["ble_send_gps"] = bleSendGps;
  doc["ble_name"] = bleDeviceName;
  doc["lift_on_mps"] = liftThresholdMps;
  doc["lift_hz"] = liftFreqBaseHz;
  doc["lift_slope_hz"] = liftFreqSlopeHz;
  doc["beep_tempo"] = beepTempoPercent;
  doc["two_tone_lift"] = twoToneLift;
  doc["sink_on_mps"] = sinkThresholdMps;
  doc["sink_hz"] = sinkFreqBaseHz;
  doc["two_tone_sink"] = twoToneSink;
  doc["response"] = varioResponseIndex;
  doc["response_label"] = kVarioResponseLabels[varioResponseIndex];
  doc["max_log_mb"] = maxLogMb;
  doc["log_rate_index"] = logRateIndex;
  doc["log_rate_label"] = kLogRateLabels[logRateIndex];
  doc["battery_read_rate_index"] = batteryReadRateIndex;
  doc["battery_read_rate_label"] = kBatteryReadRateLabels[batteryReadRateIndex];
  doc["battery_gauge_ready"] = batteryGaugeReady;
  doc["gps_enabled"] = gpsEnabled;
  doc["use_gps_altitude"] = useGpsAltitude;
  doc["imu_enabled"] = imuEnabled;
  doc["imu_ready"] = imuReady;
  doc["imu_level_saved"] = imuLevelSaved;
  doc["imu_swap_axes"] = imuSwapAxes;
  doc["imu_mirror_pitch"] = imuMirrorPitch;
  doc["imu_mirror_roll"] = imuMirrorRoll;
  doc["flight_start_mph"] = flightStartSpeedMph;
  doc["flight_start_secs"] = flightStartSecs;
  doc["flight_stop_mph"] = flightStopSpeedMph;
  doc["flight_stop_secs"] = flightStopSecs;
  doc["flight_auto_start"] = flightAutoStart;
  doc["flight_auto_stop"] = flightAutoStop;
  doc["bluetooth_enabled"] = bluetoothEnabled;
  doc["pixel_enabled"] = pixelEnabled;
  doc["pixel_mode"] = pixelModeName(pixelMode);
  doc["pixel_color"] = colorToHex(pixelColor);
  doc["altitude_zero_saved"] = altitudeZeroSaved;
  doc["display_altitude_ft"] = displayAltitudeFt;
  doc["locked"] = controlsLocked;
  doc["lock_hold_ms"] = lockHoldMs;
  doc["lock_beep"] = lockBeepEnabled;
  doc["clock_12h"] = clock12h;
  doc["tz_offset_min"] = tzOffsetMinutes;

  JsonArray resp = doc["response_options"].to<JsonArray>();
  for (uint8_t i = 0; i < kVarioResponseCount; i++) {
    resp.add(kVarioResponseLabels[i]);
  }
  JsonArray rates = doc["log_rate_options"].to<JsonArray>();
  for (uint8_t i = 0; i < kLogRateCount; i++) {
    rates.add(kLogRateLabels[i]);
  }
  JsonArray batteryRates = doc["battery_read_rate_options"].to<JsonArray>();
  for (uint8_t i = 0; i < kBatteryReadRateCount; i++) {
    batteryRates.add(kBatteryReadRateLabels[i]);
  }
  const char *pixelModes[] = {"color", "rainbow", "temp", "humidity",
                              "altitude", "satellites", "battery"};
  JsonArray pixModes = doc["pixel_mode_options"].to<JsonArray>();
  for (const char *m : pixelModes) {
    pixModes.add(m);
  }

  String out;
  serializeJson(doc, out);
  return out;
}

void applySettingsJson(JsonObjectConst obj) {
  if (obj["data_logging"].is<bool>()) {
    dataLoggingEnabled = obj["data_logging"].as<bool>();
    prefs.putBool(kPrefDataLogging, dataLoggingEnabled);
  }
  if (obj["audio"].is<bool>()) {
    audioEnabled = obj["audio"].as<bool>();
    prefs.putBool(kPrefAudio, audioEnabled);
    if (!audioEnabled) {
      setTone(0);
    }
  }
  if (obj["volume"].is<int>()) {
    buzzerVolumePercent = constrain(obj["volume"].as<int>(),
                                    static_cast<int>(kMinBuzzerVolumePercent),
                                    static_cast<int>(kMaxBuzzerVolumePercent));
    prefs.putUChar(kPrefVolume, buzzerVolumePercent);
  }
  if (obj["buzzer_count"].is<int>()) {
    buzzerCount = constrain(obj["buzzer_count"].as<int>(), 1, static_cast<int>(kBuzzerCount));
    prefs.putUChar(kPrefBuzzerCount, buzzerCount);
  }
  if (obj["bt_earbud_name"].is<const char *>()) {
    String name = obj["bt_earbud_name"].as<const char *>();
    name.trim();
    if (name.length() == 0) {
      name = kDefaultEarbudName;  // blank resets to the default
    } else if (name.length() > kMaxEarbudNameLen) {
      name = name.substring(0, kMaxEarbudNameLen);
    }
    btEarbudName = name;
    prefs.putString(kPrefEarbudName, btEarbudName);
  }
  if (obj["ble_send_gps"].is<bool>()) {
    bleSendGps = obj["ble_send_gps"].as<bool>();
    prefs.putBool(kPrefBleGps, bleSendGps);
  }
  if (obj["ble_name"].is<const char *>()) {
    String name = obj["ble_name"].as<const char *>();
    name.trim();
    if (name.length() == 0) {
      name = kDefaultBleName;
    } else if (name.length() > 29) {
      name = name.substring(0, 29);  // BLE adv name budget
    }
    bleDeviceName = name;
    prefs.putString(kPrefBleName, bleDeviceName);  // applied at next boot
  }
  if (obj["lift_on_mps"].is<float>()) {
    liftThresholdMps = clampFloat(obj["lift_on_mps"].as<float>(), 0.05F, 1.0F);
    prefs.putFloat(kPrefLiftOnMps, liftThresholdMps);
  }
  if (obj["lift_hz"].is<int>()) {
    liftFreqBaseHz = constrain(obj["lift_hz"].as<int>(), 300, 3000);
    prefs.putUShort(kPrefLiftHz, liftFreqBaseHz);
  }
  if (obj["lift_slope_hz"].is<int>()) {
    liftFreqSlopeHz = constrain(obj["lift_slope_hz"].as<int>(), 0, 400);
    prefs.putUShort(kPrefLiftSlopeHz, liftFreqSlopeHz);
  }
  if (obj["beep_tempo"].is<int>()) {
    beepTempoPercent = constrain(obj["beep_tempo"].as<int>(), 50, 200);
    prefs.putUChar(kPrefBeepTempo, beepTempoPercent);
  }
  if (obj["two_tone_lift"].is<bool>()) {
    twoToneLift = obj["two_tone_lift"].as<bool>();
    prefs.putBool(kPrefTwoToneLift, twoToneLift);
  }
  if (obj["sink_on_mps"].is<float>()) {
    sinkThresholdMps = clampFloat(obj["sink_on_mps"].as<float>(), -5.0F, -0.5F);
    prefs.putFloat(kPrefSinkOnMps, sinkThresholdMps);
  }
  if (obj["sink_hz"].is<int>()) {
    sinkFreqBaseHz = constrain(obj["sink_hz"].as<int>(), 150, 800);
    prefs.putUShort(kPrefSinkHz, sinkFreqBaseHz);
  }
  if (obj["two_tone_sink"].is<bool>()) {
    twoToneSink = obj["two_tone_sink"].as<bool>();
    prefs.putBool(kPrefTwoToneSink, twoToneSink);
  }
  if (obj["response"].is<int>()) {
    const int r = obj["response"].as<int>();
    if (r >= 0 && r < kVarioResponseCount) {
      varioResponseIndex = static_cast<uint8_t>(r);
      prefs.putUChar(kPrefResponse, varioResponseIndex);
    }
  }
  if (obj["max_log_mb"].is<int>()) {
    maxLogMb = static_cast<uint16_t>(constrain(obj["max_log_mb"].as<int>(), 0, 30000));
    prefs.putUShort(kPrefMaxLogMb, maxLogMb);
  }
  if (obj["log_rate_index"].is<int>()) {
    const int r = obj["log_rate_index"].as<int>();
    if (r >= 0 && r < kLogRateCount) {
      logRateIndex = static_cast<uint8_t>(r);
      prefs.putUChar(kPrefLogRate, logRateIndex);
    }
  }
  if (obj["battery_read_rate_index"].is<int>()) {
    const int r = obj["battery_read_rate_index"].as<int>();
    if (r >= 0 && r < kBatteryReadRateCount) {
      batteryReadRateIndex = static_cast<uint8_t>(r);
      prefs.putUChar(kPrefBatteryReadRate, batteryReadRateIndex);
    }
  }
  if (obj["lock_hold_ms"].is<int>()) {
    lockHoldMs = constrain(static_cast<uint32_t>(obj["lock_hold_ms"].as<int>()),
                           kMinLockHoldMs, kMaxLockHoldMs);
    prefs.putUInt(kPrefLockHoldMs, lockHoldMs);
  }
  if (obj["lock_beep"].is<bool>()) {
    lockBeepEnabled = obj["lock_beep"].as<bool>();
    prefs.putBool(kPrefLockBeep, lockBeepEnabled);
  }
  if (obj["clock_12h"].is<bool>()) {
    clock12h = obj["clock_12h"].as<bool>();
    prefs.putBool(kPrefClock12h, clock12h);
  }
  if (obj["tz_offset_min"].is<int>()) {
    tzOffsetMinutes = constrain(obj["tz_offset_min"].as<int>(), -720, 840);
    prefs.putShort(kPrefTzMinutes, tzOffsetMinutes);
  }
  if (obj["gps_enabled"].is<bool>()) {
    setGpsEnabled(obj["gps_enabled"].as<bool>());
  }
  if (obj["imu_enabled"].is<bool>()) {
    setImuEnabled(obj["imu_enabled"].as<bool>());
  }
  if (obj["imu_swap_axes"].is<bool>()) {
    imuSwapAxes = obj["imu_swap_axes"].as<bool>();
    prefs.putBool(kPrefImuSwapAxes, imuSwapAxes);
  }
  if (obj["imu_mirror_pitch"].is<bool>()) {
    imuMirrorPitch = obj["imu_mirror_pitch"].as<bool>();
    prefs.putBool(kPrefImuMirrorPitch, imuMirrorPitch);
  }
  if (obj["imu_mirror_roll"].is<bool>()) {
    imuMirrorRoll = obj["imu_mirror_roll"].as<bool>();
    prefs.putBool(kPrefImuMirrorRoll, imuMirrorRoll);
  }
  if (obj["flight_start_mph"].is<int>()) {
    flightStartSpeedMph = constrain(obj["flight_start_mph"].as<int>(), 0, 200);
    prefs.putUChar(kPrefFlightStartMph, flightStartSpeedMph);
  }
  if (obj["flight_start_secs"].is<int>()) {
    flightStartSecs = constrain(obj["flight_start_secs"].as<int>(), 0, 120);
    prefs.putUChar(kPrefFlightStartSecs, flightStartSecs);
  }
  if (obj["flight_stop_mph"].is<int>()) {
    flightStopSpeedMph = constrain(obj["flight_stop_mph"].as<int>(), 0, 200);
    prefs.putUChar(kPrefFlightStopMph, flightStopSpeedMph);
  }
  if (obj["flight_stop_secs"].is<int>()) {
    flightStopSecs = constrain(obj["flight_stop_secs"].as<int>(), 0, 120);
    prefs.putUChar(kPrefFlightStopSecs, flightStopSecs);
  }
  if (obj["flight_auto_start"].is<bool>()) {
    flightAutoStart = obj["flight_auto_start"].as<bool>();
    prefs.putBool(kPrefFlightAutoStart, flightAutoStart);
  }
  if (obj["flight_auto_stop"].is<bool>()) {
    flightAutoStop = obj["flight_auto_stop"].as<bool>();
    prefs.putBool(kPrefFlightAutoStop, flightAutoStop);
  }
  if (obj["use_gps_altitude"].is<bool>()) {
    useGpsAltitude = obj["use_gps_altitude"].as<bool>();
    prefs.putBool(kPrefAltitudeSource, useGpsAltitude);
  }
  if (obj["bluetooth_enabled"].is<bool>()) {
    setBluetoothEnabled(obj["bluetooth_enabled"].as<bool>(), true);
  }
  if (obj["pixel_enabled"].is<bool>()) {
    pixelEnabled = obj["pixel_enabled"].as<bool>();
  }
  if (obj["pixel_mode"].is<const char *>()) {
    pixelMode = pixelModeFromName(obj["pixel_mode"].as<const char *>());
  }
  if (obj["pixel_color"].is<const char *>()) {
    pixelColor = parseHtmlColor(obj["pixel_color"].as<const char *>(), pixelColor);
  }
  savePixelSettings();
  servicePixel();
}
