scottypres/Arduino-Paragliding-Varios/Sparkfun ESP32 WROOM Vario/Arduino Scripts/Sparkfun_Vario/wifi_net.cpp

#include "wifi_net.h"

#ifndef VARIO_DISABLE_WIFI

#include "display.h"
#include "timekeeping.h"
#include "web.h"

String wifiKey(const char *prefix, uint8_t index) {
  return String(prefix) + String(index);
}

void saveWifiNetworks() {
  wifiNetworkCount = min(wifiNetworkCount, kMaxWifiNetworks);
  prefs.putUChar(kPrefWifiCount, wifiNetworkCount);
  prefs.putBool(kPrefWifiInitialized, true);
  for (uint8_t index = 0; index < kMaxWifiNetworks; index++) {
    if (index < wifiNetworkCount) {
      prefs.putString(wifiKey("wifiS", index).c_str(), wifiNetworks[index].ssid);
      prefs.putString(wifiKey("wifiP", index).c_str(), wifiNetworks[index].password);
    } else {
      prefs.remove(wifiKey("wifiS", index).c_str());
      prefs.remove(wifiKey("wifiP", index).c_str());
    }
  }
}

bool addWifiNetwork(const String &ssid, const String &password) {
  if (ssid.length() == 0) {
    return false;
  }

  for (uint8_t index = 0; index < wifiNetworkCount; index++) {
    if (wifiNetworks[index].ssid == ssid) {
      wifiNetworks[index].password = password;
      saveWifiNetworks();
      return true;
    }
  }

  if (wifiNetworkCount >= kMaxWifiNetworks) {
    return false;
  }

  wifiNetworks[wifiNetworkCount].ssid = ssid;
  wifiNetworks[wifiNetworkCount].password = password;
  wifiNetworkCount++;
  saveWifiNetworks();
  return true;
}

bool removeWifiNetwork(uint8_t removeIndex) {
  if (removeIndex >= wifiNetworkCount) {
    return false;
  }

  for (uint8_t index = removeIndex; index + 1 < wifiNetworkCount; index++) {
    wifiNetworks[index] = wifiNetworks[index + 1];
  }
  wifiNetworkCount--;
  saveWifiNetworks();
  if (wifiAttemptIndex >= wifiNetworkCount) {
    wifiAttemptIndex = 0;
  }
  return true;
}

void clearWifiNetworks() {
  wifiNetworkCount = 0;
  wifiAttemptIndex = 0;
  connectedWifiSsid = "";
  saveWifiNetworks();
  WiFi.disconnect(false, false);
  wifiReady = false;
  wifiAttemptActive = false;
}

void loadWifiNetworks() {
  wifiNetworkCount = 0;

  if (!prefs.getBool(kPrefWifiInitialized, false)) {
    saveWifiNetworks();
    return;
  }

  const uint8_t storedCount = min(prefs.getUChar(kPrefWifiCount, 0), kMaxWifiNetworks);
  for (uint8_t index = 0; index < storedCount; index++) {
    const String ssid = prefs.getString(wifiKey("wifiS", index).c_str(), "");
    if (ssid.length() == 0) {
      continue;
    }
    wifiNetworks[wifiNetworkCount].ssid = ssid;
    wifiNetworks[wifiNetworkCount].password = prefs.getString(wifiKey("wifiP", index).c_str(), "");
    wifiNetworkCount++;
  }
}

void stopWifiPortal() {
  if (!wifiPortalActive) {
    return;
  }
  dnsServer.stop();
  wifiPortalActive = false;
}

// Bring up our own open SoftAP and serve the full vario web app over it, with
// a wildcard DNS server so a phone's captive-portal check pops the same UI you
// get over a real network. WiFi credentials are added from that web app
// (WiFi section), so no separate WiFiManager config portal is needed.
void startWifiPortal() {
  if (wifiPortalActive) {
    return;
  }

  if (!wifiEnabled) {
    wifiEnabled = true;
    prefs.putBool(kPrefWifiEnabled, true);
  }

  wifiAttemptActive = false;
  wifiReady = false;
  otaReady = false;
  connectedWifiSsid = "";

  WiFi.mode(WIFI_AP);
  WiFi.softAP(kWifiPortalSsid, kWifiPortalPassword);
  delay(100);  // let the AP settle before we read its IP
  dnsServer.setErrorReplyCode(DNSReplyCode::NoError);
  dnsServer.start(53, "*", WiFi.softAPIP());  // send every lookup to us
  wifiPortalActive = true;

  startWebServer();  // same server/routes as the station-mode web app

  Serial.print("AP portal up: ");
  Serial.print(kWifiPortalSsid);
  Serial.print(" -> http://");
  Serial.println(WiFi.softAPIP());
}

void forgetWifiAndStartPortal() {
  clearWifiNetworks();
  startWifiPortal();
}

void startWifiAttempt(uint8_t index) {
  if (wifiNetworkCount == 0 || index >= wifiNetworkCount) {
    wifiAttemptActive = false;
    startWifiPortal();
    return;
  }

  stopWifiPortal();  // drop the AP/DNS before switching to station mode
  WiFi.mode(WIFI_STA);
  WiFi.disconnect(false, false);
  delay(1);
  connectedWifiSsid = "";
  wifiAttemptIndex = index;
  wifiAttemptStartMs = millis();
  wifiAttemptActive = true;

  Serial.print("Connecting WiFi: ");
  Serial.println(wifiNetworks[index].ssid);
  WiFi.begin(wifiNetworks[index].ssid.c_str(), wifiNetworks[index].password.c_str());
}

void initWifi() {
  if (!wifiEnabled) {
    WiFi.mode(WIFI_OFF);
    return;
  }

  WiFi.mode(WIFI_STA);
  WiFi.setAutoReconnect(false);
  wifiReady = false;
  otaReady = false;
  wifiAttemptActive = false;
  wifiAttemptIndex = 0;
  lastWifiAttemptMs = 0;

  if (wifiNetworkCount == 0) {
    Serial.println("No saved WiFi networks; starting setup portal");
    startWifiPortal();
    return;
  }

  startWifiAttempt(0);
}

void setWifiEnabled(bool enabled, bool persist) {
  if (enabled == wifiEnabled) {
    if (persist) {
      prefs.putBool(kPrefWifiEnabled, wifiEnabled);
    }
    return;
  }

  wifiEnabled = enabled;
  if (persist) {
    prefs.putBool(kPrefWifiEnabled, wifiEnabled);
  }

  if (enabled) {
    WiFi.mode(WIFI_STA);
    if (wifiNetworkCount == 0) {
      startWifiPortal();
    } else if (!wifiReady && !wifiAttemptActive) {
      startWifiAttempt(wifiAttemptIndex);
    }
    return;
  }

  stopWifiPortal();
  stopWebServer();
  WiFi.disconnect(false, false);
  WiFi.mode(WIFI_OFF);
  wifiReady = false;
  otaReady = false;
  wifiAttemptActive = false;
  connectedWifiSsid = "";
}

void setBatteryLogWifiEnabled(bool enabled) {
  batteryLogWifiEnabled = enabled;
  if (enabled) {
    WiFi.mode(WIFI_STA);
    if (wifiNetworkCount == 0) {
      startWifiPortal();
    } else if (!wifiReady && !wifiAttemptActive) {
      startWifiAttempt(wifiAttemptIndex);
    }
    return;
  }

  stopWifiPortal();
  stopWebServer();
  WiFi.disconnect(false, false);
  WiFi.mode(WIFI_OFF);
  wifiReady = false;
  otaReady = false;
  wifiAttemptActive = false;
  connectedWifiSsid = "";
}

String wifiStatusText() {
  if (!wifiEnabled) {
    return "Off";
  }
  if (wifiReady) {
    return String("On ") + connectedWifiSsid;
  }
  if (wifiPortalActive) {
    return String("AP ") + kWifiPortalSsid;
  }
  if (batteryLoggingActive && !batteryLogWifiEnabled) {
    return "Off";
  }
  if (wifiAttemptActive && wifiAttemptIndex < wifiNetworkCount) {
    return String("Connecting ") + wifiNetworks[wifiAttemptIndex].ssid;
  }
  return "Idle";
}

void serviceWifi() {
  const uint32_t nowMs = millis();

  if (!wifiEnabled) {
    if (WiFi.getMode() != WIFI_OFF) {
      WiFi.mode(WIFI_OFF);
    }
    return;
  }

  if (batteryLoggingActive && !batteryLogWifiEnabled) {
    if (WiFi.getMode() != WIFI_OFF) {
      setBatteryLogWifiEnabled(false);
    }
    return;
  }

  if (wifiPortalActive) {
    dnsServer.processNextRequest();
  }

  if (WiFi.status() == WL_CONNECTED) {
    if (!wifiReady) {
      if (wifiPortalActive) {
        stopWifiPortal();
      }
      wifiReady = true;
      wifiAttemptActive = false;
      connectedWifiSsid = WiFi.SSID();
      Serial.print("WiFi connected: ");
      Serial.print(connectedWifiSsid);
      Serial.print(" ");
      Serial.println(WiFi.localIP());
      onWifiConnectedTime();
      initOta();
      startWebServer();
    }
    return;
  }

  if (wifiReady) {
    wifiReady = false;
    otaReady = false;
    connectedWifiSsid = "";
    lastWifiAttemptMs = nowMs;
    Serial.println("WiFi disconnected");
  }

  if (wifiNetworkCount == 0) {
    if (!wifiPortalActive && nowMs - lastWifiAttemptMs >= kWifiRetryDelayMs) {
      startWifiPortal();
      lastWifiAttemptMs = nowMs;
    }
    return;
  }

  if (wifiAttemptActive) {
    if (nowMs - wifiAttemptStartMs < kWifiConnectTimeoutMs) {
      return;
    }
    Serial.print("WiFi timeout: ");
    Serial.println(wifiNetworks[wifiAttemptIndex].ssid);
    WiFi.disconnect(false, false);
    wifiAttemptActive = false;
    const uint8_t nextIndex = static_cast<uint8_t>((wifiAttemptIndex + 1) % wifiNetworkCount);
    if (nextIndex == 0) {
      startWifiPortal();
    }
    wifiAttemptIndex = nextIndex;
    lastWifiAttemptMs = nowMs;
    return;
  }

  if (!wifiPortalActive && nowMs - lastWifiAttemptMs >= kWifiRetryDelayMs) {
    startWifiAttempt(wifiAttemptIndex);
  }
}

// ---- SmartBlinds remote (POST /up /down /stop on the blinds ESP32) ----
constexpr uint32_t kBlindsPingMs = 3000;
constexpr uint32_t kBlindsHttpTimeoutMs = 1500;
static uint32_t lastBlindsPingMs = 0;

void enterBlindsMode() {
  blindsMode = true;
  inMenuMode = false;
  blindsMotion = "Idle";
  lastBlindsPingMs = 0;
  if (!wifiEnabled) {
    setWifiEnabled(true, false);
  }
}

void serviceBlinds() {
  if (!blindsMode || millis() - lastBlindsPingMs < kBlindsPingMs) {
    return;
  }
  lastBlindsPingMs = millis();
  bool online = false;
  if (wifiEnabled && WiFi.status() == WL_CONNECTED) {
    WiFiClient probe;
    online = probe.connect(kBlindsHost, 80, 300);
    probe.stop();
  }
  if (online != blindsOnline) {
    blindsOnline = online;
    updateDisplay(true);
  }
}

void sendBlindsCommand(const char *path, const char *motion) {
  if (!wifiEnabled || WiFi.status() != WL_CONNECTED) {
    blindsMotion = "No WiFi";
    updateDisplay(true);
    return;
  }
  // ponytail: raw POST over WiFiClient; HTTPClient drags in TLS and the WROOM's IRAM is full
  WiFiClient client;
  bool ok = false;
  if (client.connect(kBlindsHost, 80, kBlindsHttpTimeoutMs)) {
    client.print(String("POST ") + path + " HTTP/1.0\r\nHost: " + kBlindsHost +
                 "\r\nContent-Length: 0\r\n\r\n");
    client.setTimeout(kBlindsHttpTimeoutMs);
    ok = client.readStringUntil('\n').indexOf(" 204") > 0;
  }
  client.stop();
  blindsOnline = ok;
  blindsMotion = ok ? motion : "Send failed";
  lastBlindsPingMs = millis();
  updateDisplay(true);
}

#else  // VARIO_DISABLE_WIFI — radio-free stubs so the BT firmware links without WiFi.

void enterBlindsMode() {}
void serviceBlinds() {}
void sendBlindsCommand(const char *, const char *) {}

void initWifi() {}
void serviceWifi() {}
void loadWifiNetworks() {}
void startWifiPortal() {}
void forgetWifiAndStartPortal() {}
void setWifiEnabled(bool enabled, bool persist) { wifiEnabled = false; }
void setBatteryLogWifiEnabled(bool enabled) { batteryLogWifiEnabled = enabled; }
String wifiStatusText() { return "Off"; }

#endif
