scottypres/Arduino-Paragliding-Varios/Sparkfun ESP32 WROOM Vario/Arduino Scripts/Sparkfun_Vario/audio.cpp

#include "audio.h"

void setBuzzersLow() {
  for (uint8_t pin : kBuzzerPins) {
    digitalWrite(pin, LOW);
  }
}

uint8_t activeBuzzerCount() {
  return constrain(buzzerCount, static_cast<uint8_t>(1), kBuzzerCount);
}

uint8_t activeBuzzerMask() {
  uint8_t mask = 0;
  const uint8_t count = activeBuzzerCount();
  for (uint8_t index = 0; index < kBuzzerCount; index++) {
    if (index < count) {
      mask |= (1U << index);
    }
  }
  return mask;
}

uint32_t clampFrequency(uint32_t value) {
  return min(max(value, kMinToneHz), kMaxToneHz);
}

uint32_t quantizeFrequency(uint32_t value) {
  value = clampFrequency(value);
  return ((value + kToneQuantizeHz / 2) / kToneQuantizeHz) * kToneQuantizeHz;
}

uint8_t buzzerDuty() {
  const uint8_t volume = constrain(buzzerVolumePercent,
                                   kMinBuzzerVolumePercent,
                                   kMaxBuzzerVolumePercent);
  uint16_t duty = static_cast<uint16_t>(volume) * 255U / 100U;
  return static_cast<uint8_t>(constrain(duty, 1U, 255U));
}

void setToneMask(uint32_t frequencyHz, uint8_t buzzerMask, bool honorAudioSetting) {
  if (honorAudioSetting && !audioEnabled) {
    frequencyHz = 0;
  }

  frequencyHz = frequencyHz > 0 ? quantizeFrequency(frequencyHz) : 0;
  if (frequencyHz == 0) {
    buzzerMask = 0;
  }

  if (frequencyHz == currentToneHz && buzzerMask == currentToneMask) {
    return;
  }

  for (uint8_t index = 0; index < kBuzzerCount; index++) {
    const bool active = frequencyHz > 0 && (buzzerMask & (1U << index));
    ledcWriteTone(kBuzzerPins[index], active ? frequencyHz : 0);
    ledcWrite(kBuzzerPins[index], active ? buzzerDuty() : 0);
    if (!active) {
      digitalWrite(kBuzzerPins[index], LOW);
    }
  }
  currentToneHz = frequencyHz;
  currentToneMask = buzzerMask;
}

void setTone(uint32_t frequencyHz) {
  setToneMask(frequencyHz, activeBuzzerMask());
}

void startBuzzers() {
  // Each buzzer needs its OWN LEDC timer for independent chord voices. Auto
  // ledcAttach() hands out channels 0,1,2 -> timers 0,0,1, so pins 13 & 26
  // would share timer 0 and be locked to one frequency. Attach to channels
  // 0,2,4 (even -> distinct timers 0,1,2) to give all three real voices.
  for (uint8_t index = 0; index < kBuzzerCount; index++) {
    const uint8_t pin = kBuzzerPins[index];
    pinMode(pin, OUTPUT);
    digitalWrite(pin, LOW);
    if (!ledcAttachChannel(pin, kLiftFreqBaseHz, kBuzzerResolutionBits, index * 2)) {
      Serial.print("Buzzer PWM setup failed on pin ");
      Serial.println(pin);
    }
  }
}

void startToneTest() {
  toneTestStartMs = millis();
  toneTestActive = true;
  liftAudioActive = false;
  sinkAudioActive = false;
  liftBeepOn = false;
  setToneMask(0, 0, false);
}

uint8_t buzzerTestMask() {
  if (buzzerTestTargetIndex < kBuzzerCount) {
    return 1U << buzzerTestTargetIndex;
  }
  return (1U << kBuzzerCount) - 1U;
}

bool updateToneTest() {
  if (!toneTestActive) {
    return false;
  }

  const uint32_t elapsedMs = millis() - toneTestStartMs;
  if (elapsedMs >= kBuzzerTestDurationMs) {
    toneTestActive = false;
    setToneMask(0, 0, false);
    return false;
  }

  setToneMask(kBuzzerTestToneHz, buzzerTestMask(), false);
  return true;
}

// ---- jingles (3-buzzer chords / melodies, on-demand) ----

struct JingleNote {
  uint16_t f0;
  uint16_t f1;
  uint16_t f2;
  uint16_t ms;
};

// Note freqs (Hz): C5 523 D5 587 E5 659 F5 698 G5 784 A5 880 B5 988
//                  C6 1047 D6 1175 E6 1319 G6 1568
// Chime: three rising major triads resolving up an octave (all 3 buzzers).
static const JingleNote kChimeNotes[] = {
    {523, 659, 784, 140}, {659, 784, 988, 140}, {784, 988, 1175, 180},
    {1047, 1319, 1568, 480}, {0, 0, 0, 60}};
// Arp: voices enter one at a time, then spread into a wide chord.
static const JingleNote kArpNotes[] = {
    {523, 0, 0, 90}, {523, 659, 0, 90}, {523, 659, 784, 90},
    {1047, 659, 784, 90}, {1047, 784, 988, 90}, {1047, 1319, 784, 400},
    {0, 0, 0, 40}};
static const JingleNote kChordNotes[] = {
    {523, 659, 784, 280}, {587, 740, 880, 280}, {659, 831, 988, 280},
    {523, 659, 1047, 520}, {0, 0, 0, 40}};

struct Jingle {
  const JingleNote *notes;
  uint8_t len;
};
static const Jingle kJingles[] = {
    {kChimeNotes, sizeof(kChimeNotes) / sizeof(kChimeNotes[0])},
    {kArpNotes, sizeof(kArpNotes) / sizeof(kArpNotes[0])},
    {kChordNotes, sizeof(kChordNotes) / sizeof(kChordNotes[0])}};
static const uint8_t kJingleCount = sizeof(kJingles) / sizeof(kJingles[0]);

static bool jinglePlaying = false;
static uint8_t jingleIdx = 0;
static uint8_t jingleNote = 0;
static uint32_t jingleNoteStartMs = 0;

void setChord(uint32_t f0, uint32_t f1, uint32_t f2) {
  const uint32_t freqs[3] = {f0, f1, f2};
  uint8_t mask = 0;
  for (uint8_t index = 0; index < kBuzzerCount; index++) {
    const uint32_t fr = freqs[index];
    ledcWriteTone(kBuzzerPins[index], fr);
    ledcWrite(kBuzzerPins[index], fr ? buzzerDuty() : 0);
    if (fr) {
      mask |= (1U << index);
    } else {
      digitalWrite(kBuzzerPins[index], LOW);
    }
  }
  currentToneHz = f0;
  currentToneMask = mask;
}

uint8_t jingleCount() { return kJingleCount; }
bool jingleActive() { return jinglePlaying; }

void playJingle(uint8_t index) {
  if (index >= kJingleCount) {
    return;
  }
  jingleIdx = index;
  jingleNote = 0;
  jingleNoteStartMs = millis();
  jinglePlaying = true;
  toneTestActive = false;
  liftAudioActive = false;
  sinkAudioActive = false;
  liftBeepOn = false;
  const JingleNote &n = kJingles[index].notes[0];
  setChord(n.f0, n.f1, n.f2);
}

void serviceJingle() {
  if (!jinglePlaying) {
    return;
  }
  const Jingle &tune = kJingles[jingleIdx];
  if (millis() - jingleNoteStartMs < tune.notes[jingleNote].ms) {
    return;
  }
  jingleNote++;
  if (jingleNote >= tune.len) {
    jinglePlaying = false;
    setToneMask(0, 0, false);
    return;
  }
  jingleNoteStartMs = millis();
  const JingleNote &n = tune.notes[jingleNote];
  setChord(n.f0, n.f1, n.f2);
}

void labTone(bool on, uint32_t freq, uint8_t mask, uint8_t duty) {
  buzzerLabActive = on;
  if (!on) {
    setToneMask(0, 0, false);  // resets currentTone state + silences
    return;
  }
  lastBuzzerLabMs = millis();
  freq = constrain(freq, 50U, 6000U);
  if (duty < 1) duty = 1;
  for (uint8_t i = 0; i < kBuzzerCount; i++) {
    const bool active = mask & (1U << i);
    ledcWriteTone(kBuzzerPins[i], active ? freq : 0);
    ledcWrite(kBuzzerPins[i], active ? duty : 0);
    if (!active) {
      digitalWrite(kBuzzerPins[i], LOW);
    }
  }
}

void updateVarioAudio() {
  const uint32_t now = millis();

  if (buzzerLabActive) {
    if (now - lastBuzzerLabMs <= 8000) {
      return;  // lab in control; keepalives keep it alive
    }
    labTone(false, 0, 0, 0);  // browser went away — release buzzers to the vario
  }

  if (jinglePlaying) {
    return;
  }

  if (updateToneTest()) {
    return;
  }

  if (!audioEnabled || !bmpWarmupComplete || !varioRateInitialized) {
    setTone(0);
    liftAudioActive = false;
    sinkAudioActive = false;
    liftBeepOn = false;
    return;
  }

  // Hysteresis off-thresholds are derived from the on-thresholds so the web
  // sliders stay a two-knob affair (climb on, sink on).
  const float liftOffMps = liftThresholdMps * 0.45F;
  const float sinkOffMps = sinkThresholdMps + 0.4F;

  if (!liftAudioActive && verticalSpeedMps >= liftThresholdMps) {
    liftAudioActive = true;
    sinkAudioActive = false;
    liftBeepOn = true;
    liftPhaseStartMs = now;
  } else if (liftAudioActive && verticalSpeedMps < liftOffMps) {
    liftAudioActive = false;
    liftBeepOn = false;
  }

  if (!sinkAudioActive && verticalSpeedMps <= sinkThresholdMps) {
    sinkAudioActive = true;
    liftAudioActive = false;
    liftBeepOn = false;
  } else if (sinkAudioActive && verticalSpeedMps > sinkOffMps) {
    sinkAudioActive = false;
  }

  // beepTempoPercent scales cadence: 200% = twice as fast (shorter phases).
  const uint32_t tempo = constrain(beepTempoPercent, static_cast<uint8_t>(50), static_cast<uint8_t>(200));

  if (liftAudioActive) {
    const float climb = clampFloat(verticalSpeedMps, 0.0F, 8.0F);
    uint32_t frequency =
        quantizeFrequency(liftFreqBaseHz + static_cast<uint32_t>(climb * liftFreqSlopeHz));
    const uint32_t beepMs = static_cast<uint32_t>(clampFloat(155.0F - climb * 15.0F, 65.0F, 155.0F)) * 100U / tempo;
    const uint32_t pauseMs = static_cast<uint32_t>(clampFloat(560.0F - climb * 75.0F, 95.0F, 560.0F)) * 100U / tempo;
    const uint32_t phaseMs = liftBeepOn ? beepMs : pauseMs;
    uint32_t phaseElapsed = now - liftPhaseStartMs;

    if (phaseElapsed >= phaseMs) {
      liftBeepOn = !liftBeepOn;
      liftPhaseStartMs = now;
      phaseElapsed = 0;
    }

    // Two-tone: second half of each beep steps up a major third (x5/4).
    if (twoToneLift && liftBeepOn && phaseElapsed >= phaseMs / 2) {
      frequency = quantizeFrequency(frequency * 5U / 4U);
    }
    setTone(liftBeepOn ? frequency : 0);
    return;
  }

  if (sinkAudioActive) {
    const float sink = clampFloat(-verticalSpeedMps, 0.0F, 8.0F);
    uint32_t frequency =
        quantizeFrequency(sinkFreqBaseHz - min(static_cast<uint32_t>(sink * kSinkFreqDecrementHzPerMps),
                                               static_cast<uint32_t>(sinkFreqBaseHz) / 2U));
    // Two-tone: warble between the tone and ~a minor third below, 160ms steps.
    if (twoToneSink && ((now / 160U) & 1U)) {
      frequency = quantizeFrequency(frequency * 5U / 6U);
    }
    setTone(frequency);
    return;
  }

  setTone(0);
}
