scottypres/Arduino-Paragliding-Varios/Sparkfun ESP32 WROOM Vario/Arduino Scripts/Sparkfun_Vario/gps_mod.h

#pragma once

#include "globals.h"

int gpsCustomInt(TinyGPSCustom &field);
int gpsSatellitesUsed();
int gpsSatellitesSeen();
String gpsSatSummary();
void setGpsEnabled(bool enabled);
void serviceGps();
void printGpsDebugIfDue();
